BailabUNC/LaHMo/results/revision/photo/DSC_0429.JPG

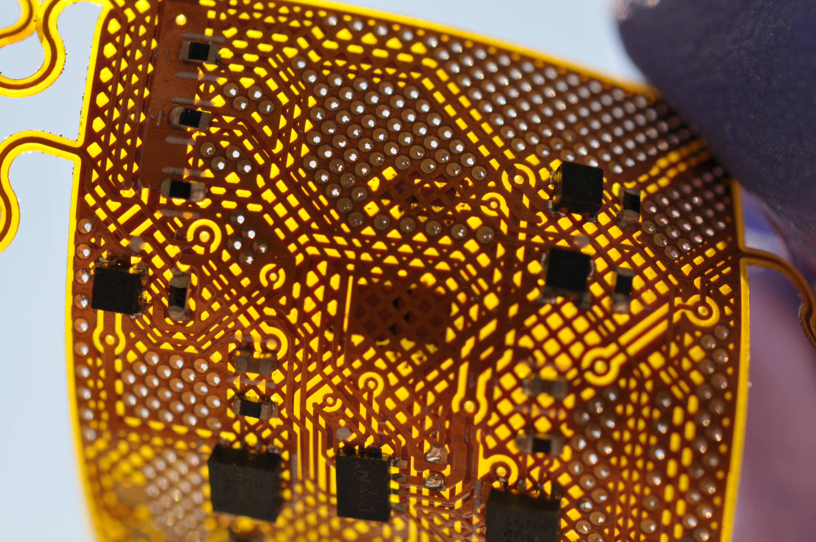
results/revision/photo/DSC_0429.JPG
