BailabUNC/LaHMo/results/revision/photo/DSC_0419.JPG

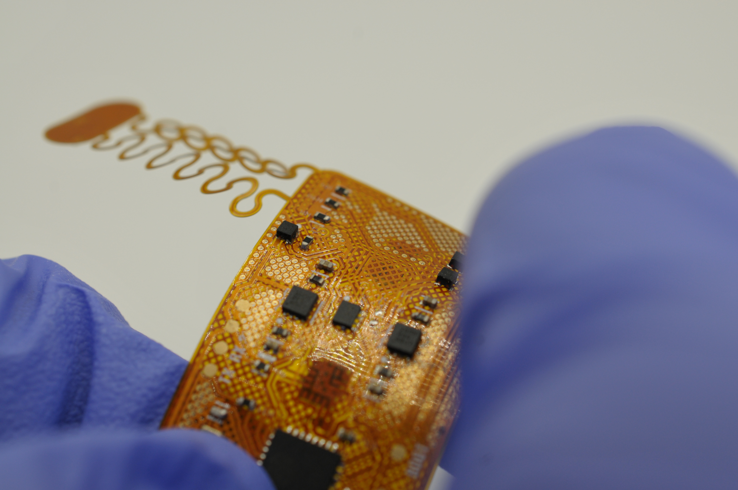
results/revision/photo/DSC_0419.JPG
