BailabUNC/LaHMo/results/revision/new tests/quality/c3_spec.png

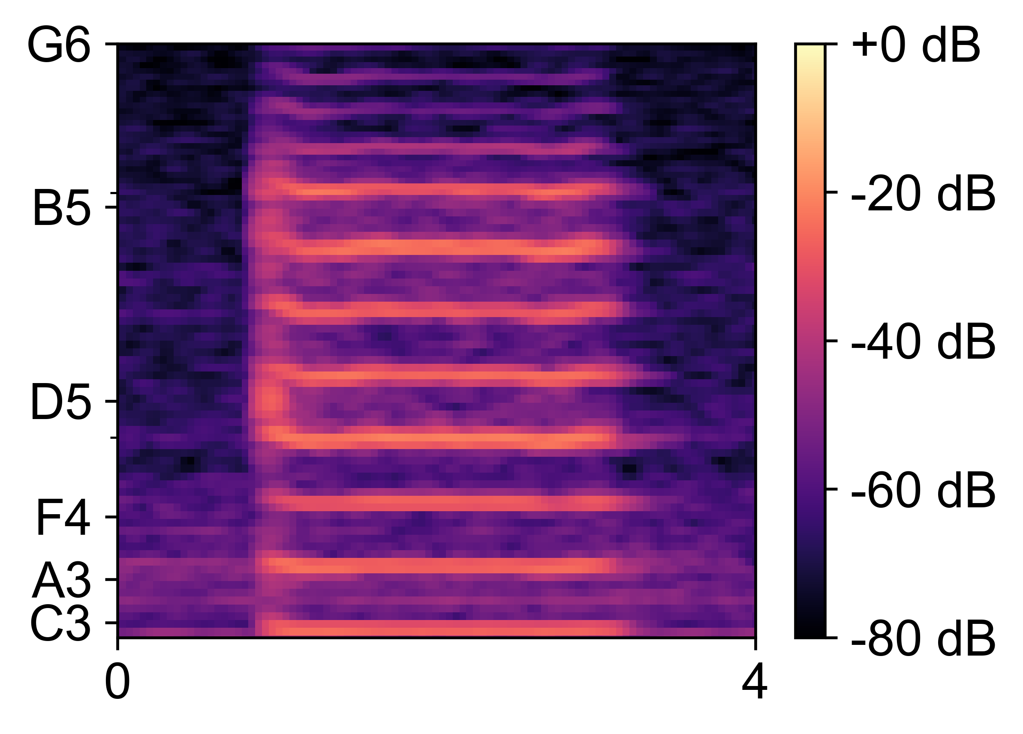
results/revision/new tests/quality/c3_spec.png
