BailabUNC/LaHMo/results/revision/new tests/quality/falsetto_spec.png

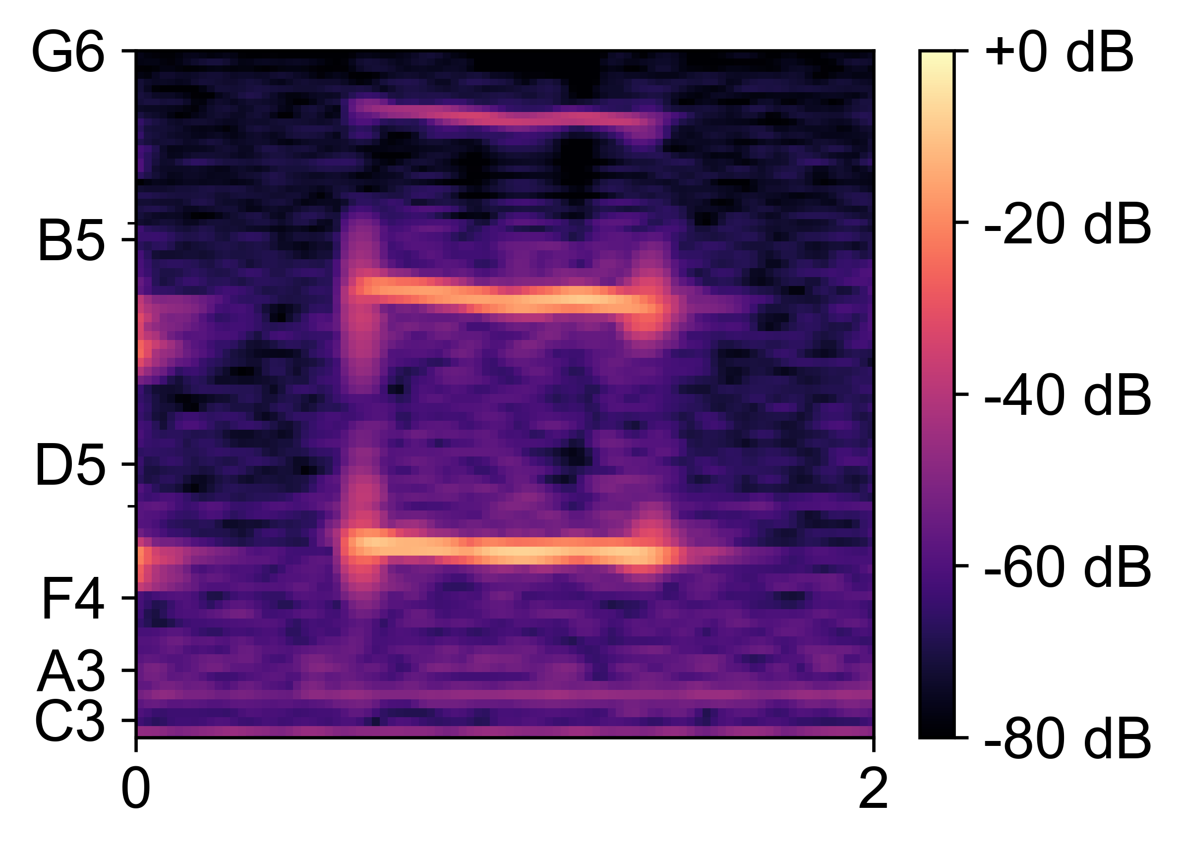
results/revision/new tests/quality/falsetto_spec.png
