BailabUNC/LaHMo/results/revision/new tests/quality/g3_spec.png

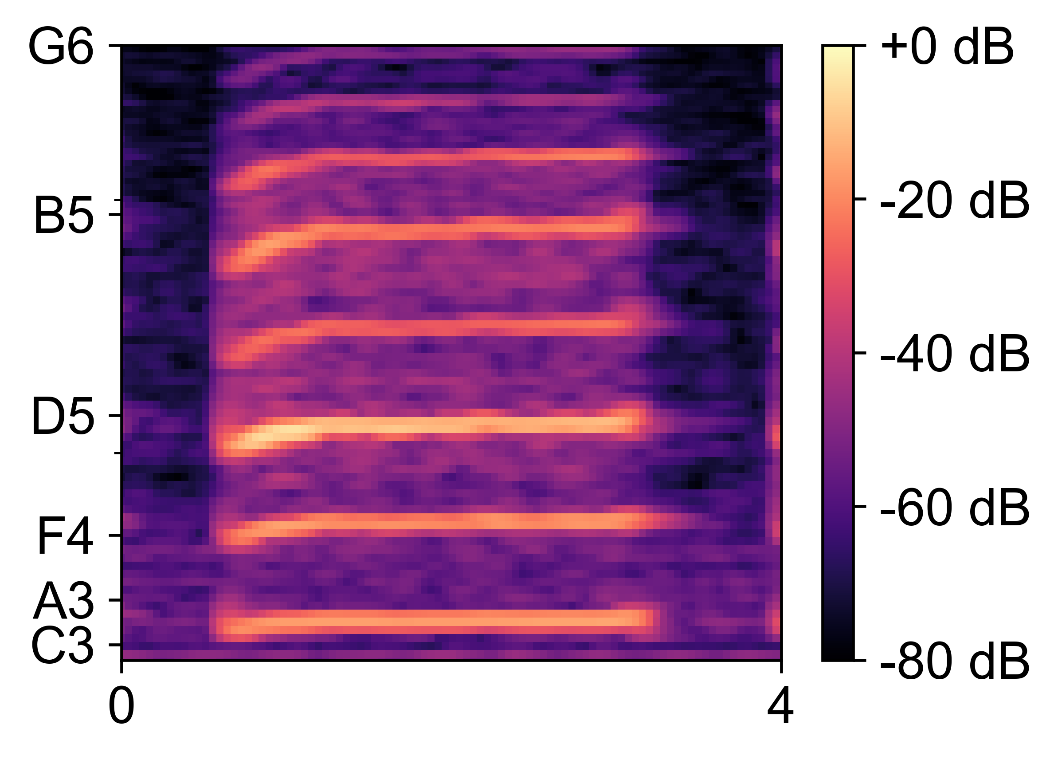
results/revision/new tests/quality/g3_spec.png
