BailabUNC/LaHMo/results/revision/new tests/quality/g4_spec.png

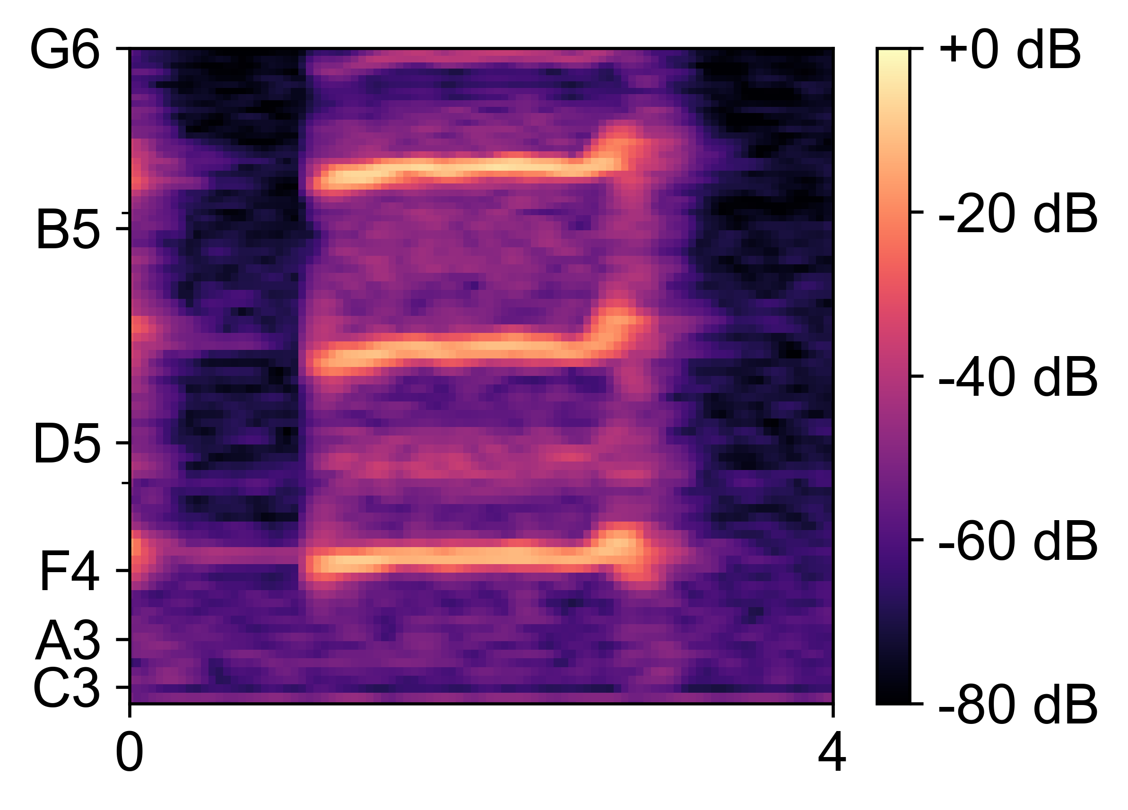
results/revision/new tests/quality/g4_spec.png
