BailabUNC/LaHMo/results/revision/new tests/quality/head_voice_spec.png

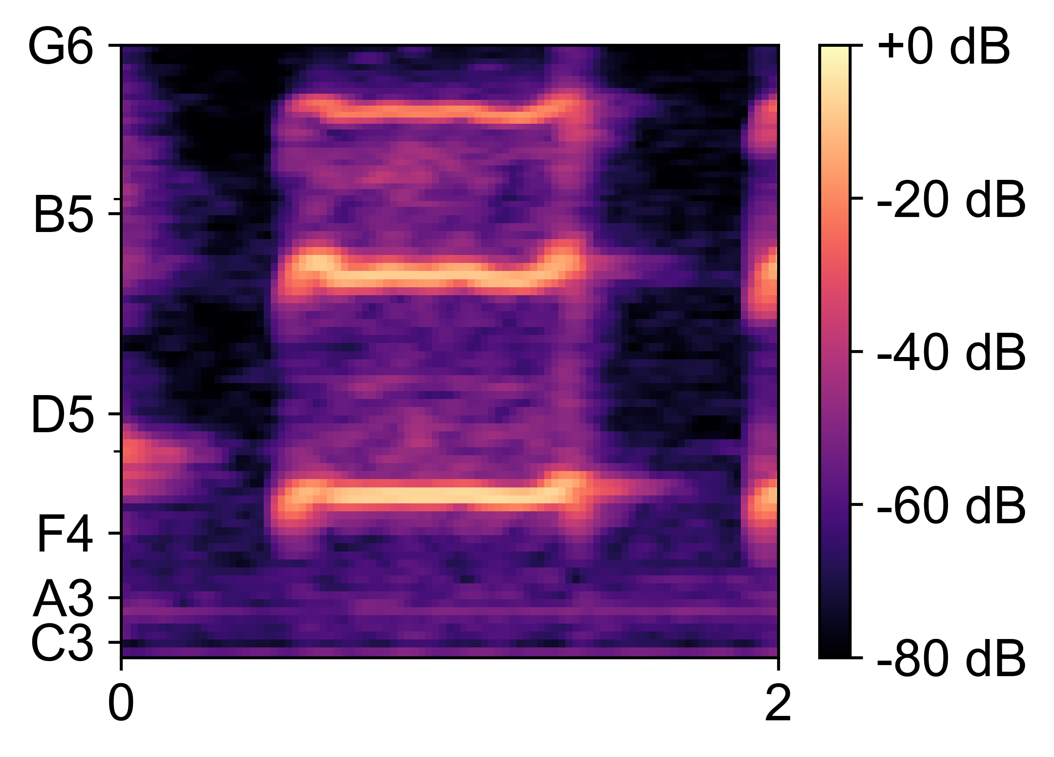
results/revision/new tests/quality/head_voice_spec.png
