BailabUNC/LaHMo/results/revision/new tests/quality/loud_spec.png

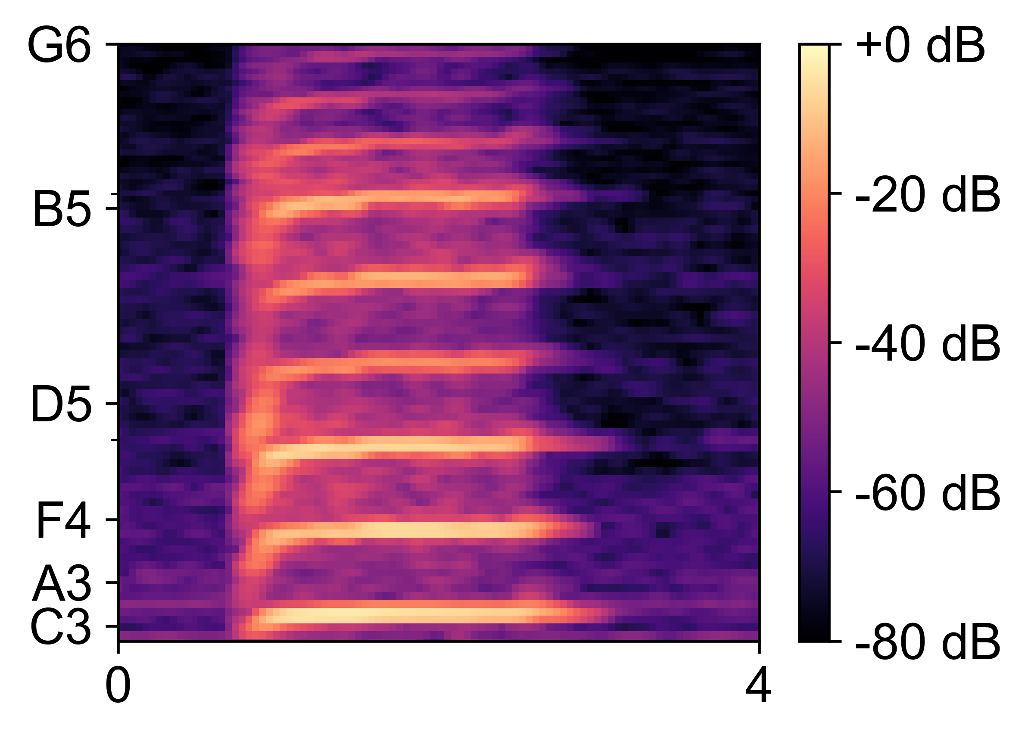
results/revision/new tests/quality/loud_spec.png
