BailabUNC/LaHMo/results/revision/new tests/quality/whisper_spec.png

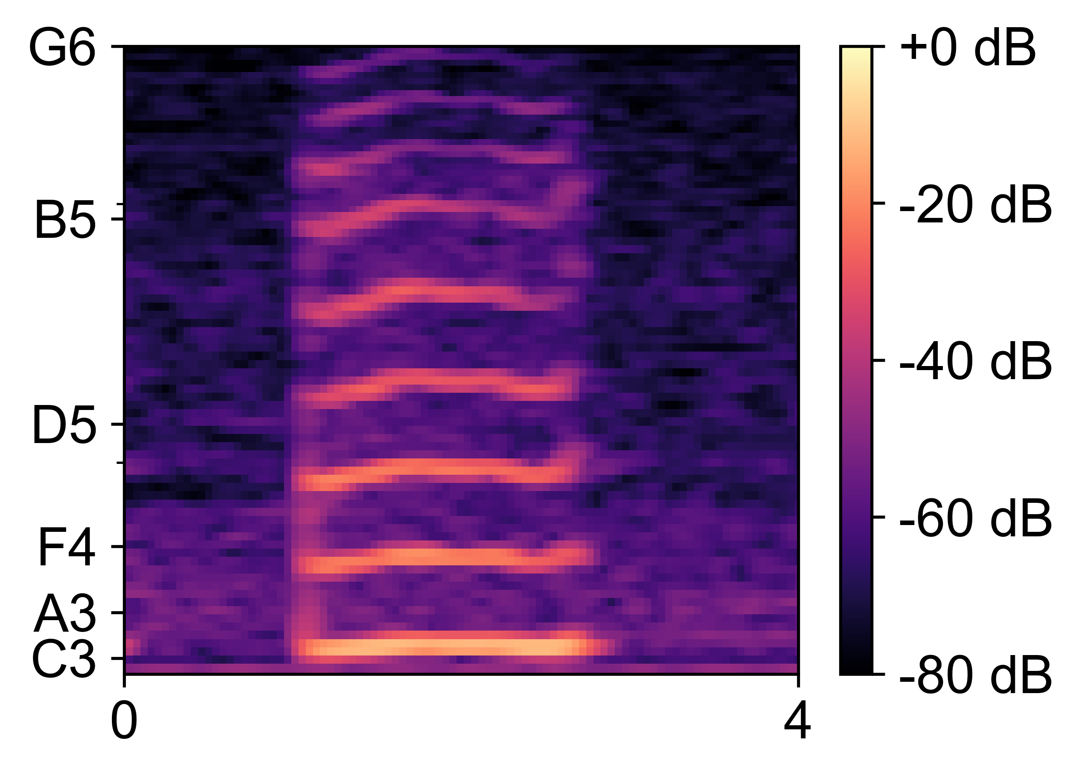
results/revision/new tests/quality/whisper_spec.png
