BailabUNC/LaHMo/results/revision/new tests/video/video1_spec.png

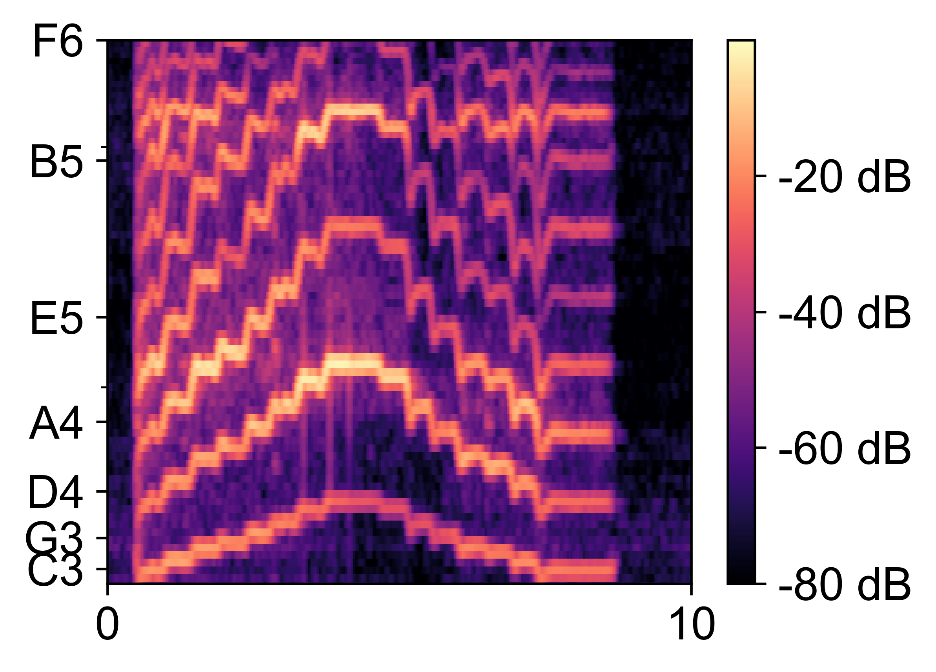
results/revision/new tests/video/video1_spec.png
