BailabUNC/LaHMo/results/revision/new tests/video/video2_spec.png

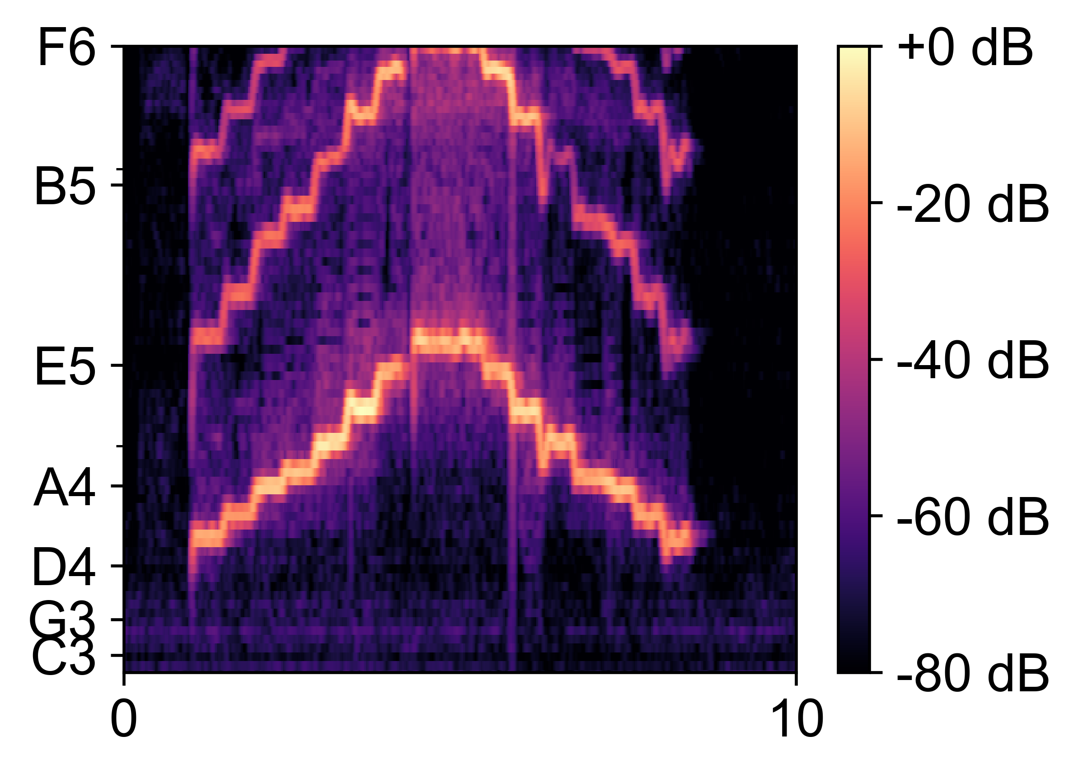
results/revision/new tests/video/video2_spec.png
