BailabUNC/LaHMo/results/fig2/preprocessing_steps/filtered_data.png

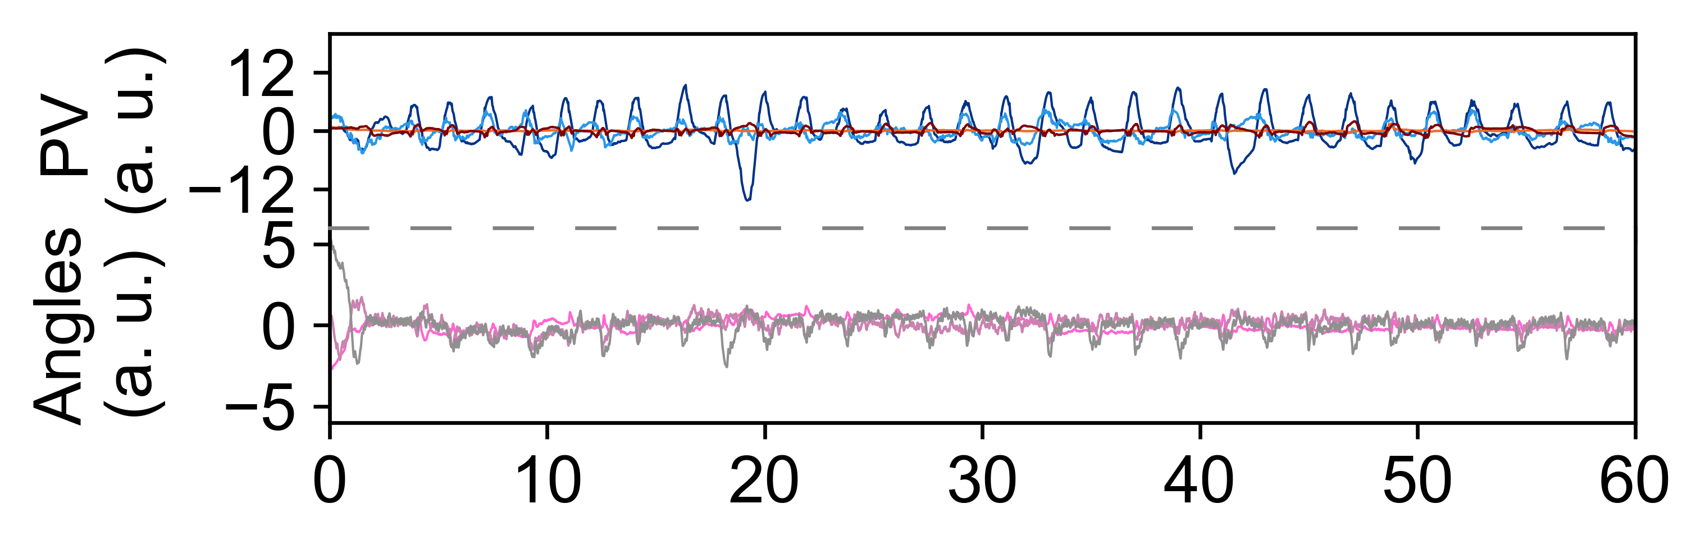
results/fig2/preprocessing_steps/filtered_data.png
