BailabUNC/LaHMo/results/fig2/preprocessing_steps/normalized_data.png

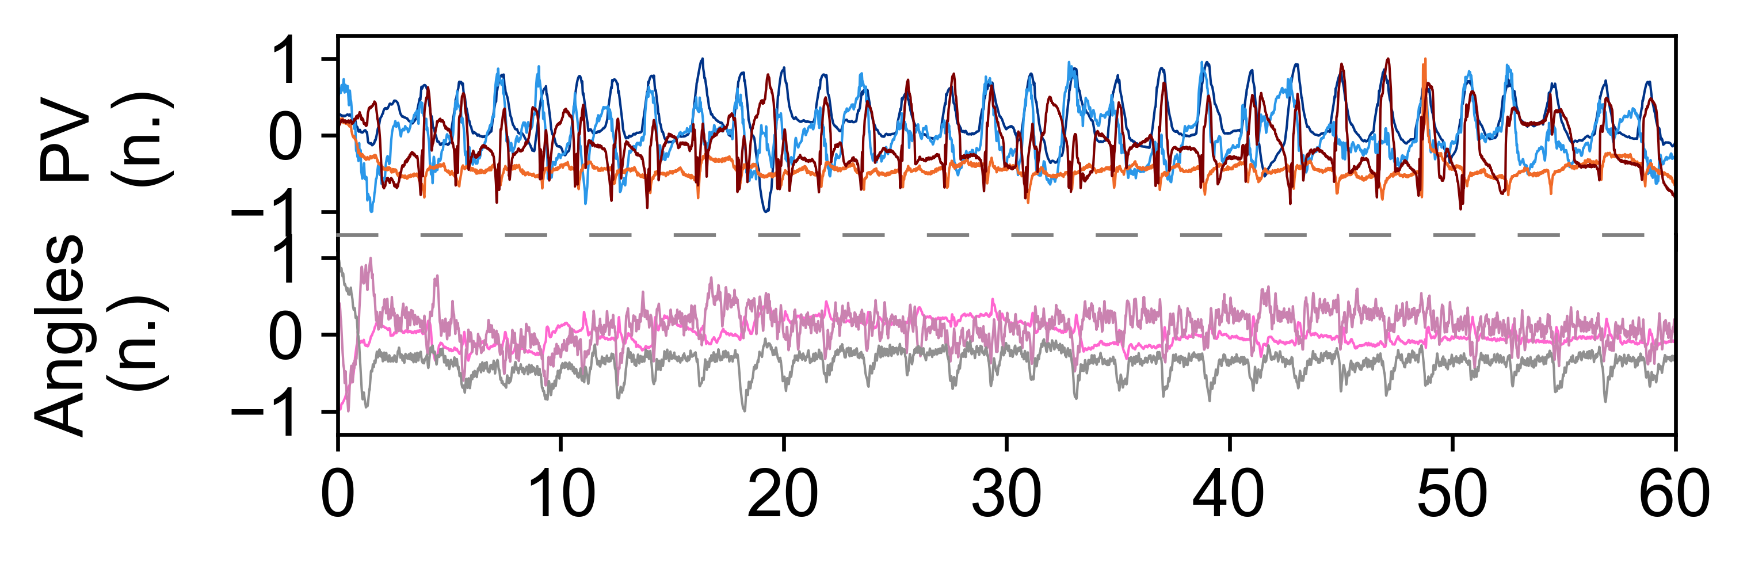
results/fig2/preprocessing_steps/normalized_data.png
