BailabUNC/LaHMo/results/fig2/preprocessing_steps/preprocessing_steps.png

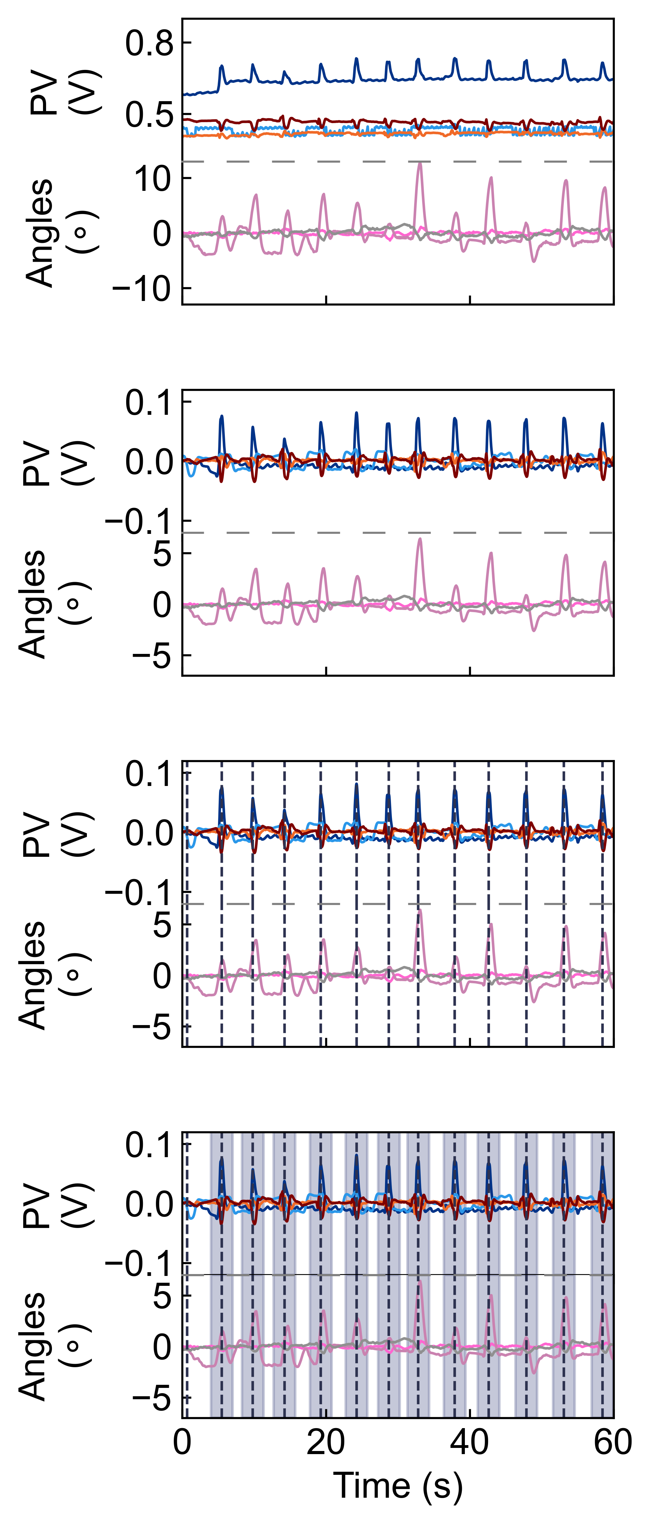
results/fig2/preprocessing_steps/preprocessing_steps.png
