BailabUNC/LaHMo/results/fig2/preprocessing_steps/preprocessing_steps_1.png

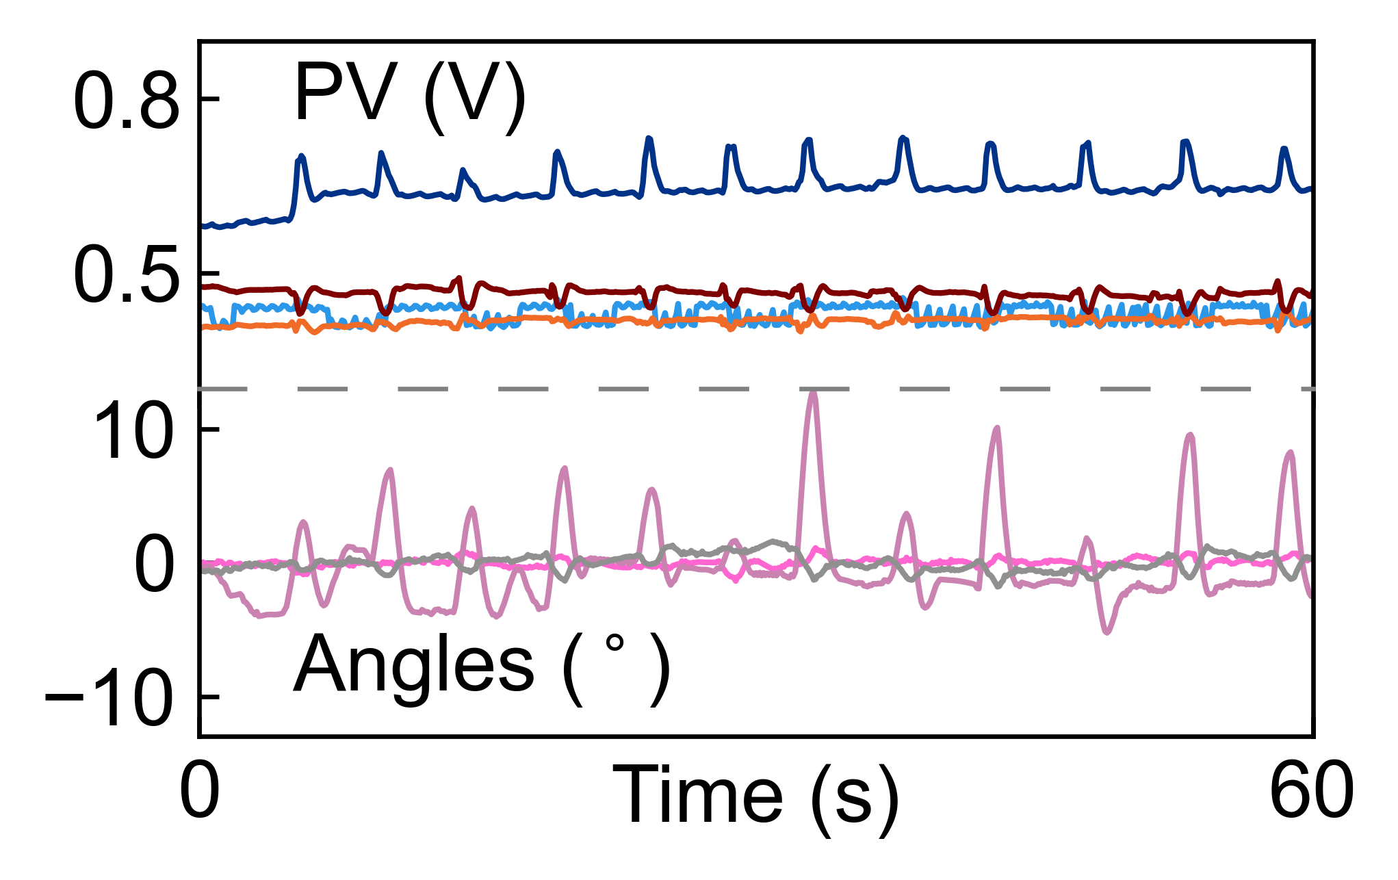
results/fig2/preprocessing_steps/preprocessing_steps_1.png
