BailabUNC/LaHMo/results/fig2/preprocessing_steps/preprocessing_steps_2.png

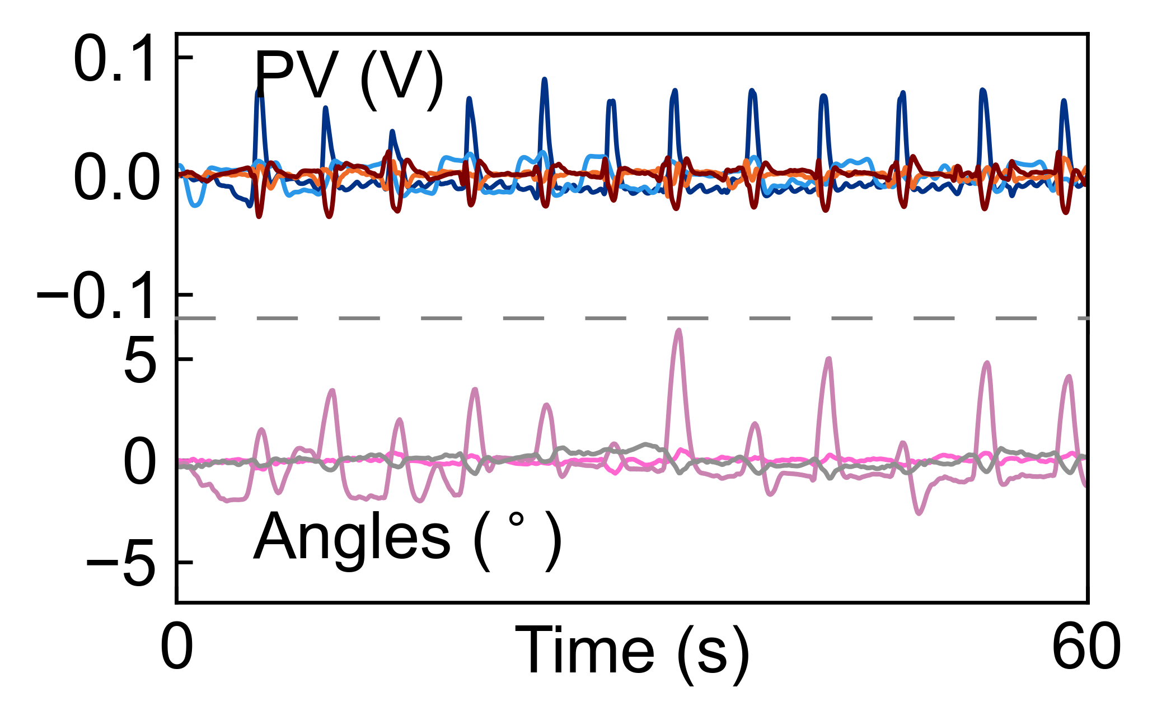
results/fig2/preprocessing_steps/preprocessing_steps_2.png
