BailabUNC/LaHMo/results/fig2/preprocessing_steps/preprocessing_steps_3.png

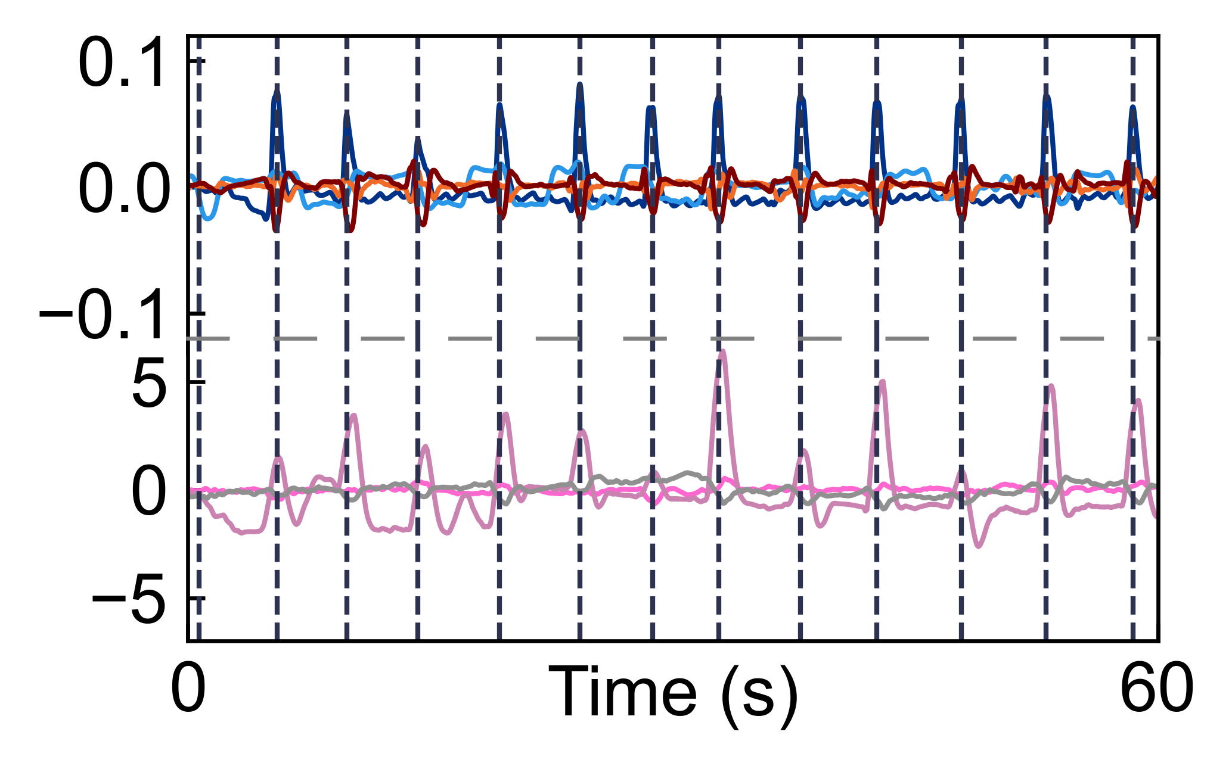
results/fig2/preprocessing_steps/preprocessing_steps_3.png
