BailabUNC/LaHMo/results/fig2/preprocessing_steps/raw_data.png

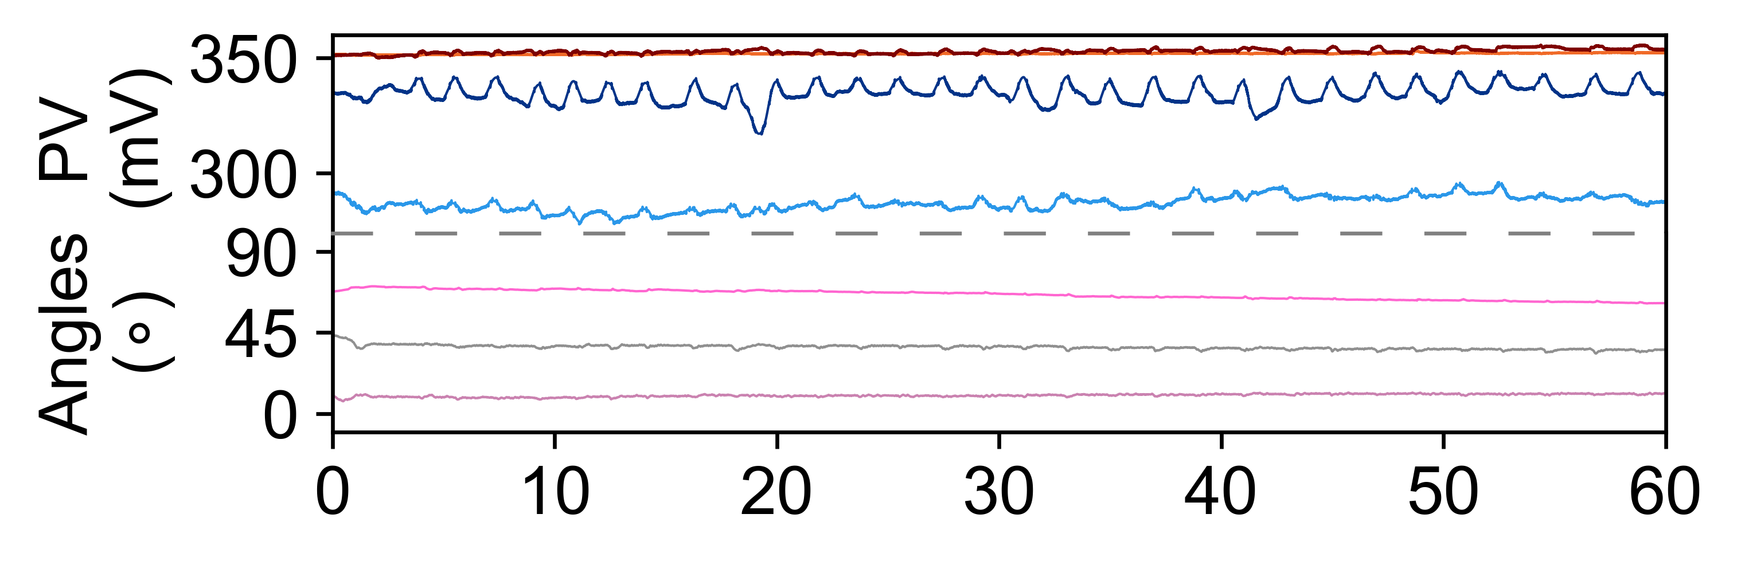
results/fig2/preprocessing_steps/raw_data.png
