BailabUNC/LaHMo/results/fig2/preprocessing_steps/selected_data.png

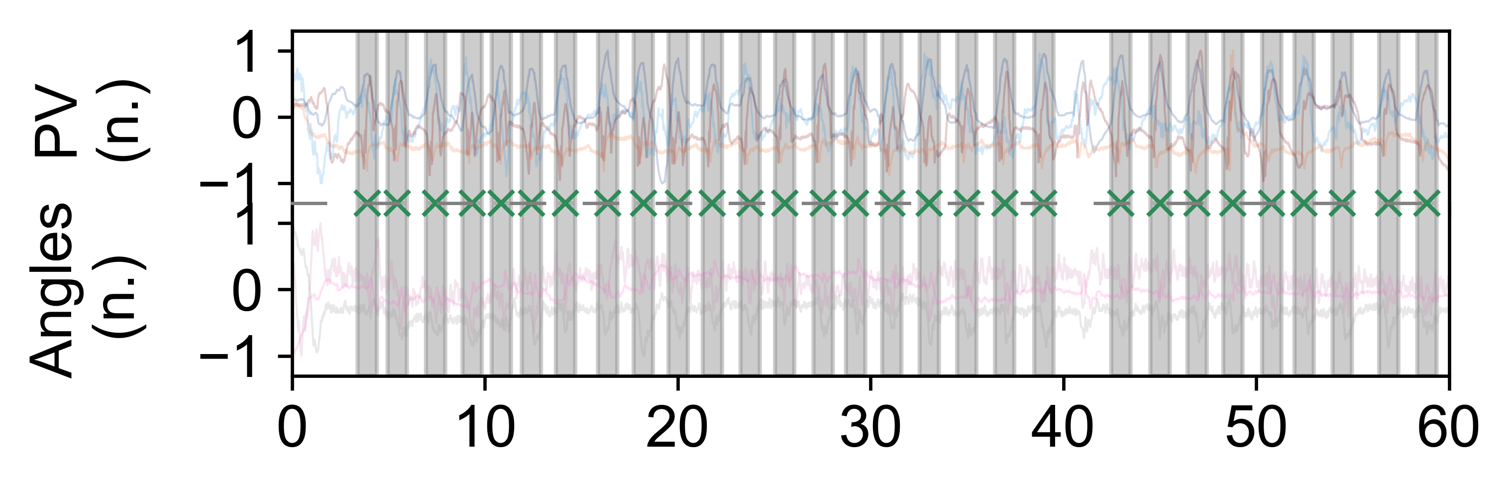
results/fig2/preprocessing_steps/selected_data.png
