BailabUNC/LaHMo/monte-carlo/monte-carlo/result/bump_loc_height_matrix.png

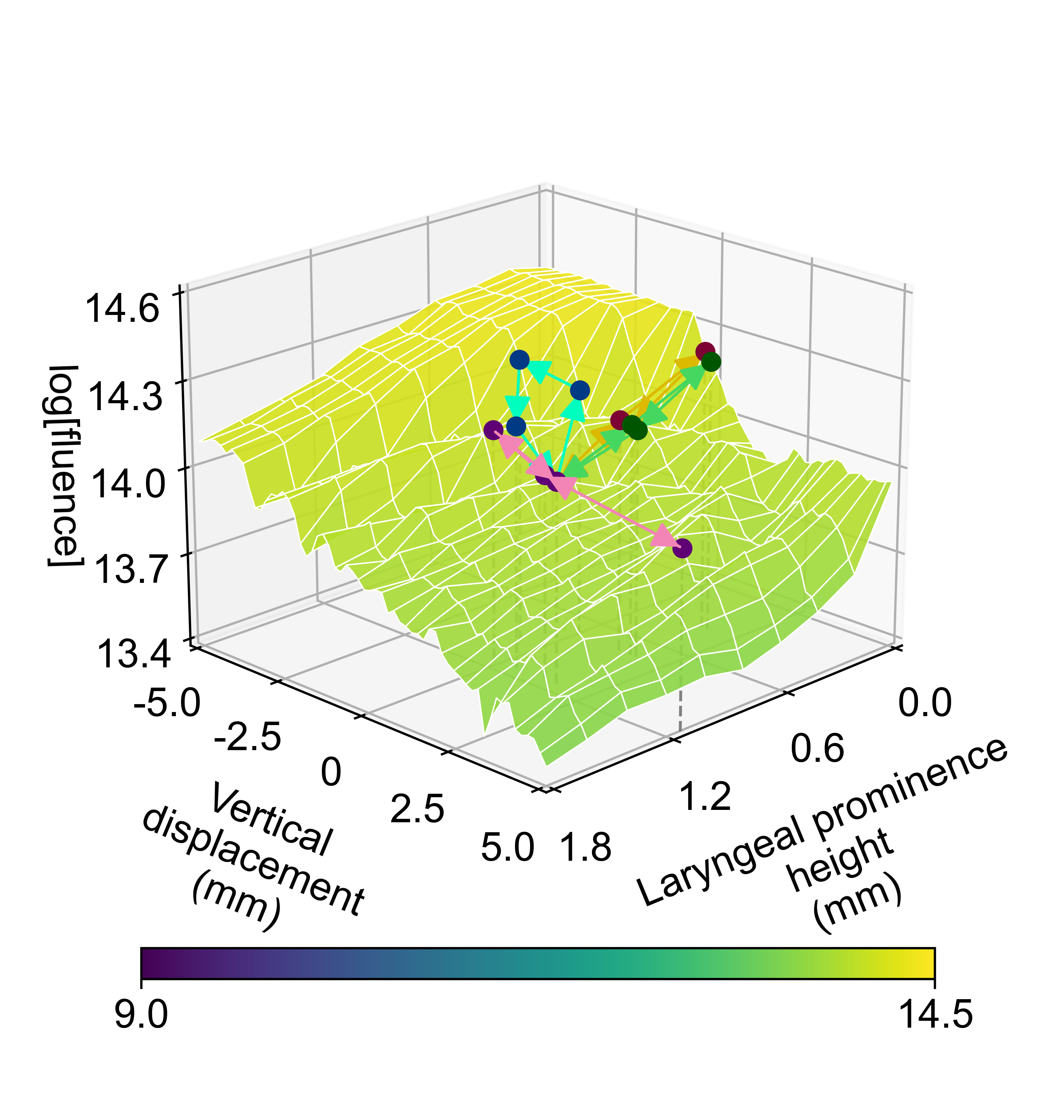
monte-carlo/monte-carlo/result/bump_loc_height_matrix.png
