BailabUNC/LaHMo/monte-carlo/monte-carlo/result/damping_scatter_0_0_1000.png

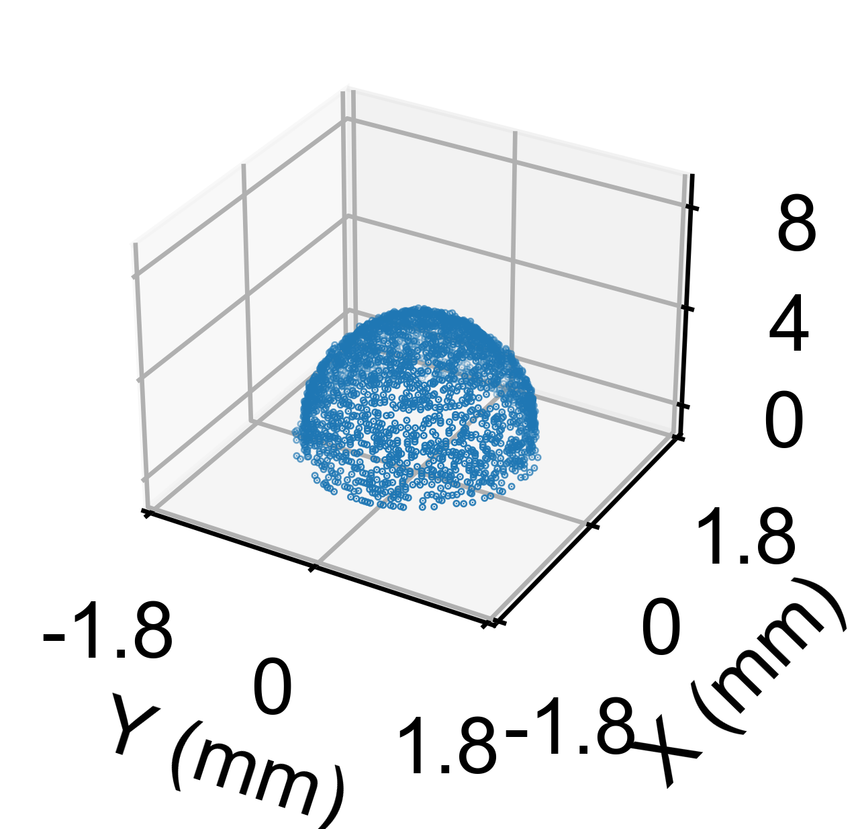
monte-carlo/monte-carlo/result/damping_scatter_0_0_1000.png
