BailabUNC/LaHMo/monte-carlo/monte-carlo/result/dry_cough_cycle.png

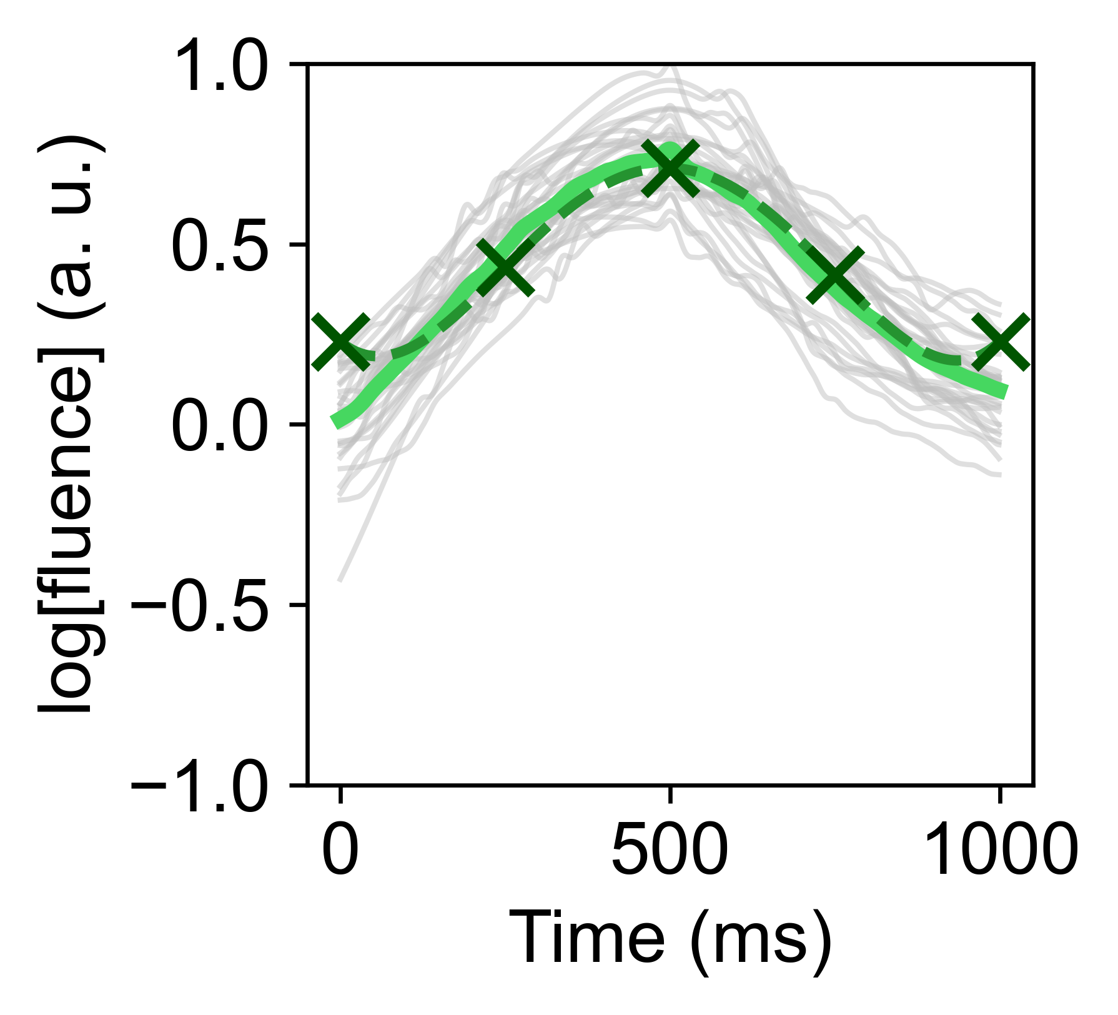
monte-carlo/monte-carlo/result/dry_cough_cycle.png
