BailabUNC/LaHMo/monte-carlo/monte-carlo/result/dry_cough_profile.png

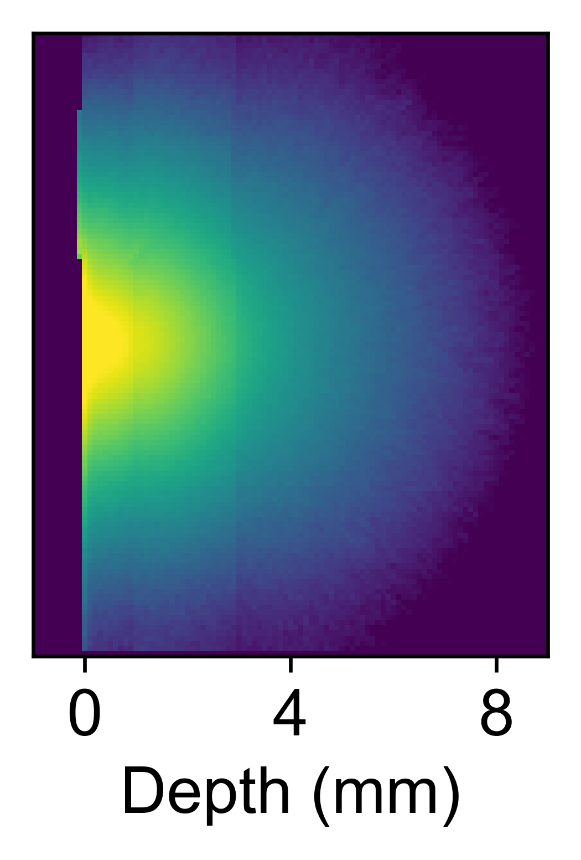
monte-carlo/monte-carlo/result/dry_cough_profile.png
