BailabUNC/LaHMo/monte-carlo/monte-carlo/result/swallow_profile.png

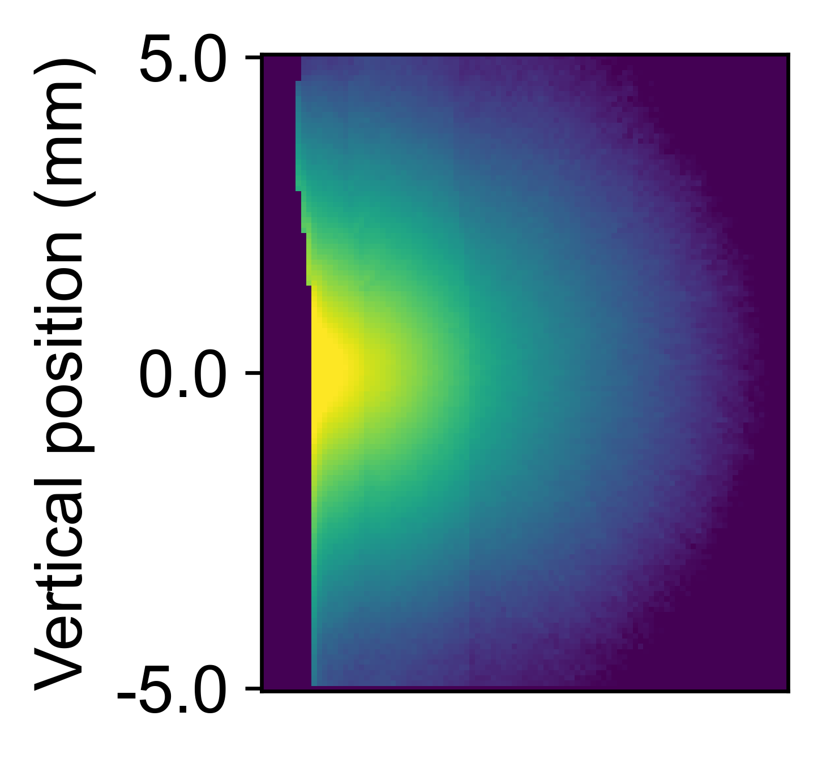
monte-carlo/monte-carlo/result/swallow_profile.png
