BailabUNC/LaHMo/monte-carlo/monte-carlo/result/throat_clear_cycle.png

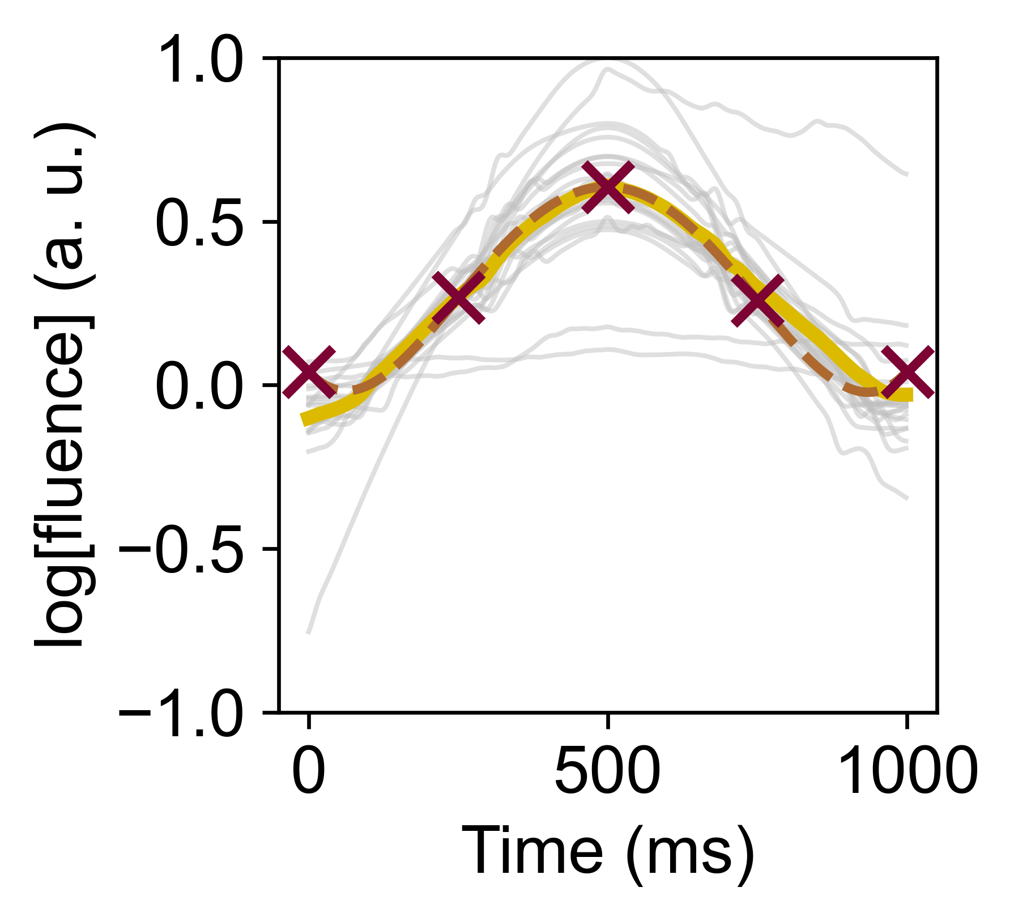
monte-carlo/monte-carlo/result/throat_clear_cycle.png
