BailabUNC/LaHMo/monte-carlo/monte-carlo/result/throat_clear_profile.png

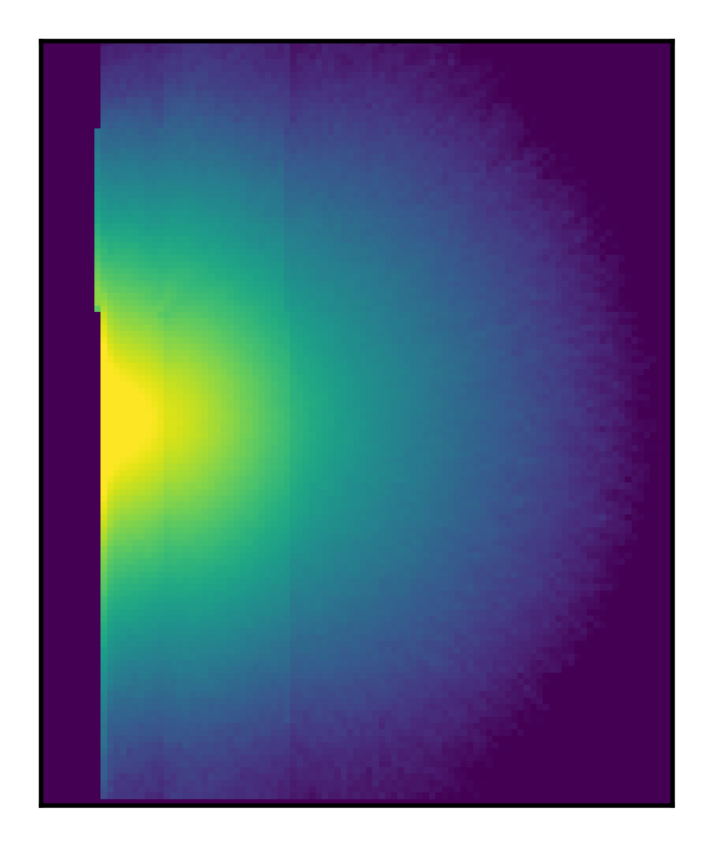
monte-carlo/monte-carlo/result/throat_clear_profile.png
