BailabUNC/LaHMo/monte-carlo/monte-carlo/result/walking_cycle.png

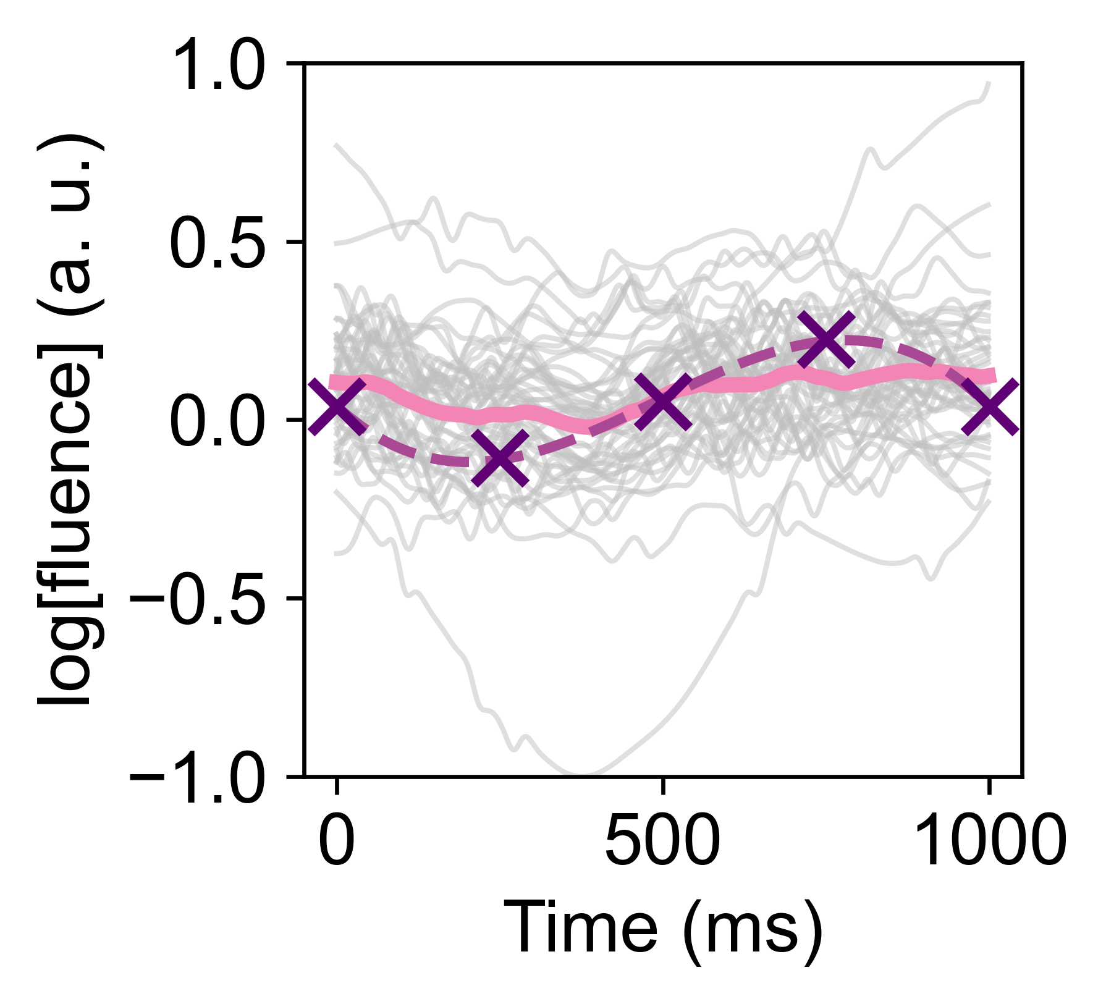
monte-carlo/monte-carlo/result/walking_cycle.png
