BailabUNC/LaHMo/monte-carlo/monte-carlo/result/walking_profile.png

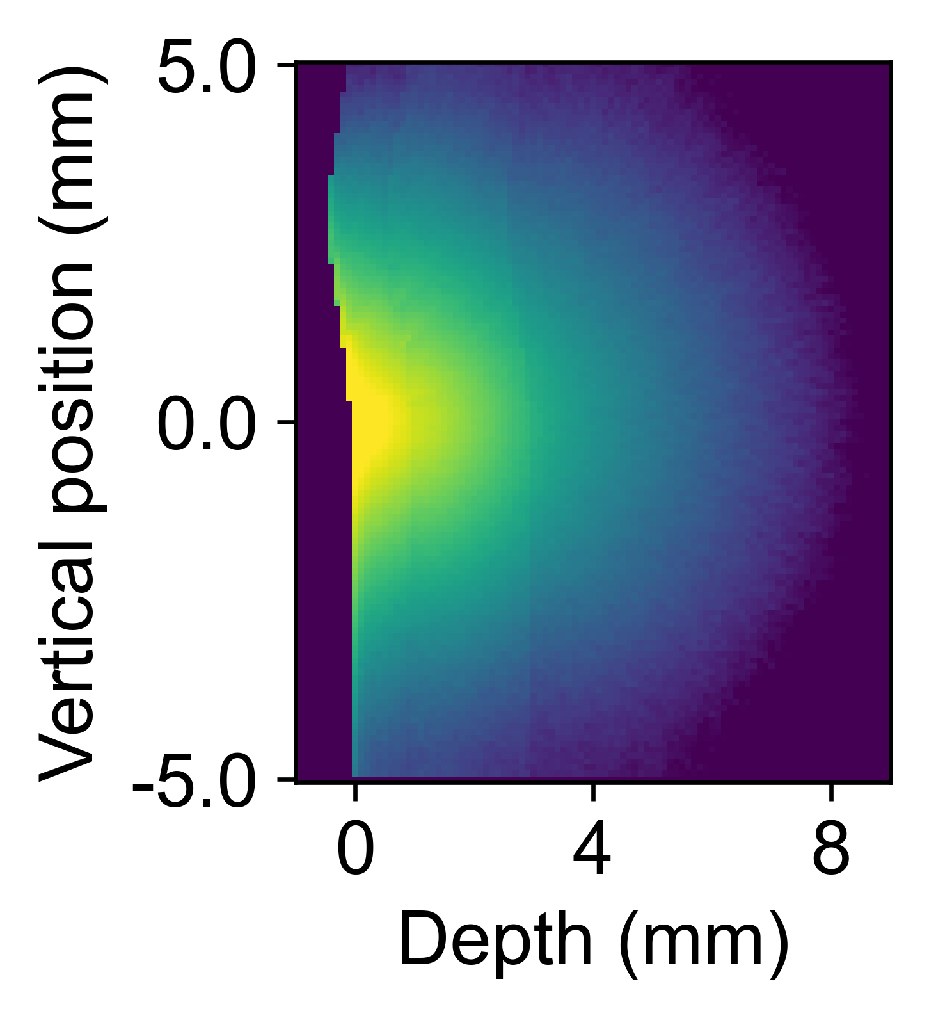
monte-carlo/monte-carlo/result/walking_profile.png
