BailabUNC/LaHMo/results/fig1/2.png

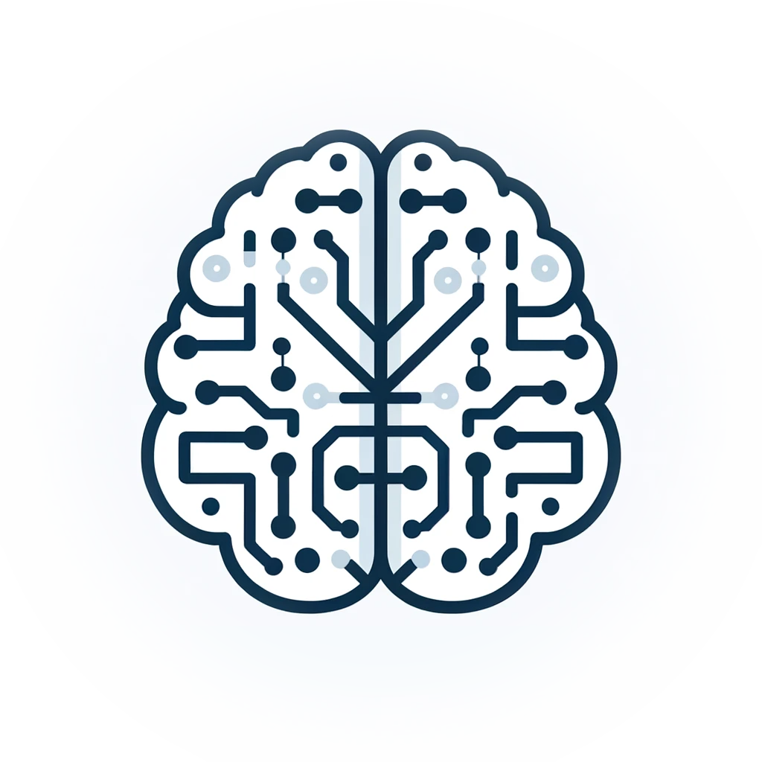
results/fig1/2.png
