BailabUNC/LaHMo/results/fig1/3.png

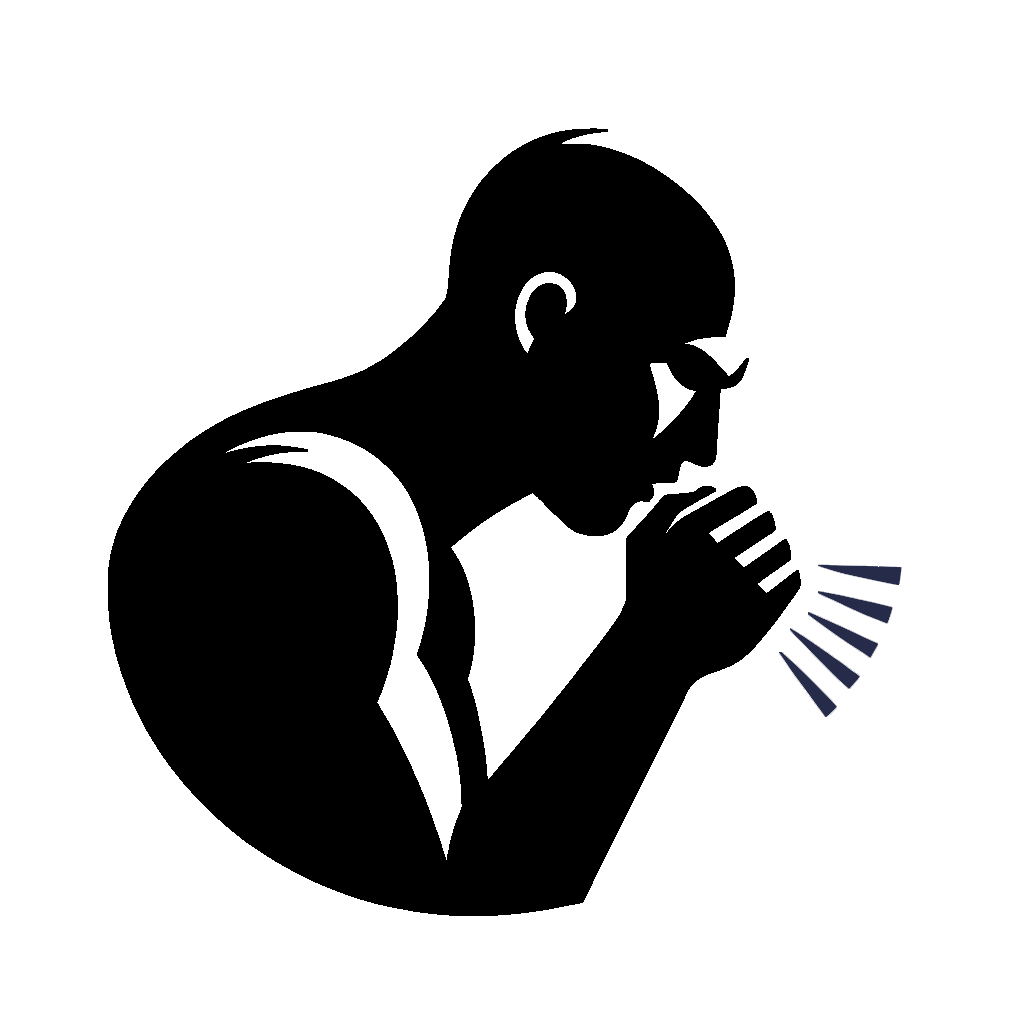
results/fig1/3.png
