BailabUNC/LaHMo/results/fig1/4.png

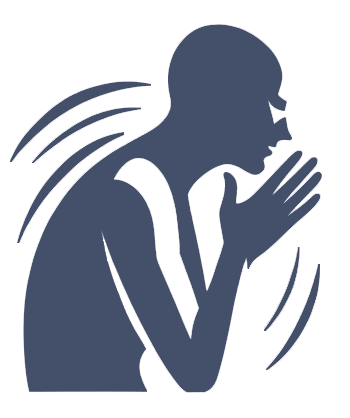
results/fig1/4.png
