BailabUNC/LaHMo/results/fig1/5.png

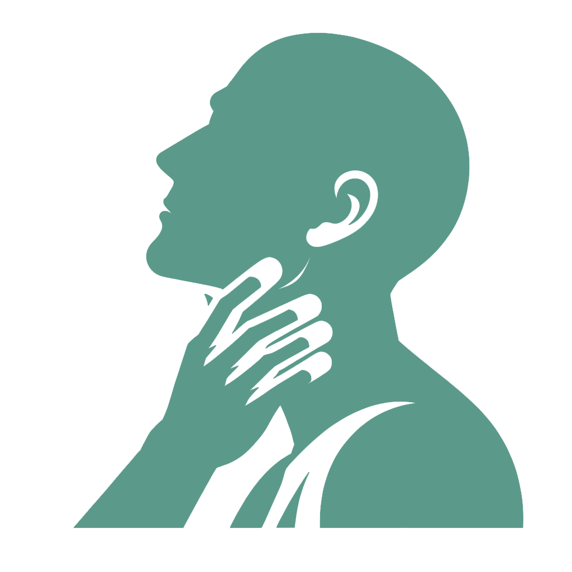
results/fig1/5.png
