BailabUNC/LaHMo/results/fig1/6.png

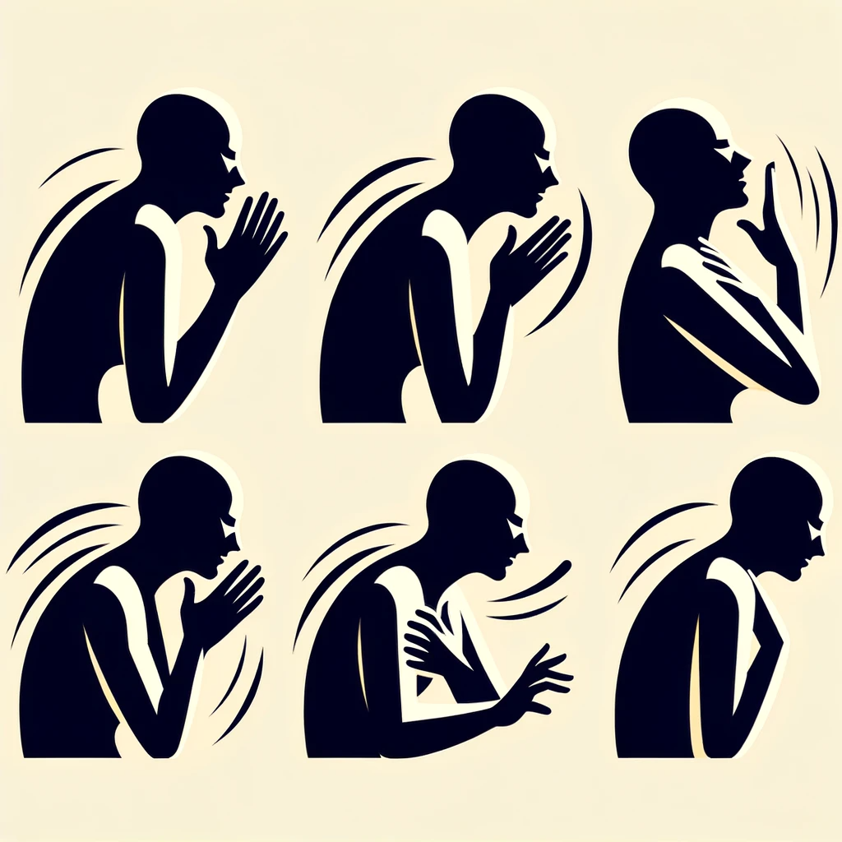
results/fig1/6.png
