BailabUNC/LaHMo/results/fig1/7.png

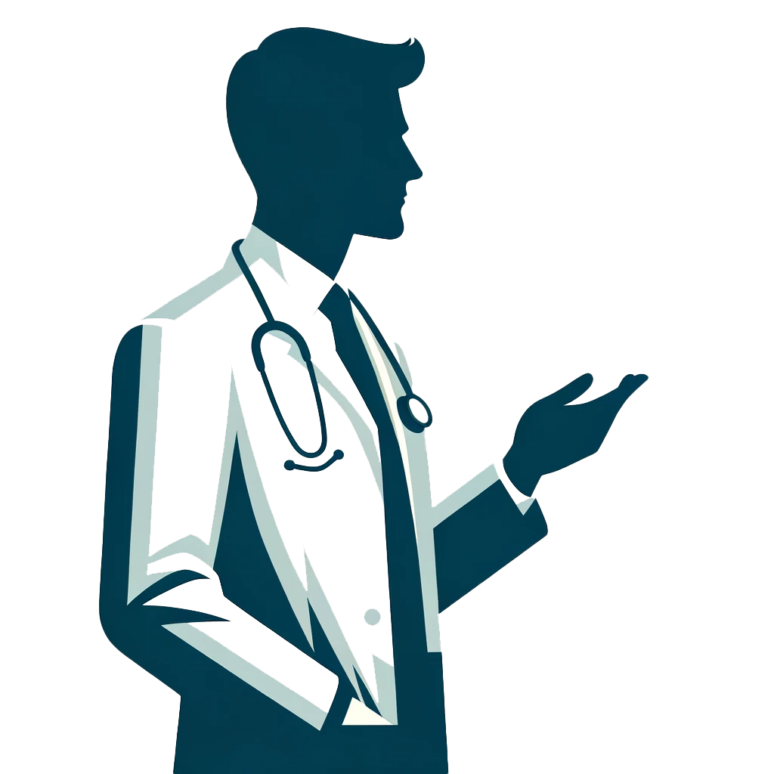
results/fig1/7.png
