BailabUNC/LaHMo/results/fig1/exploded.jpg

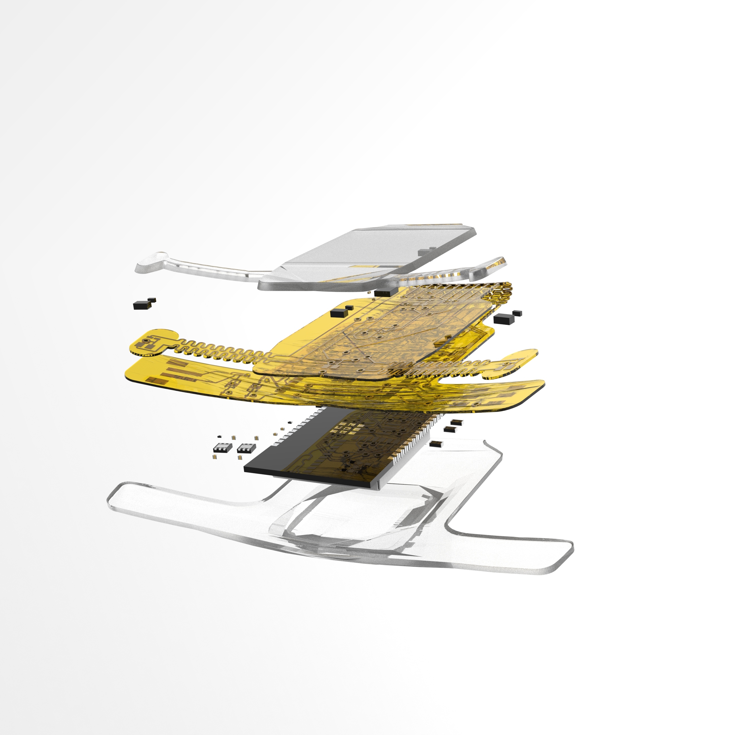
results/fig1/exploded.jpg
