BailabUNC/LaHMo/results/fig1/P3.png

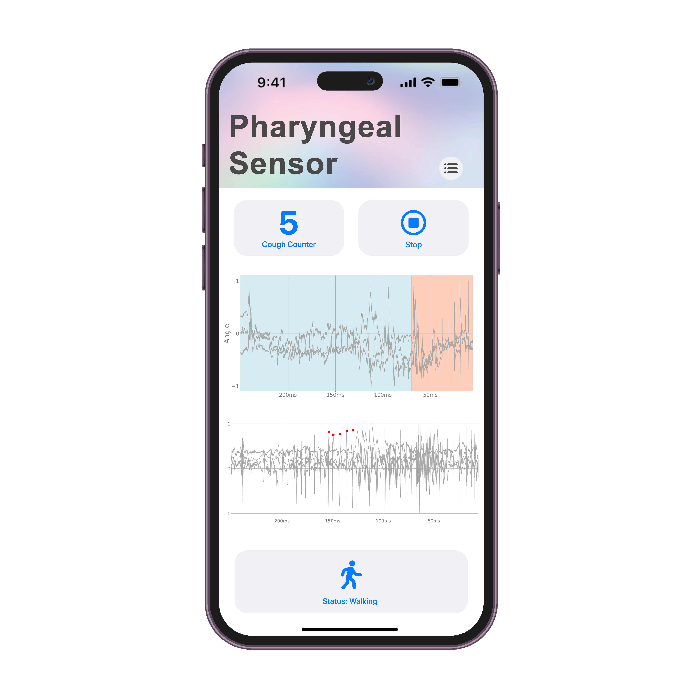
results/fig1/P3.png
