BailabUNC/LaHMo/results/fig1/stacked.2.jpg

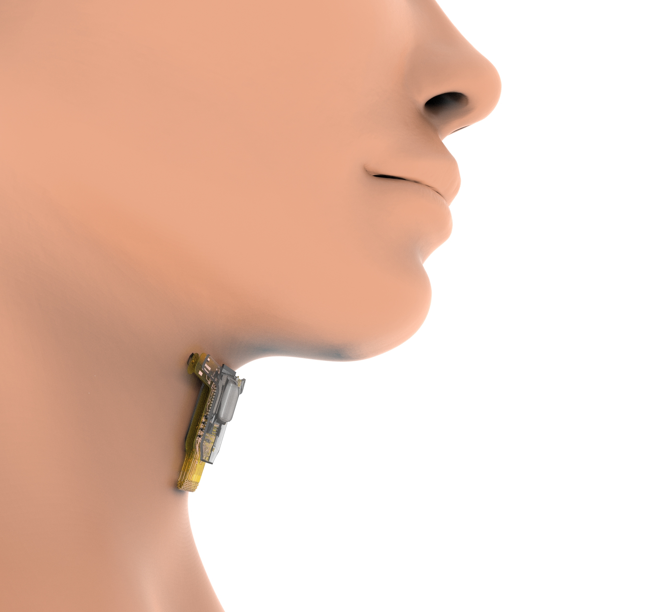
results/fig1/stacked.2.jpg
