BailabUNC/LaHMo/results/fig2/device.png

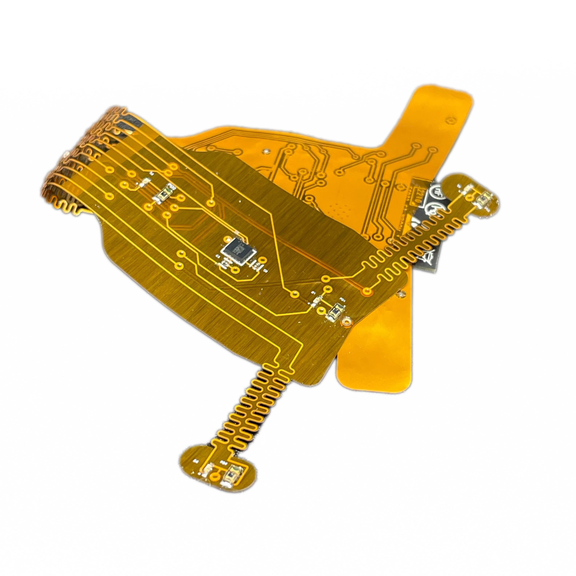
results/fig2/device.png
