BailabUNC/LaHMo/results/fig2/IMG_6159.jpg

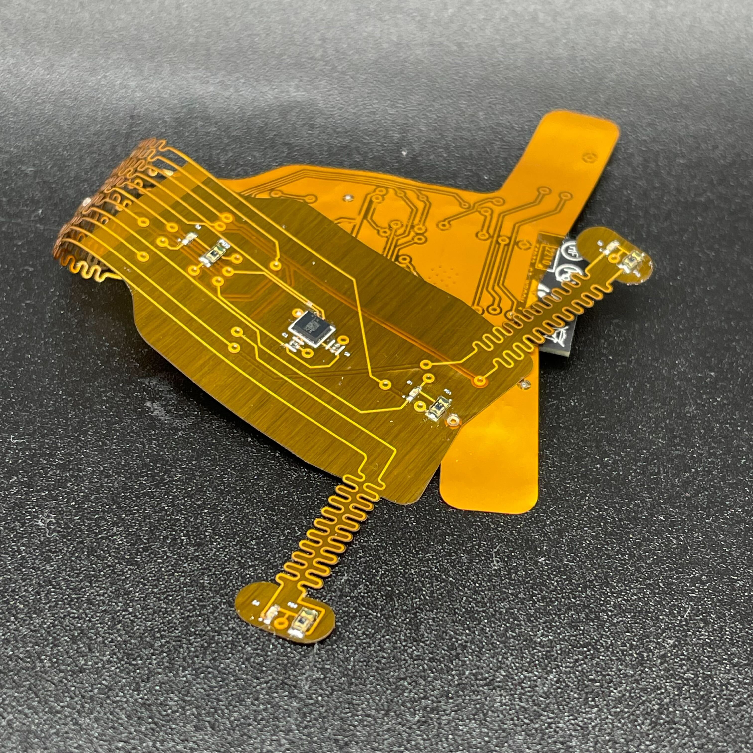
results/fig2/IMG_6159.jpg
