BailabUNC/LaHMo/results/fig2/imu.4.jpg

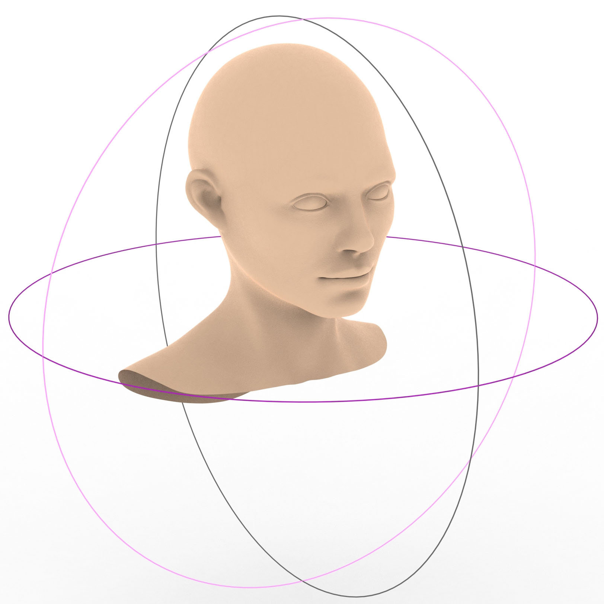
results/fig2/imu.4.jpg
