BailabUNC/LaHMo/results/fig2/map.3.jpg

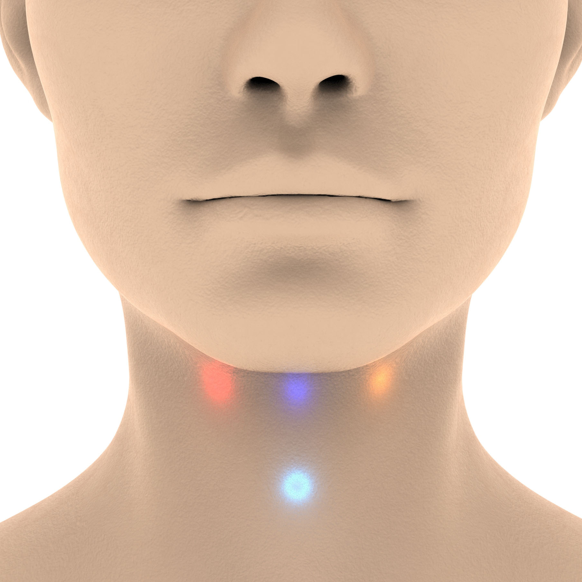
results/fig2/map.3.jpg
