BailabUNC/LaHMo/results/fig2/preprocessed/all.png

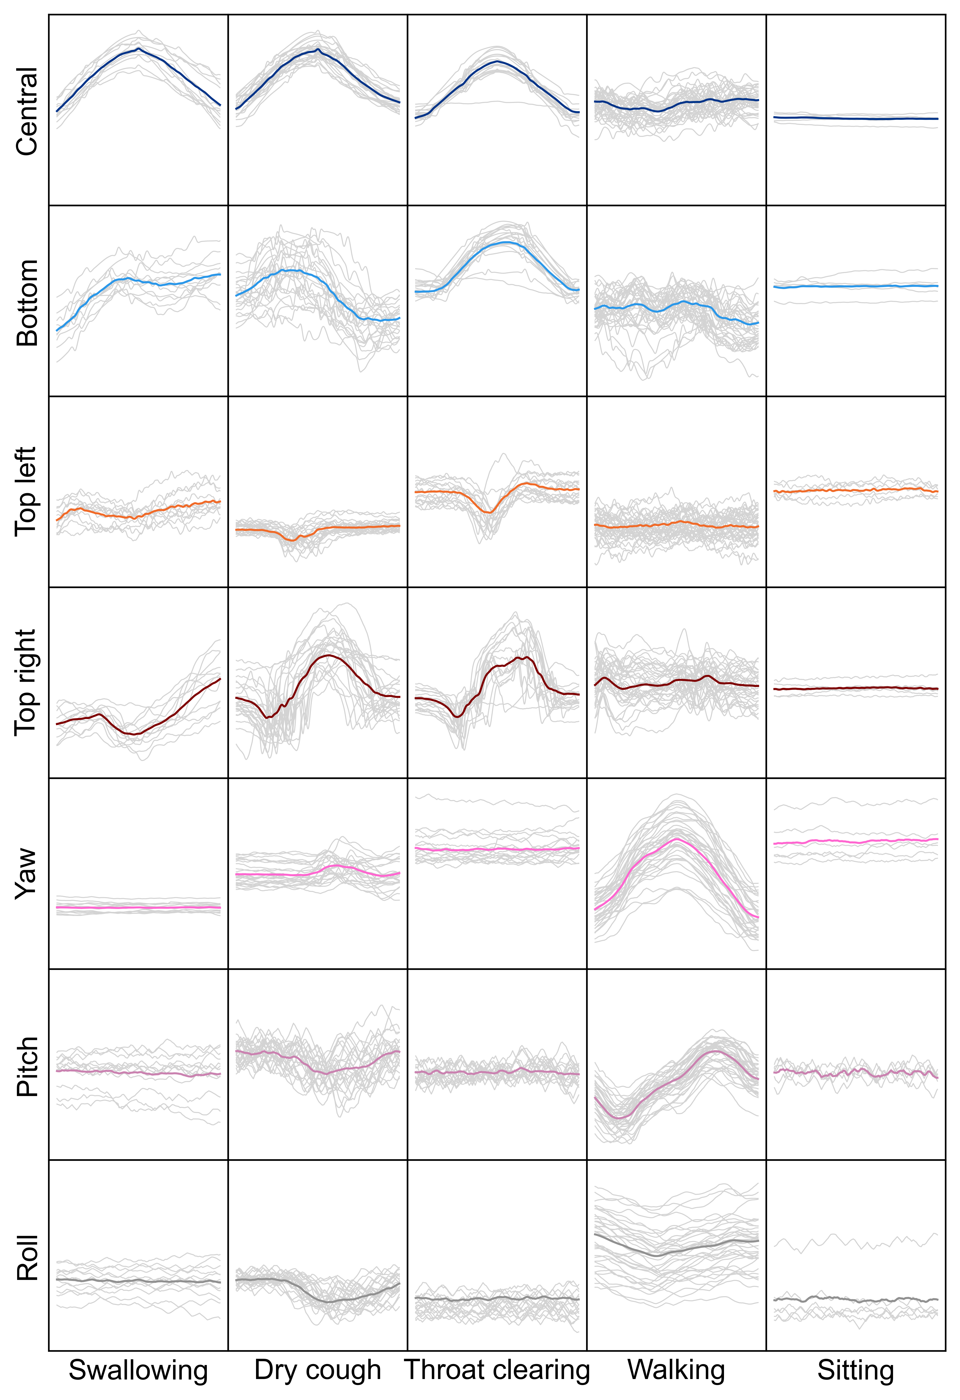
results/fig2/preprocessed/all.png
