BailabUNC/LaHMo/results/fig3/acc_all_frnn.png

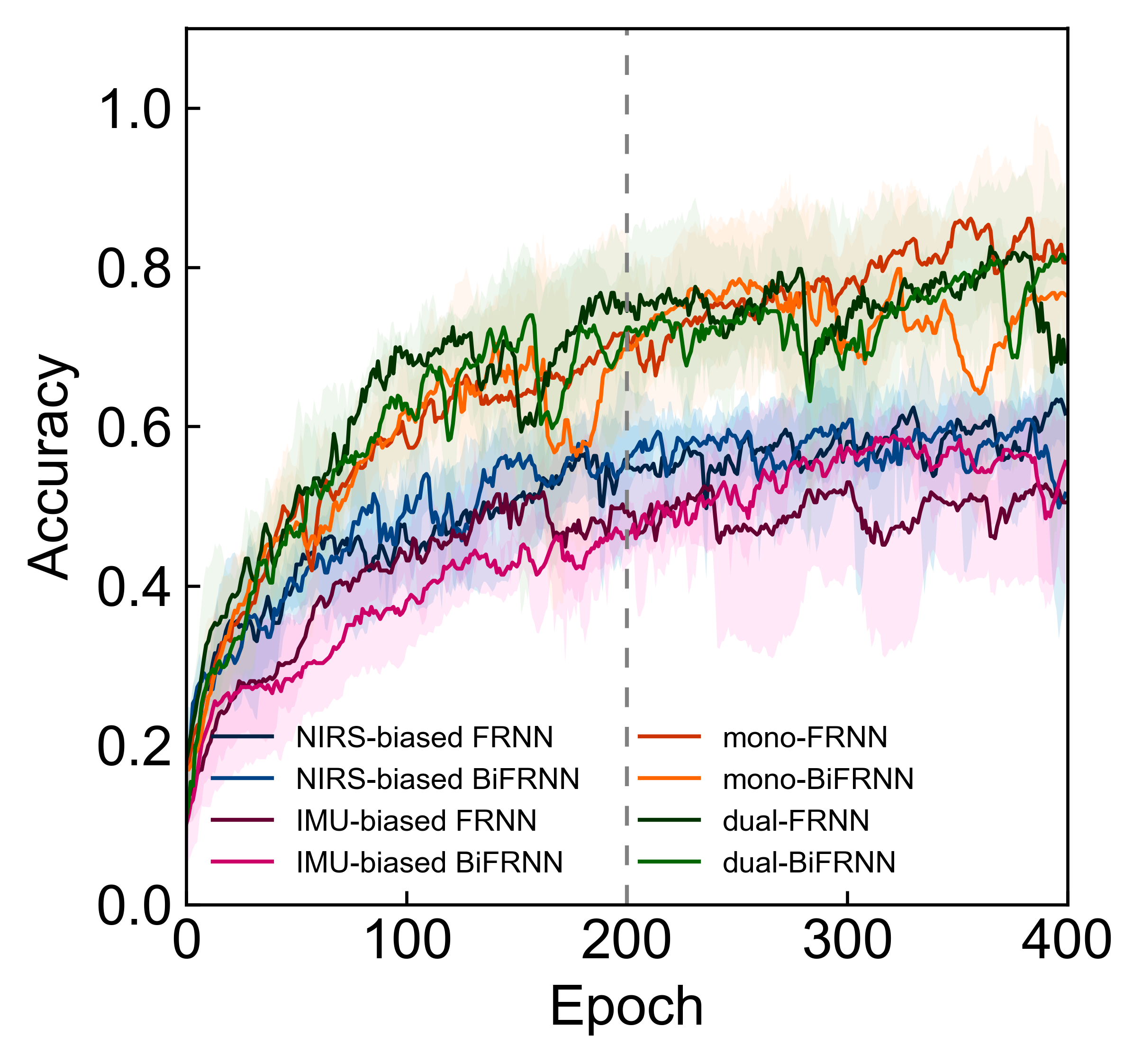
results/fig3/acc_all_frnn.png
