BailabUNC/LaHMo/results/fig3/acc_all_gru.png

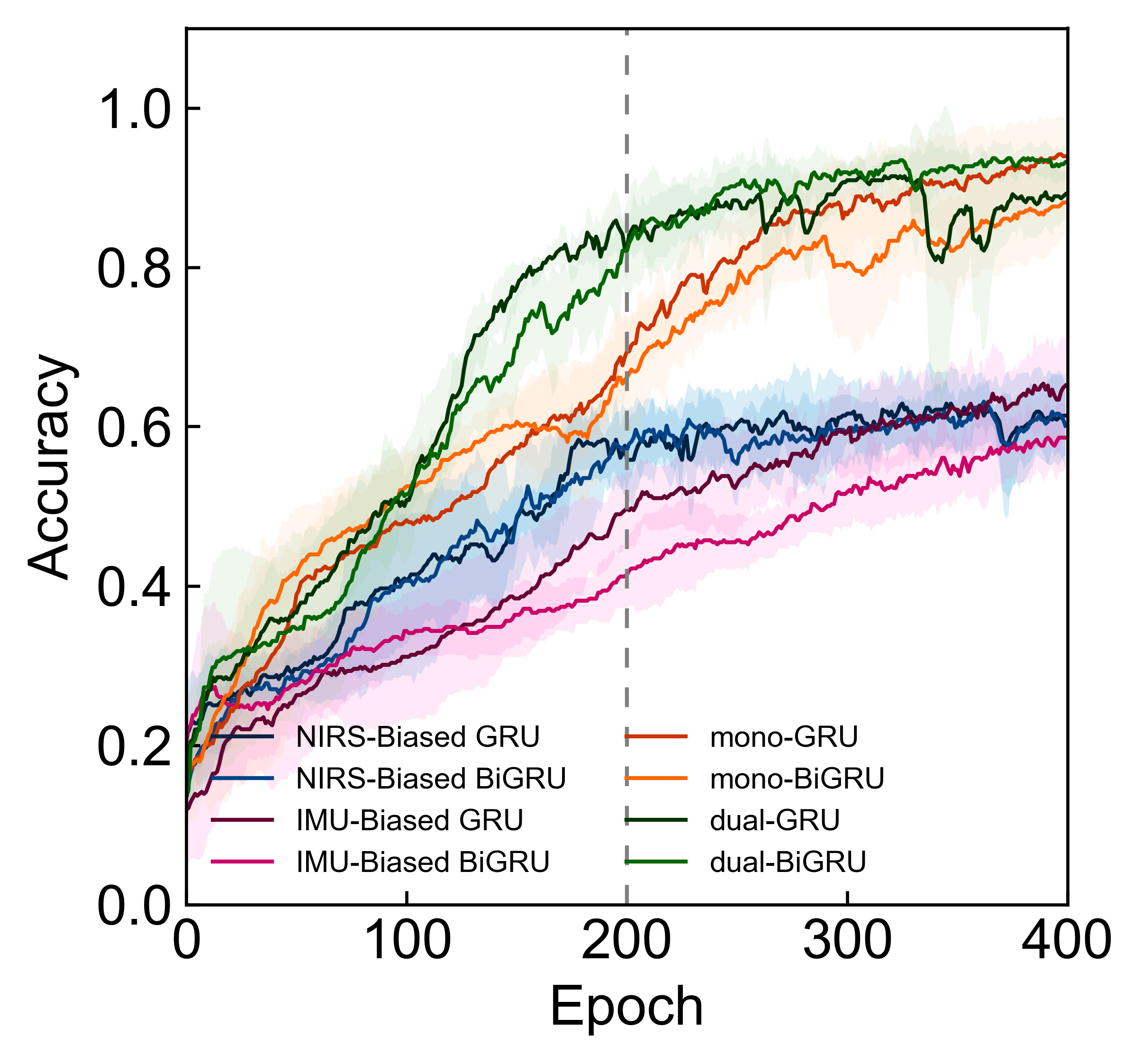
results/fig3/acc_all_gru.png
