BailabUNC/LaHMo/results/fig3/acc_all_lstm.png

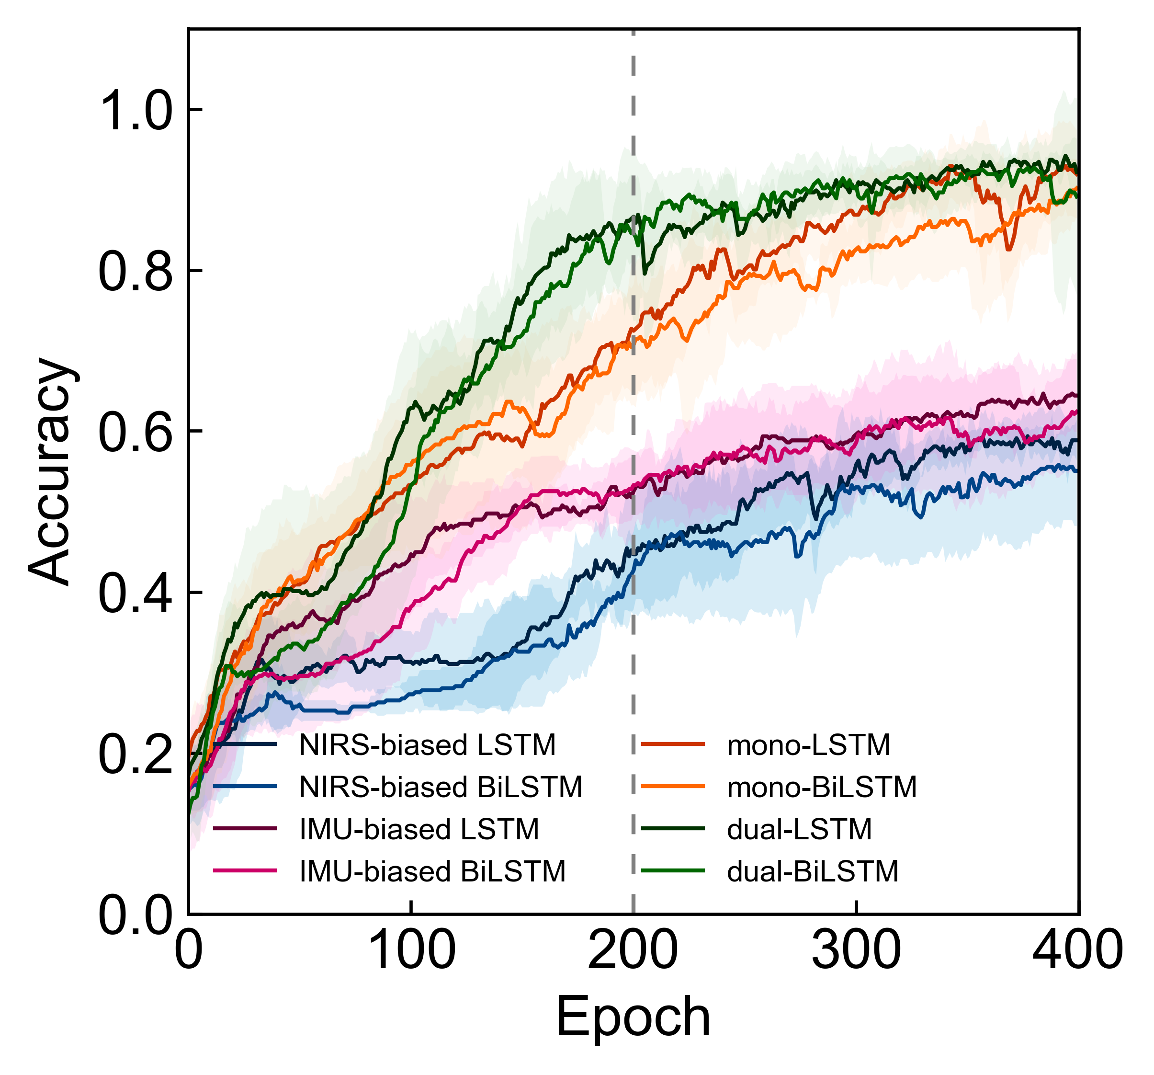
results/fig3/acc_all_lstm.png
