BailabUNC/LaHMo/results/fig3/accuracy.png

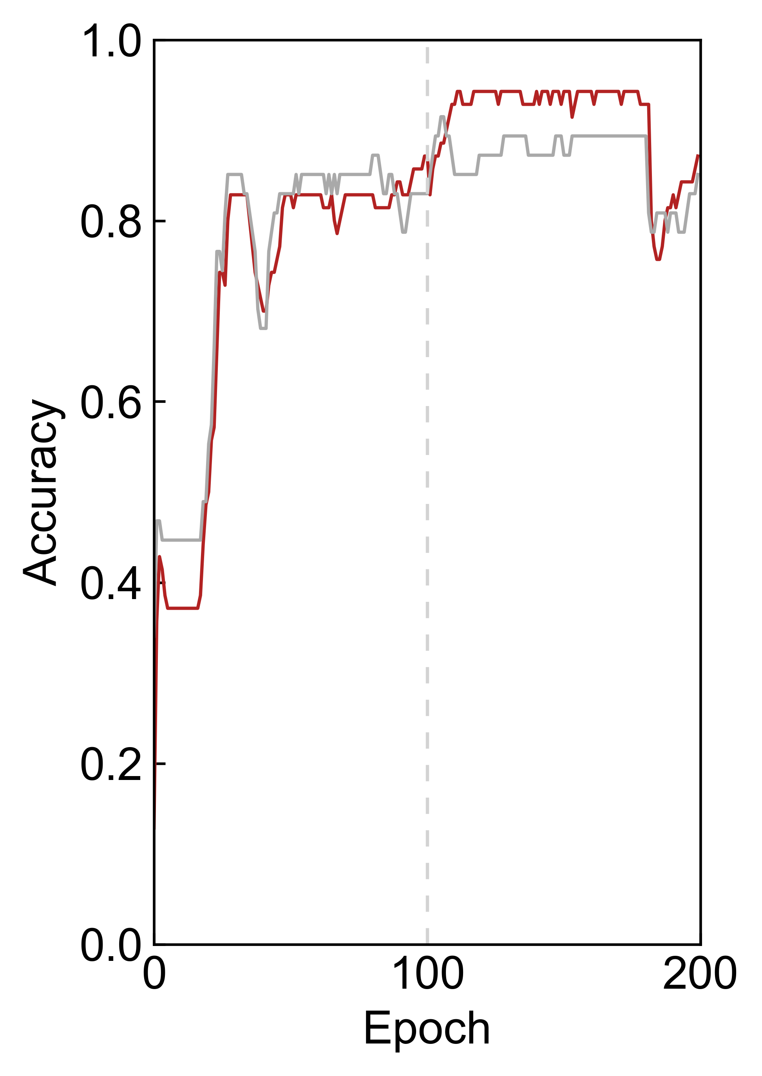
results/fig3/accuracy.png
