BailabUNC/LaHMo/results/fig3/accuracy_all.png

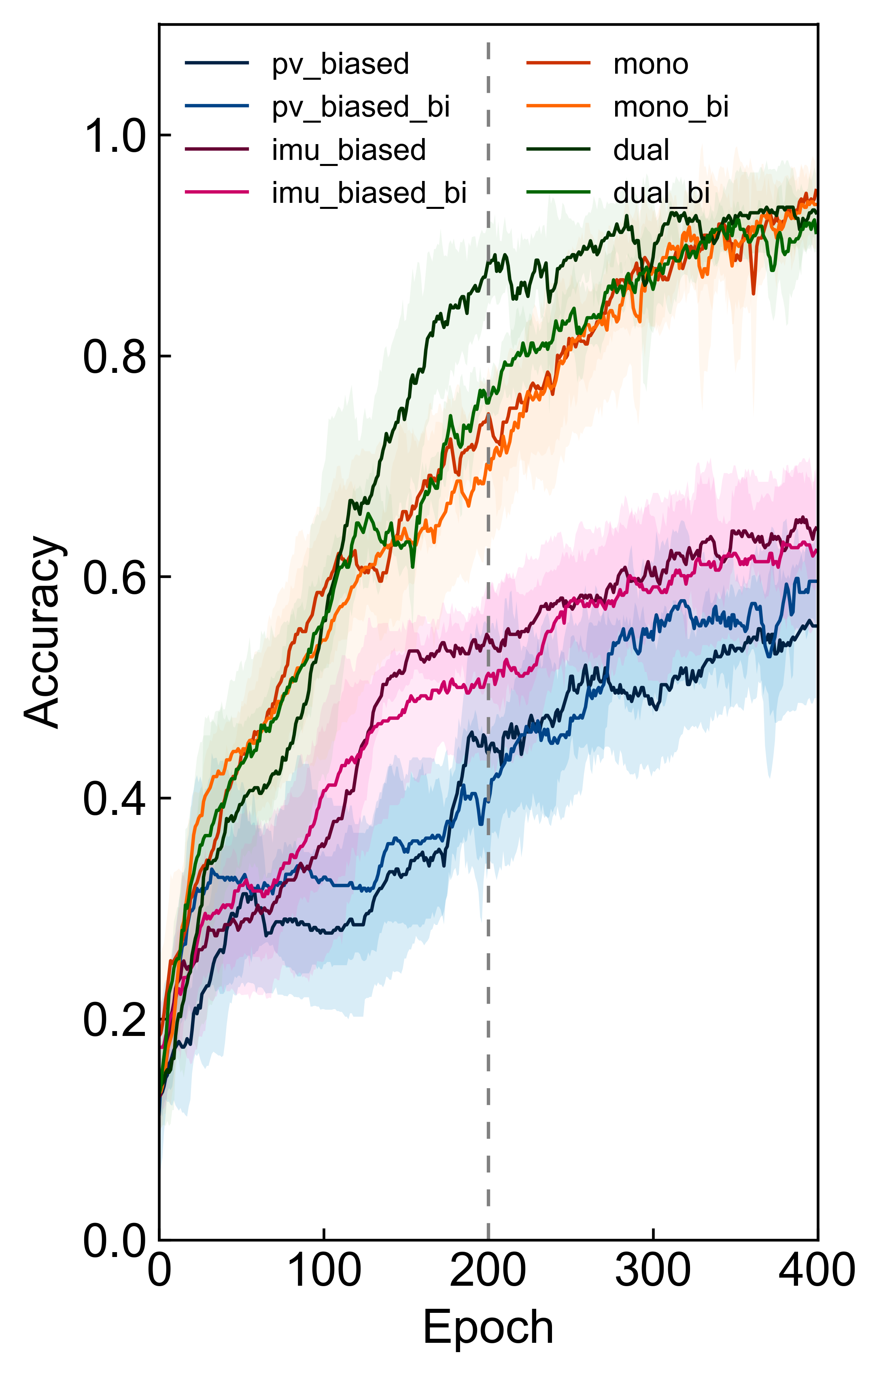
results/fig3/accuracy_all.png
