BailabUNC/LaHMo/results/fig3/accuracy_dual.png

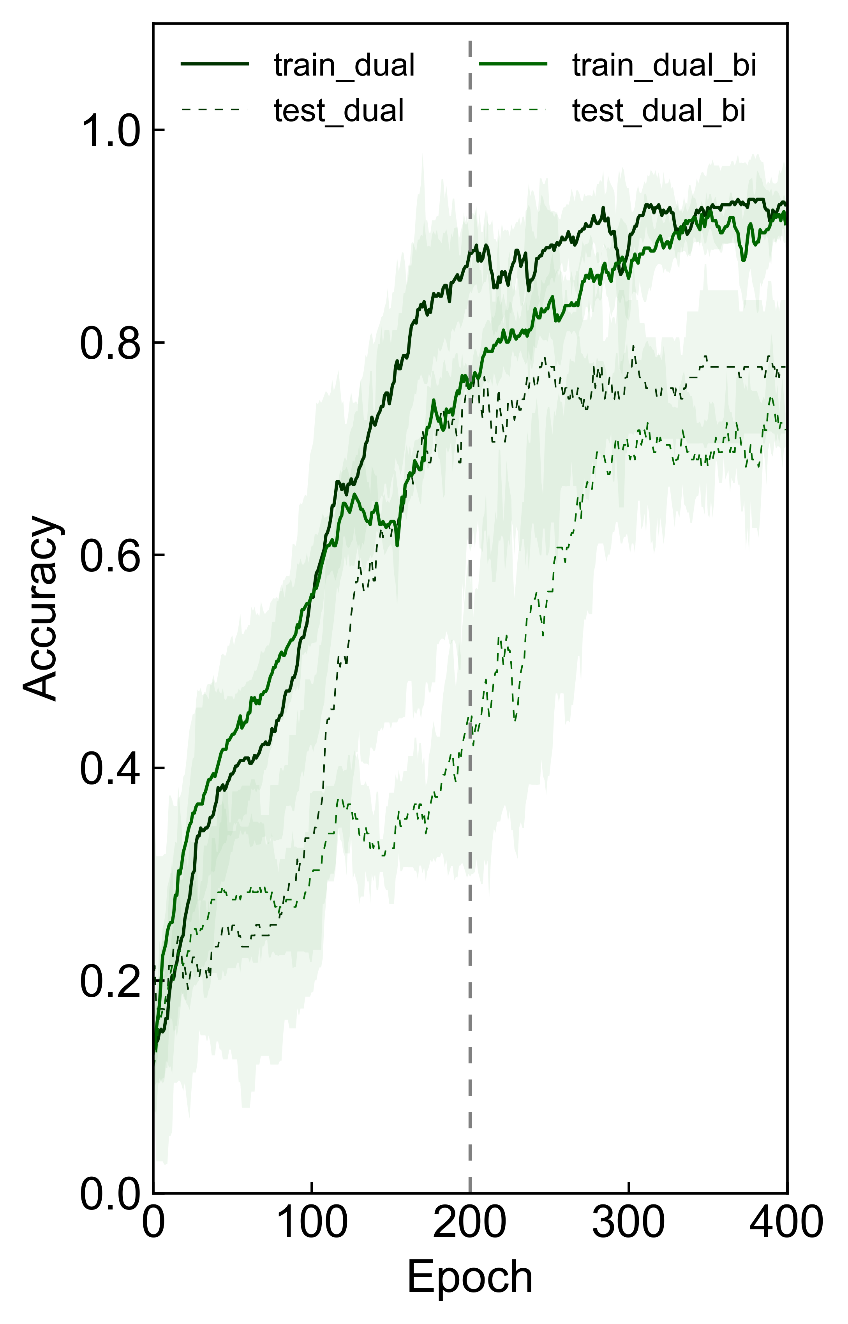
results/fig3/accuracy_dual.png
