BailabUNC/LaHMo/results/fig3/accuracy_dual_std_comparison.png

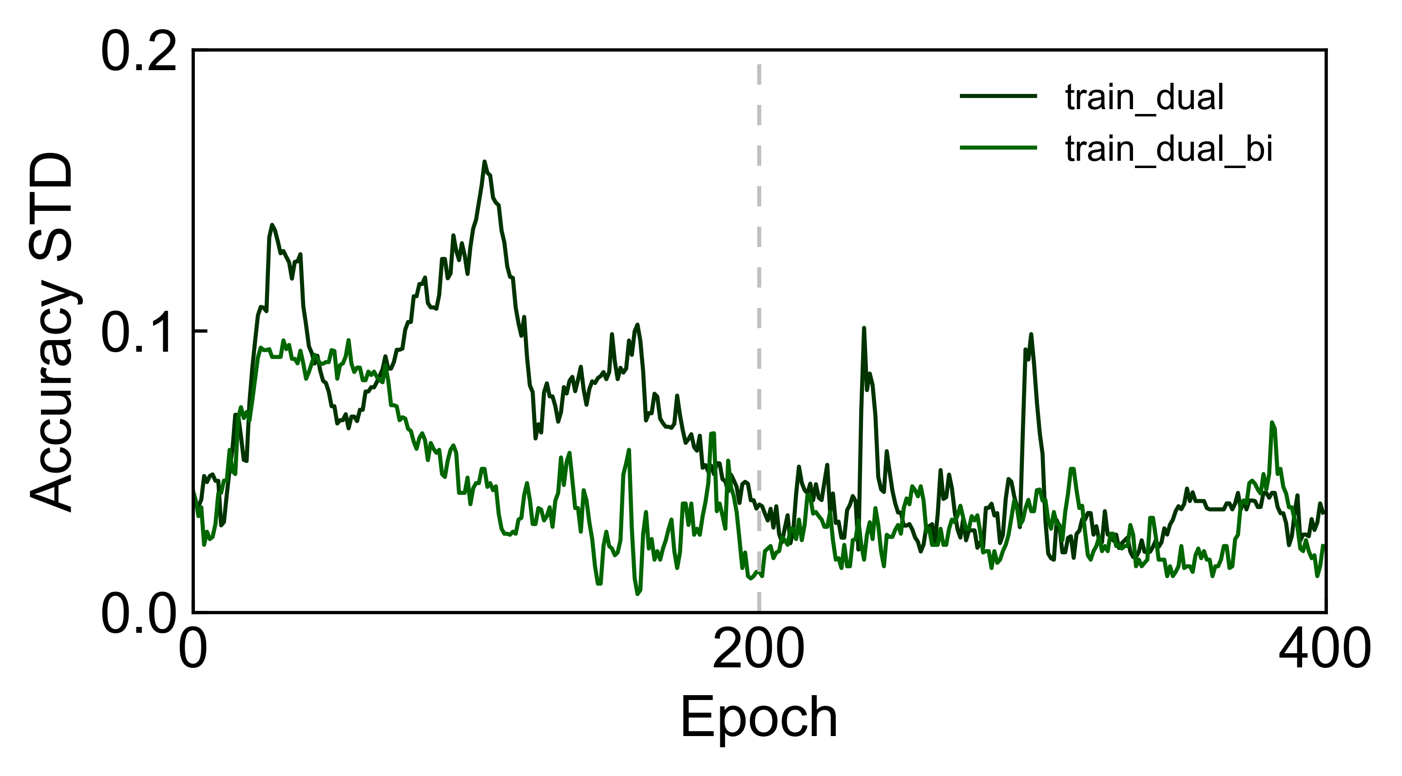
results/fig3/accuracy_dual_std_comparison.png
