BailabUNC/LaHMo/results/fig3/accuracy_dual_ttest.png

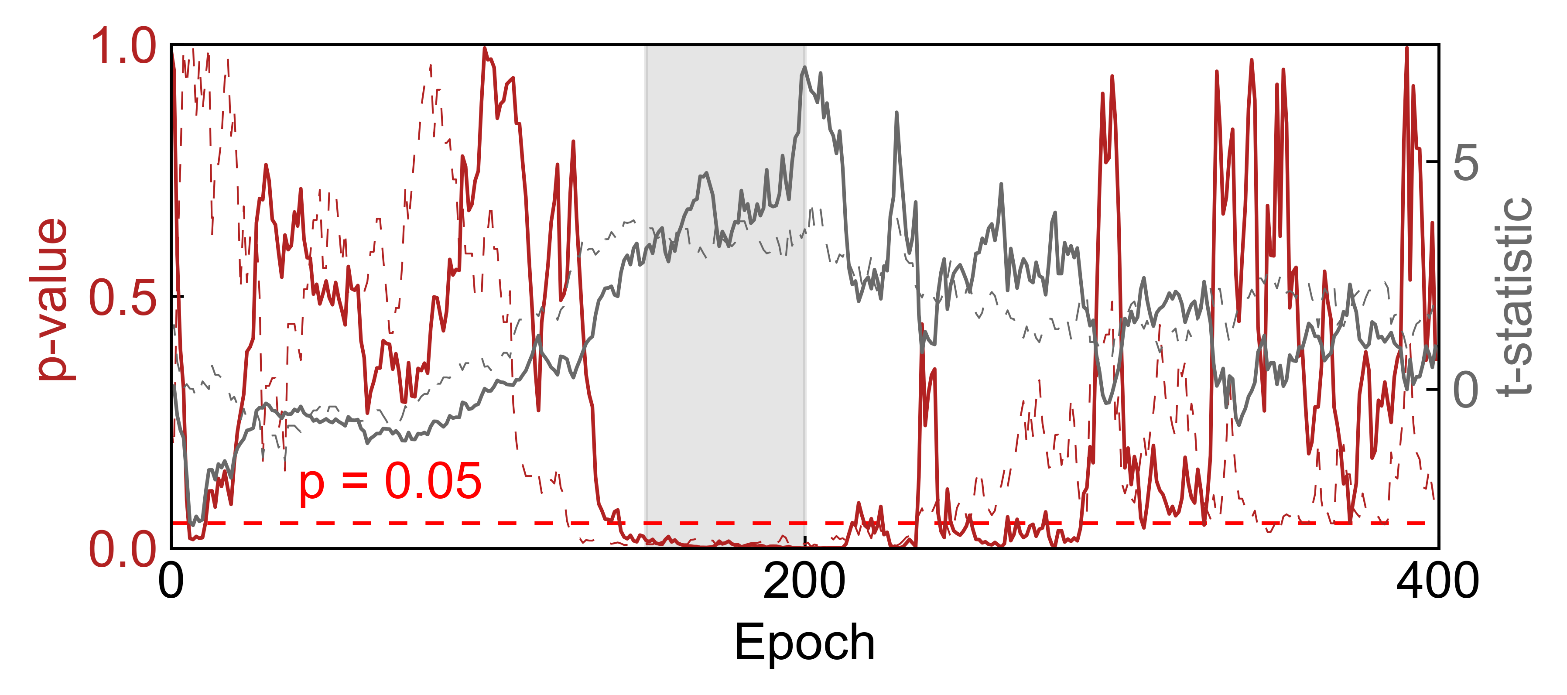
results/fig3/accuracy_dual_ttest.png
