BailabUNC/LaHMo/results/fig3/confusion_matrix.png

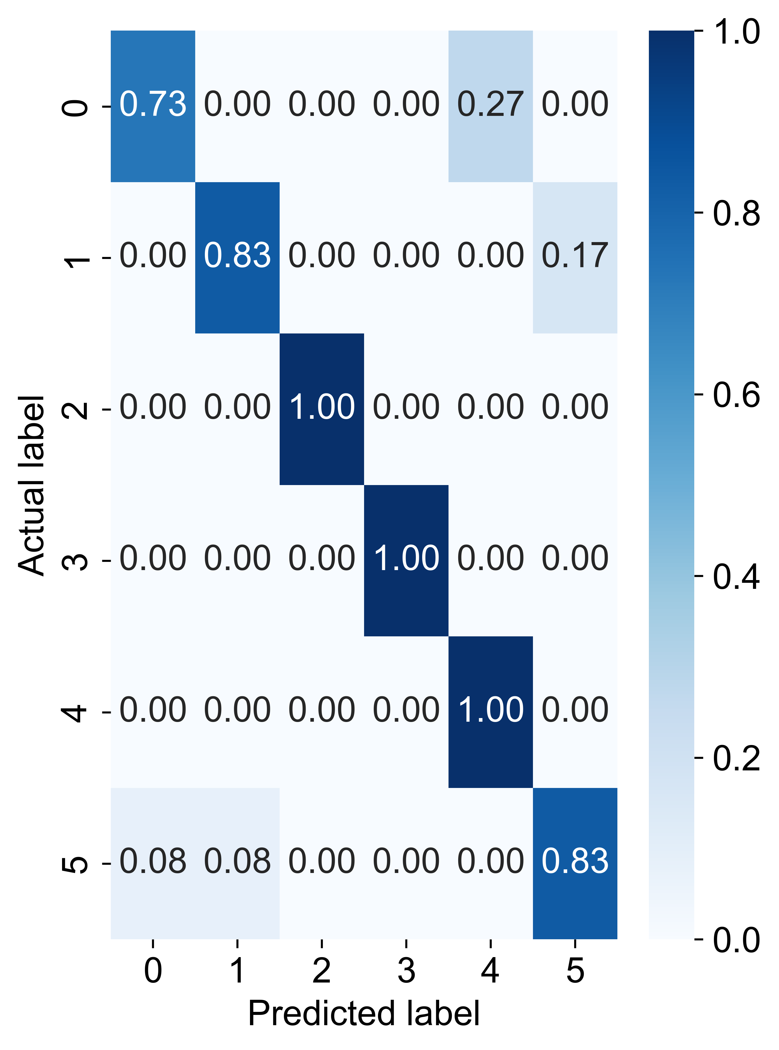
results/fig3/confusion_matrix.png
