BailabUNC/LaHMo/results/fig3/confusion_matrix_gru_all.png

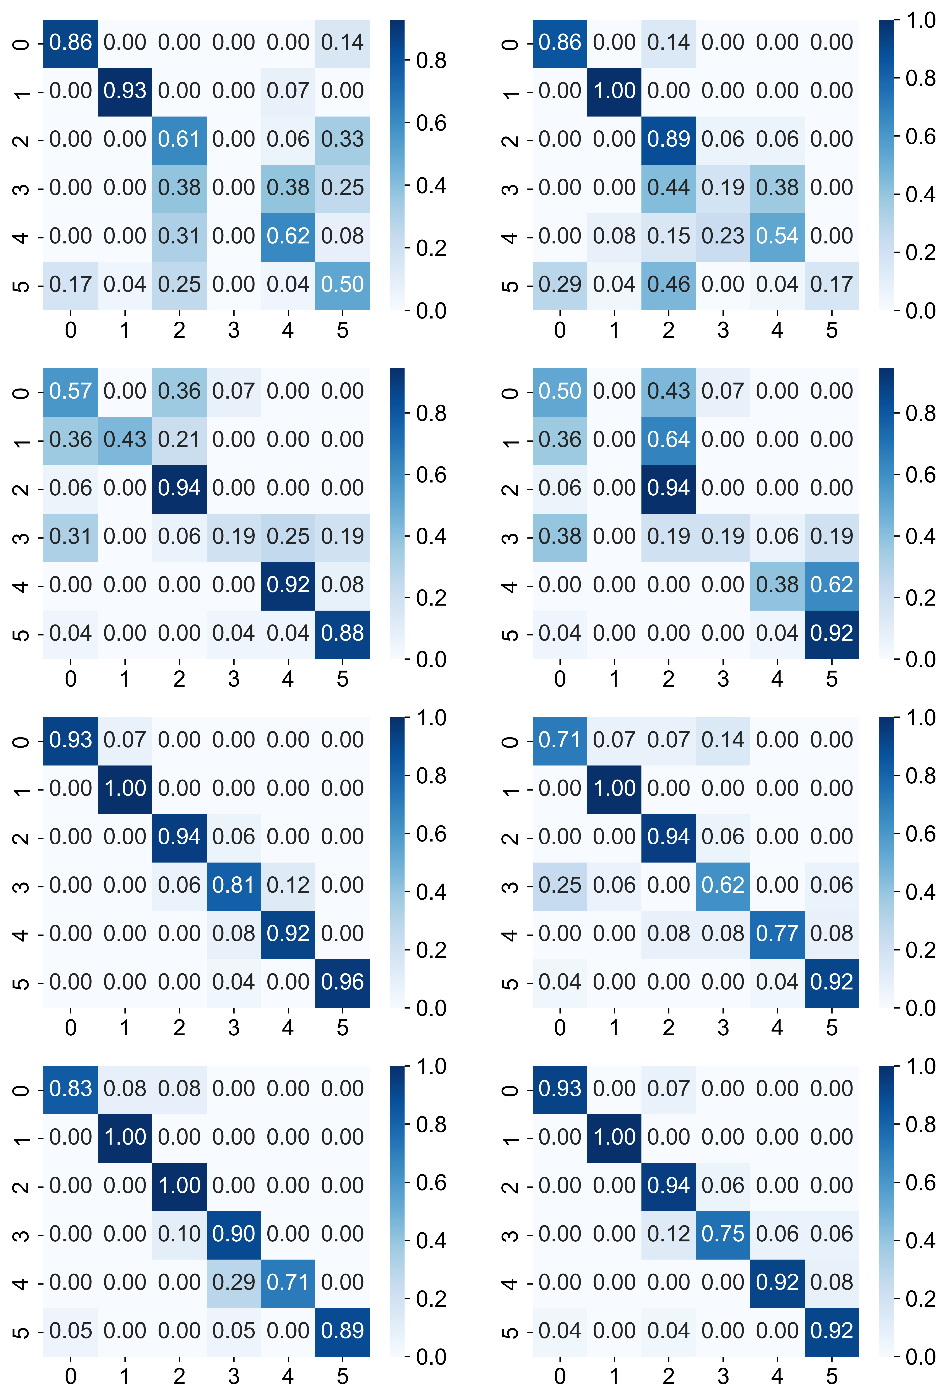
results/fig3/confusion_matrix_gru_all.png
