BailabUNC/LaHMo/results/fig3/confusion_matrix_imu_biased.png

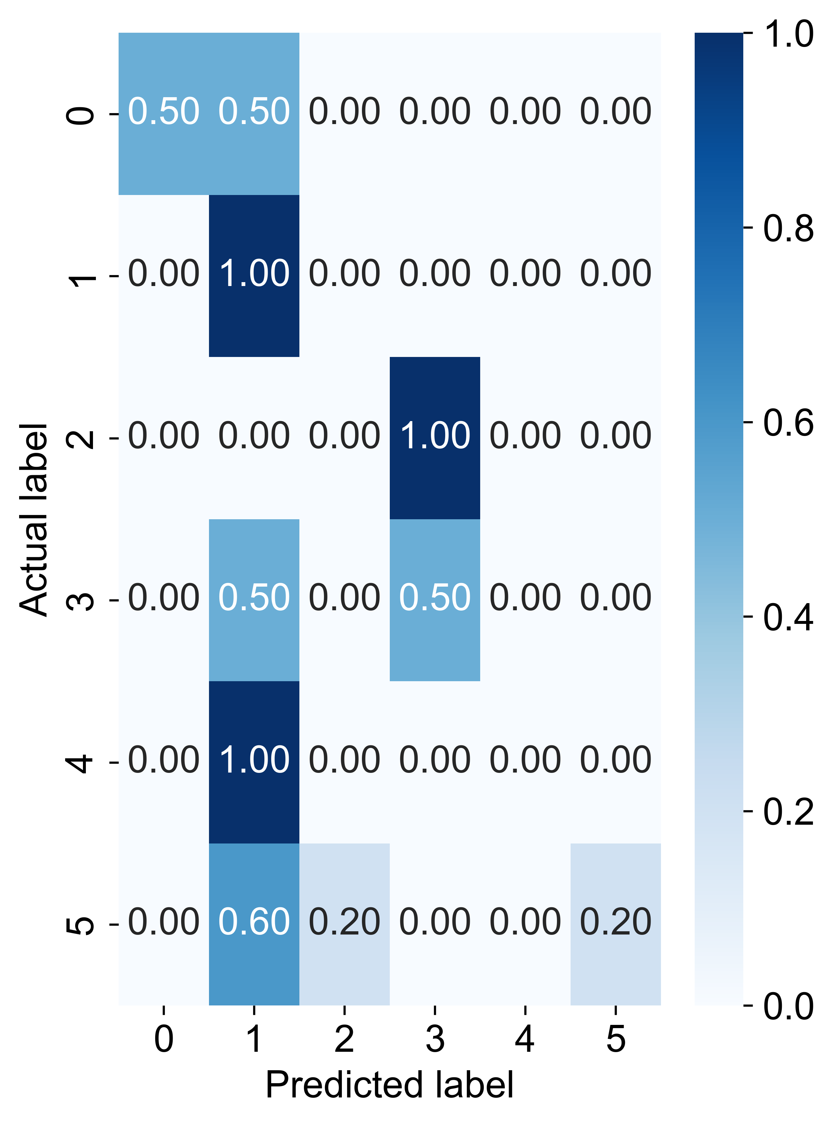
results/fig3/confusion_matrix_imu_biased.png
