BailabUNC/LaHMo/results/fig3/confusion_matrix_mono.png

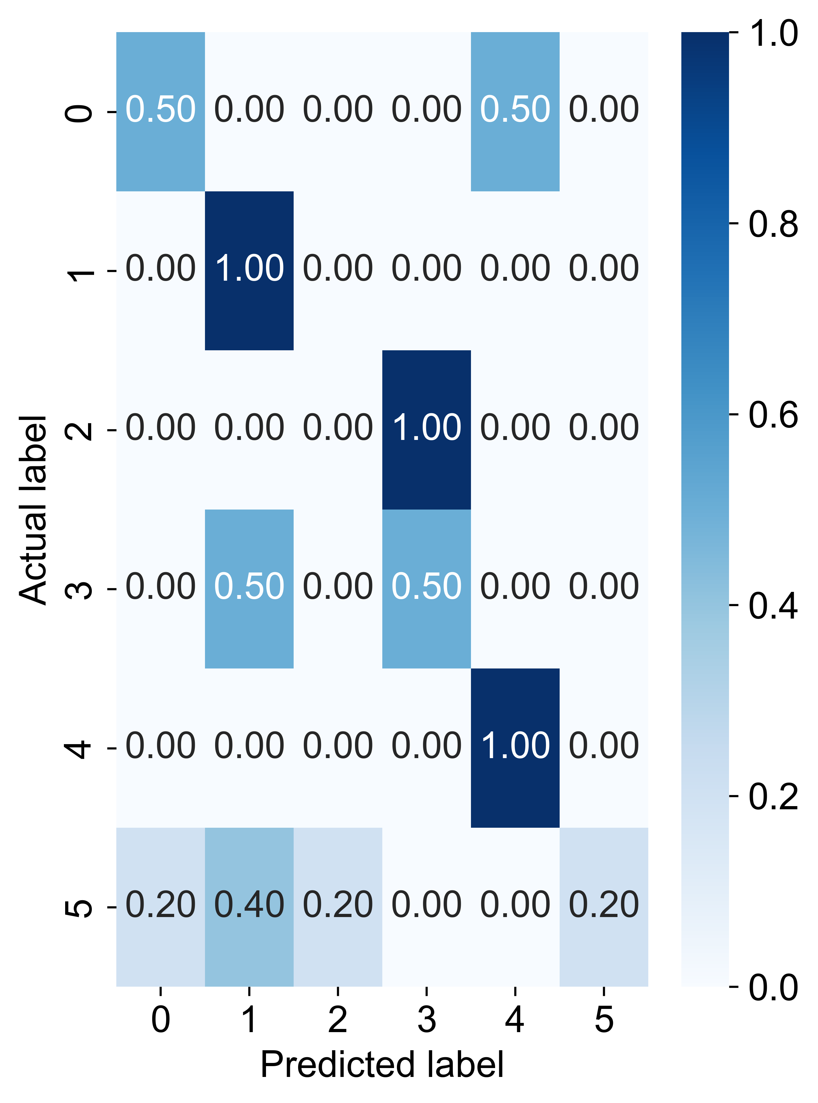
results/fig3/confusion_matrix_mono.png
