BailabUNC/LaHMo/results/fig3/confusion_matrix_mono_bi.png

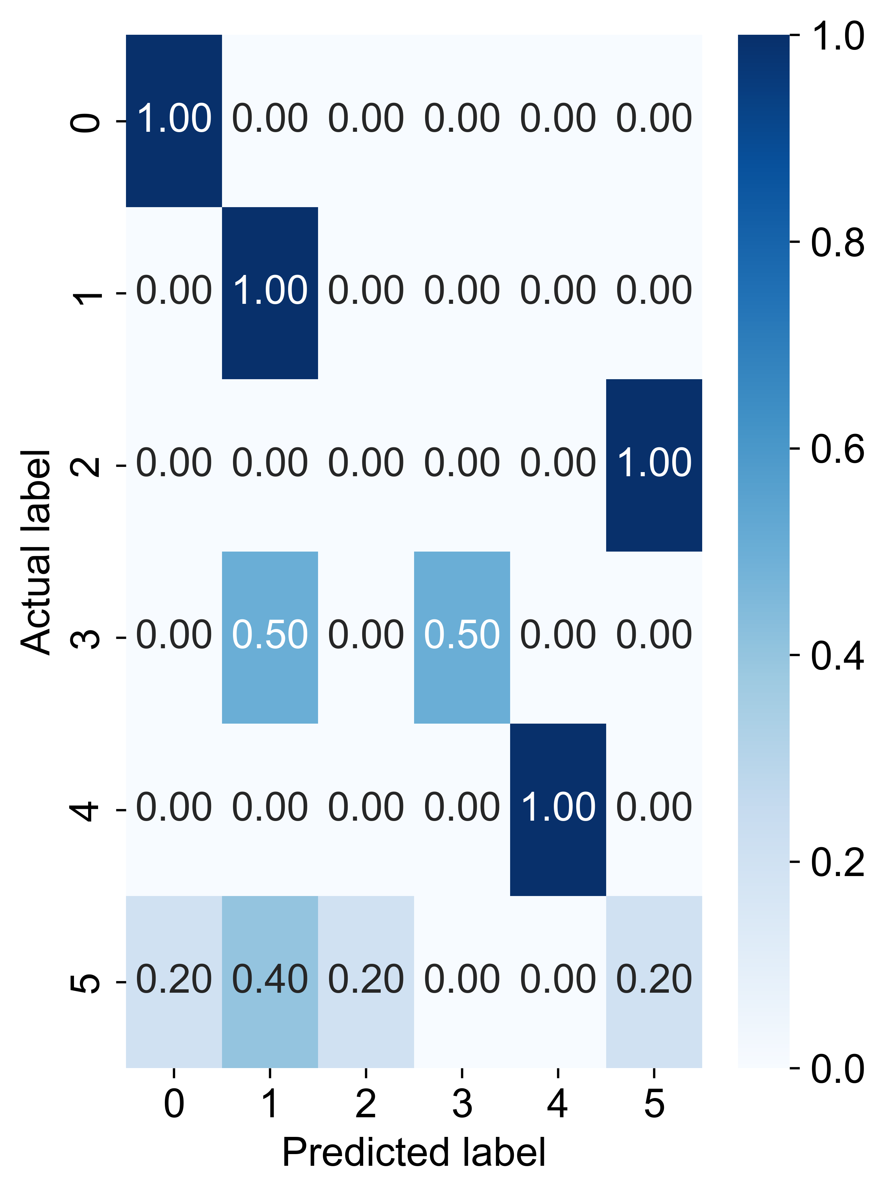
results/fig3/confusion_matrix_mono_bi.png
