BailabUNC/LaHMo/results/fig3/confusion_matrix_pv.png

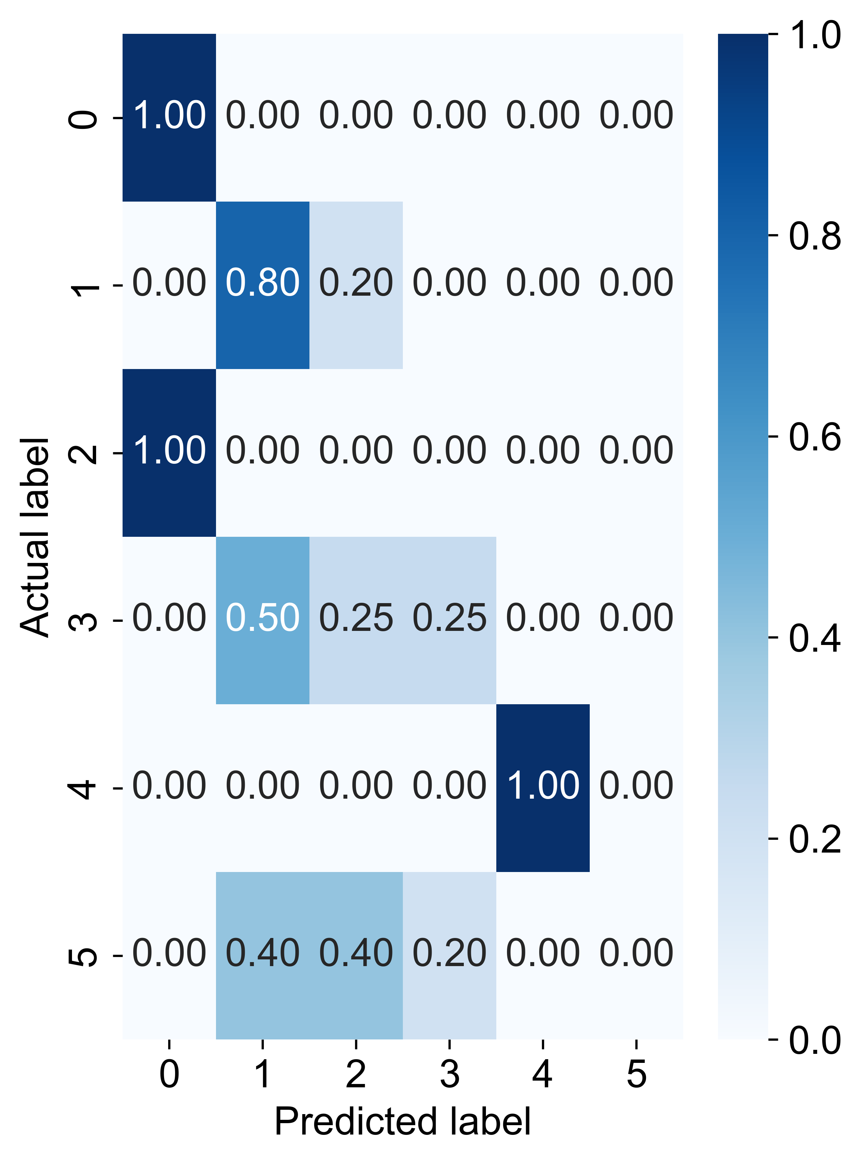
results/fig3/confusion_matrix_pv.png
