BailabUNC/LaHMo/results/fig3/confusion_matrix_pv_biased_bi.png

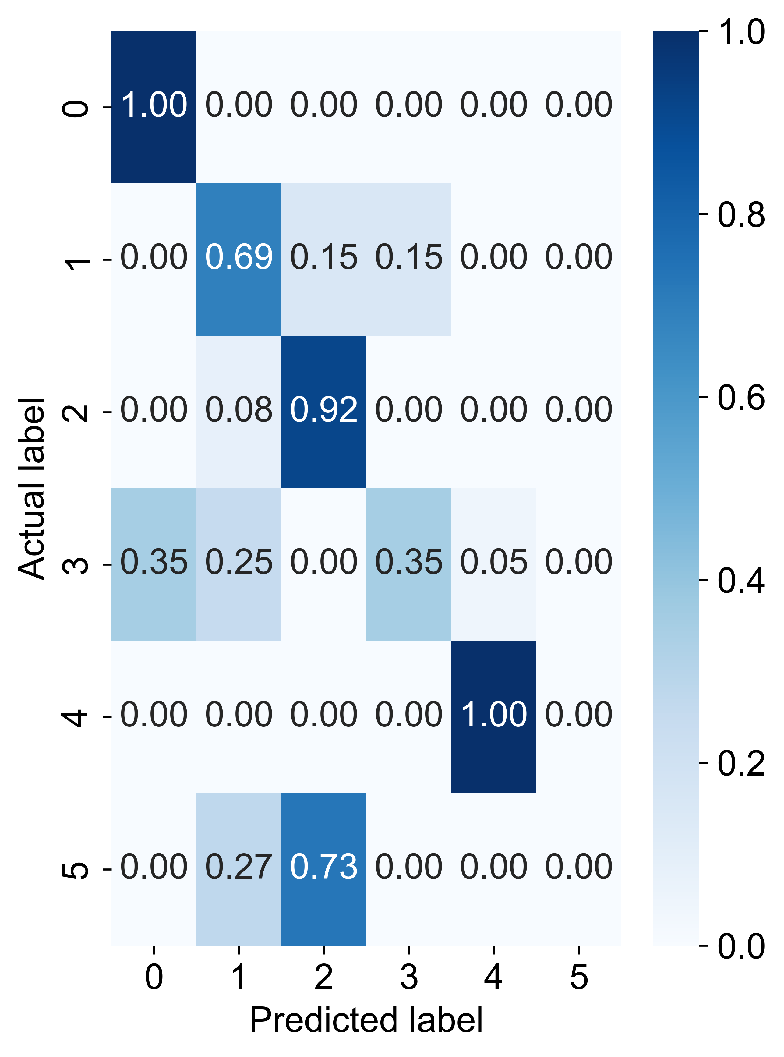
results/fig3/confusion_matrix_pv_biased_bi.png
