BailabUNC/LaHMo/results/fig3/confusion_matrix_rnn_all.png

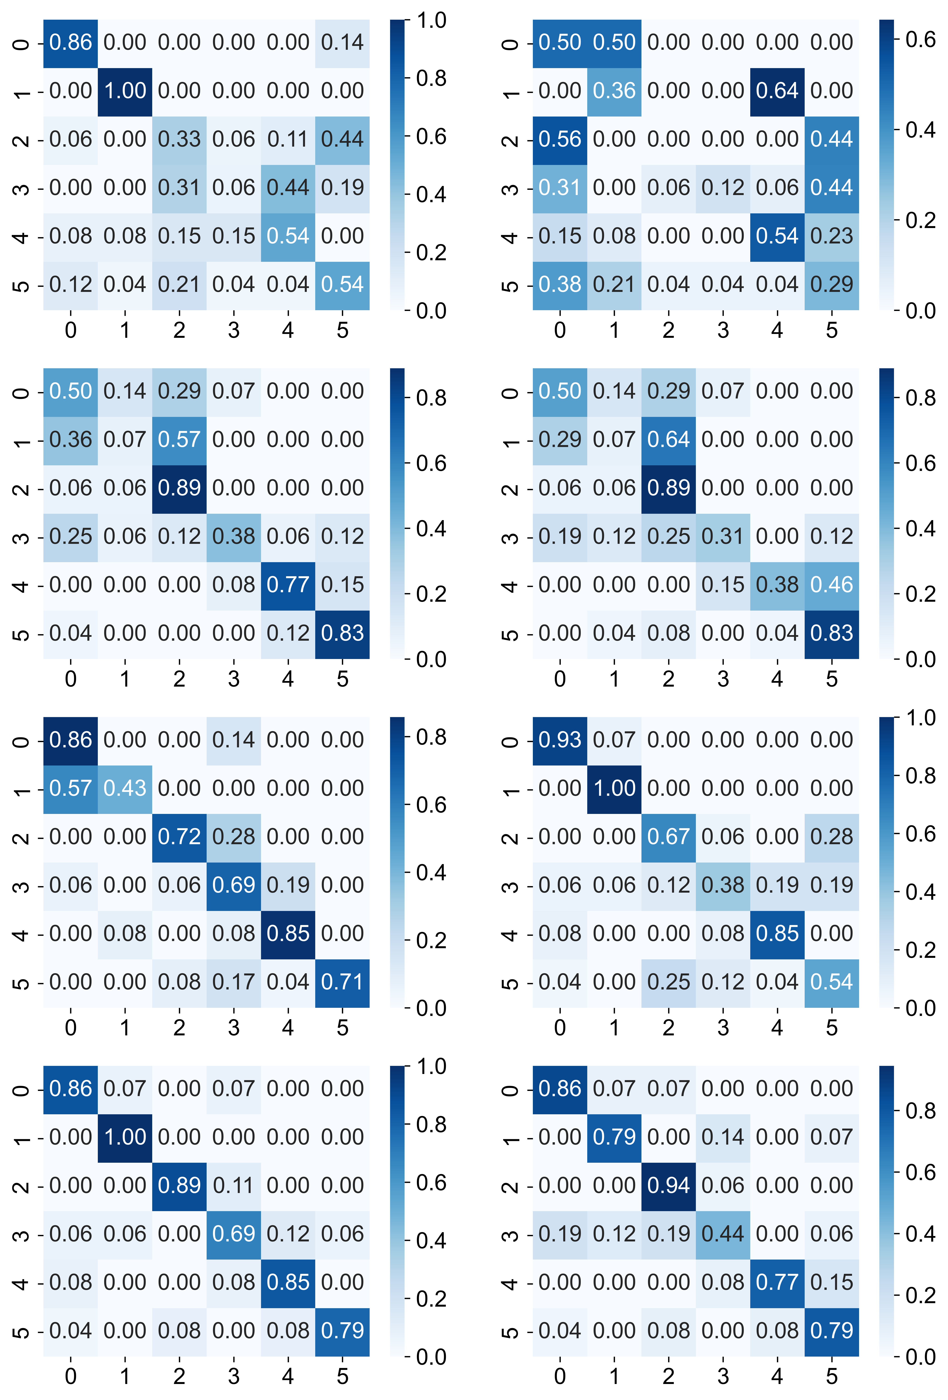
results/fig3/confusion_matrix_rnn_all.png
