BailabUNC/LaHMo/results/fig3/label_example/dry_cough.png

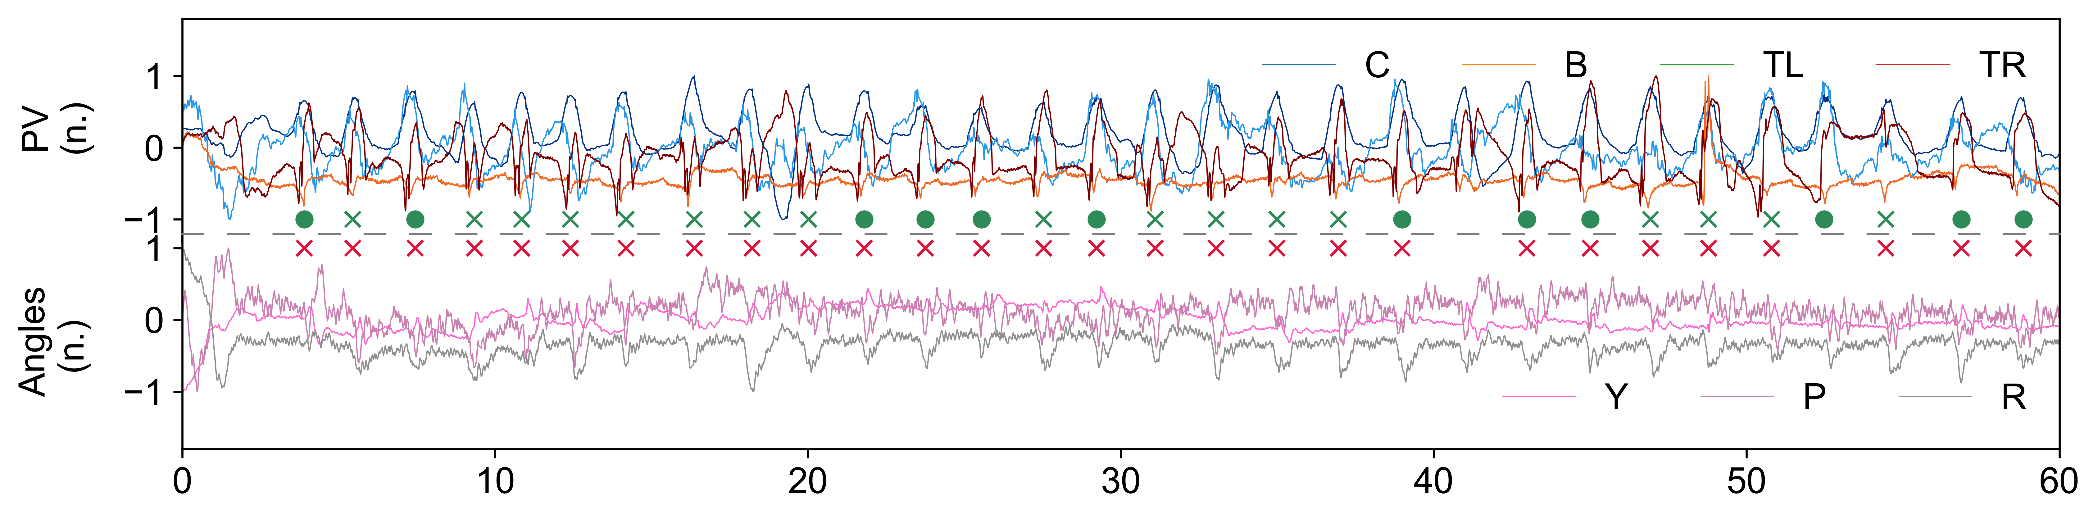
results/fig3/label_example/dry_cough.png
