BailabUNC/LaHMo/results/fig3/label_example/swallow.png

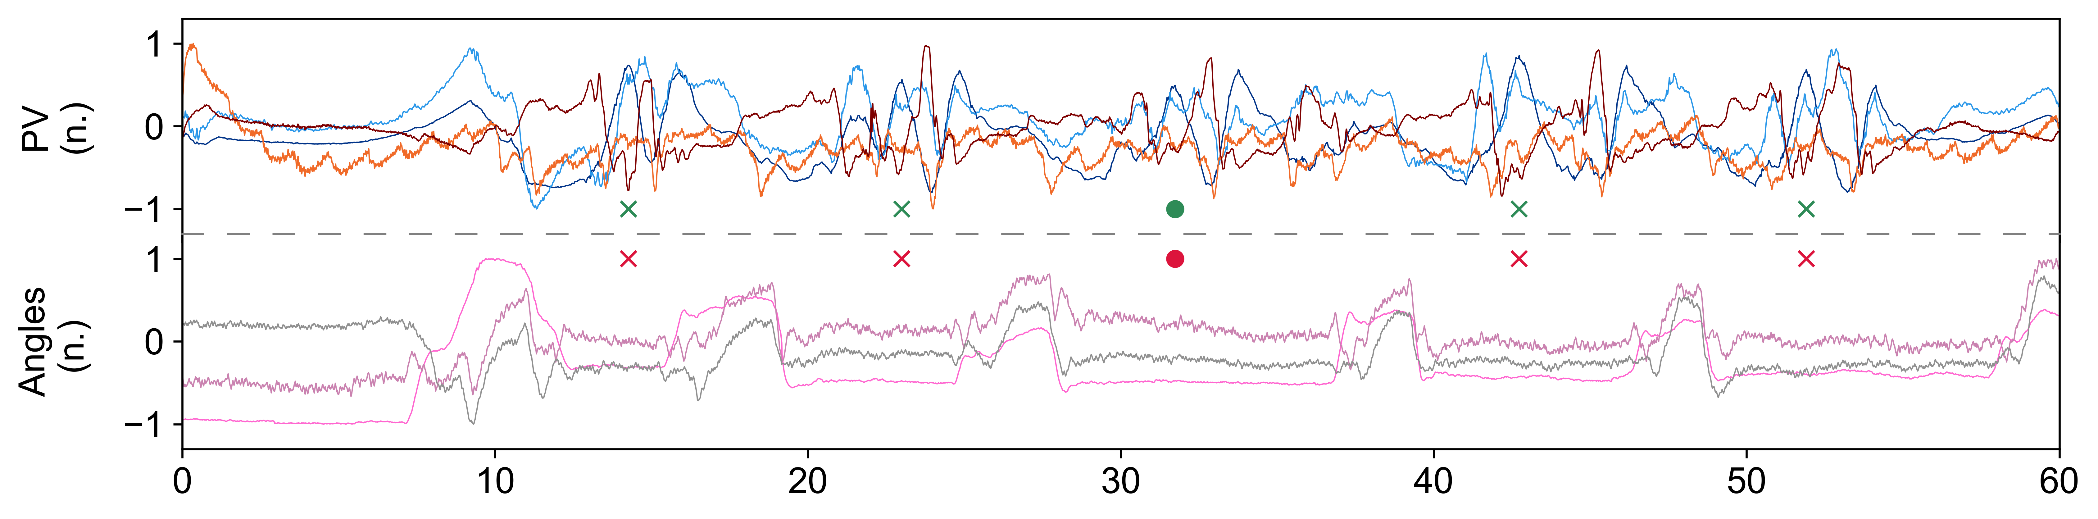
results/fig3/label_example/swallow.png
