BailabUNC/LaHMo/results/fig3/label_example/throat_clearing.png

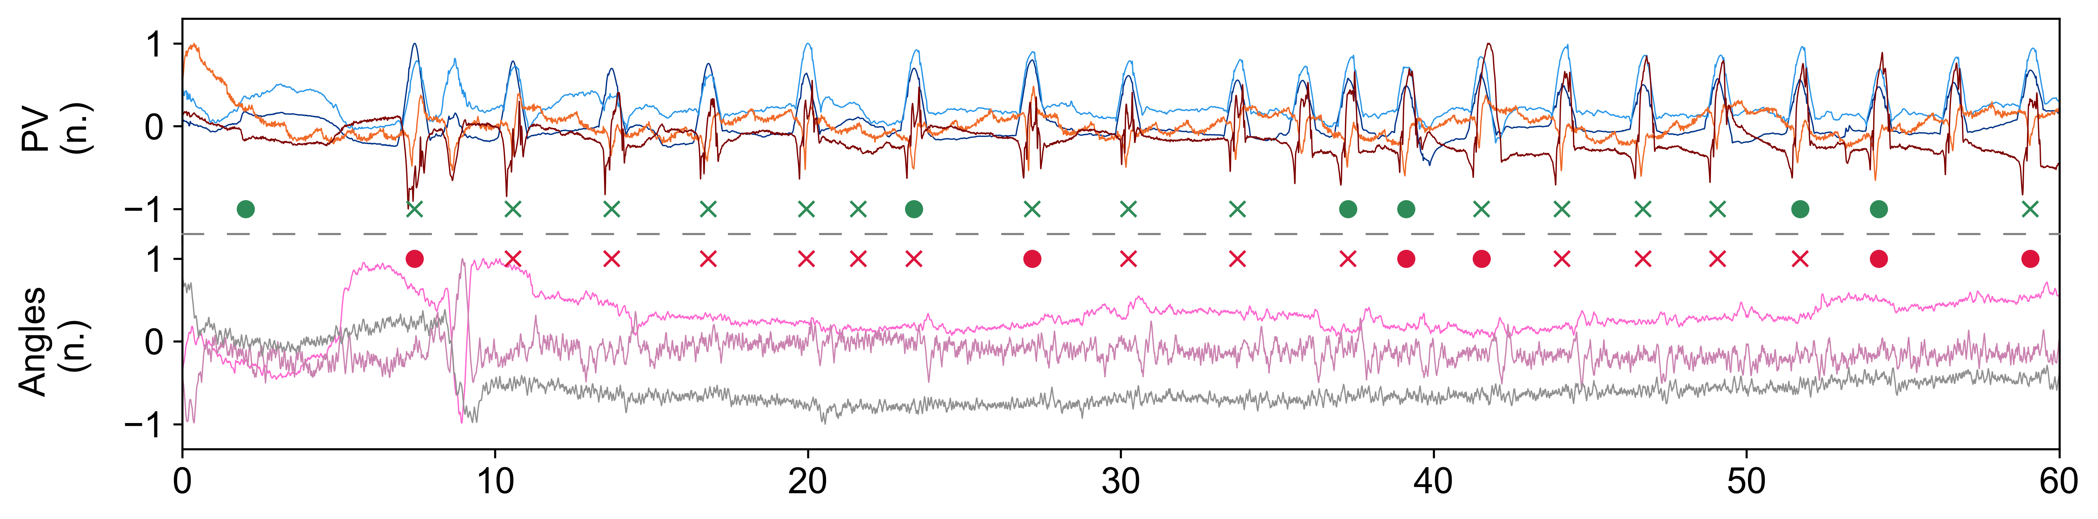
results/fig3/label_example/throat_clearing.png
