BailabUNC/LaHMo/results/fig3/label_example/walking.png

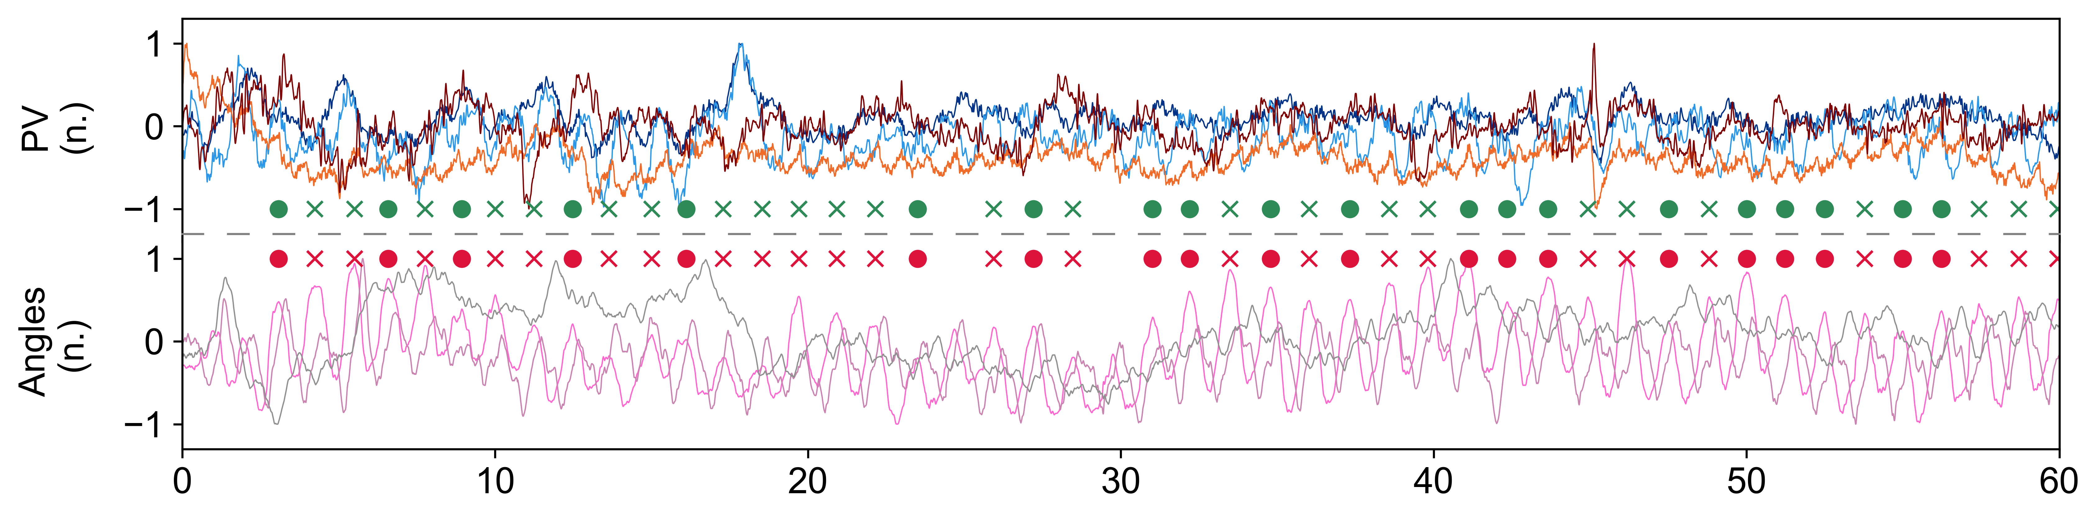
results/fig3/label_example/walking.png
