BailabUNC/LaHMo/results/fig3/loss.png

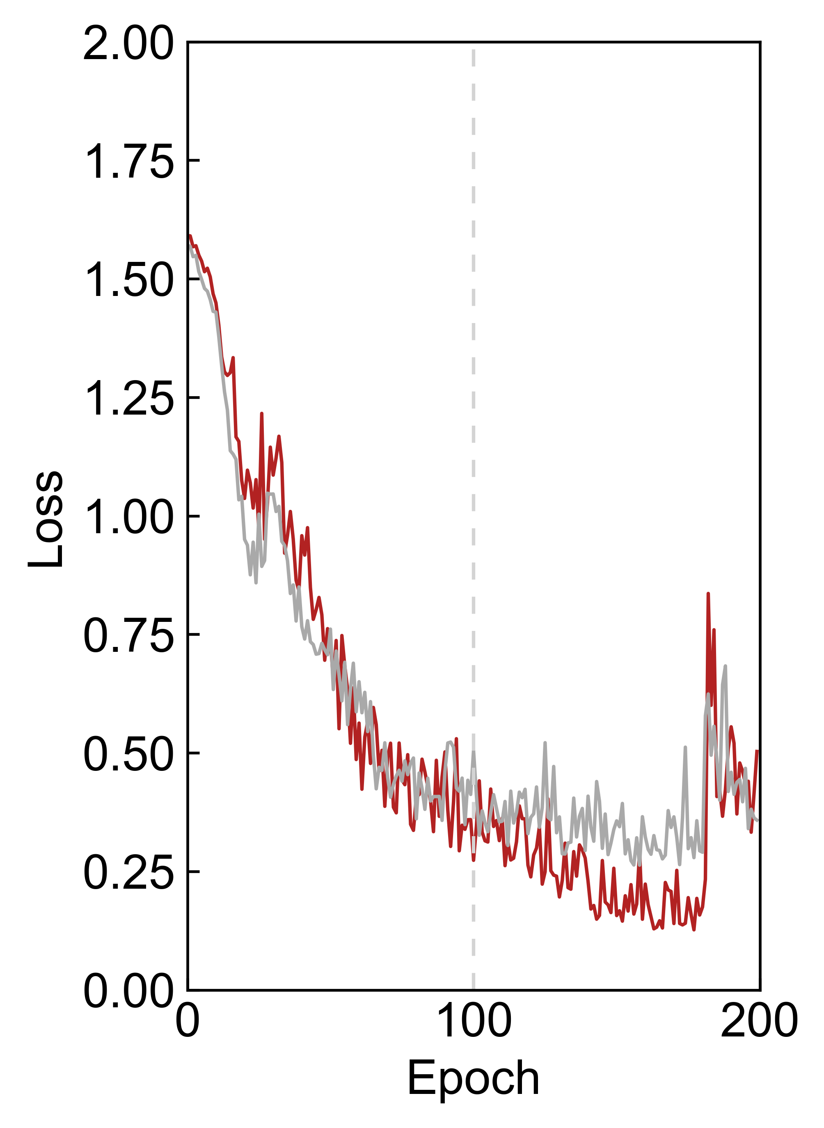
results/fig3/loss.png
