BailabUNC/LaHMo/results/fig3/loss_all.png

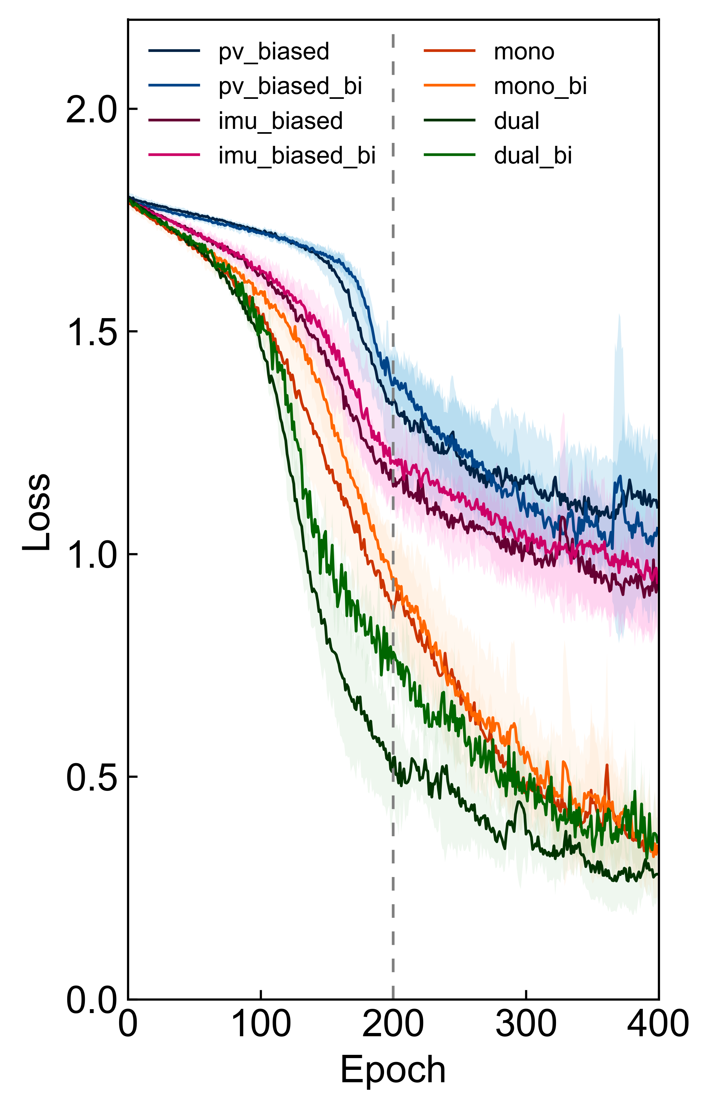
results/fig3/loss_all.png
