BailabUNC/LaHMo/results/fig3/loss_all_frnn.png

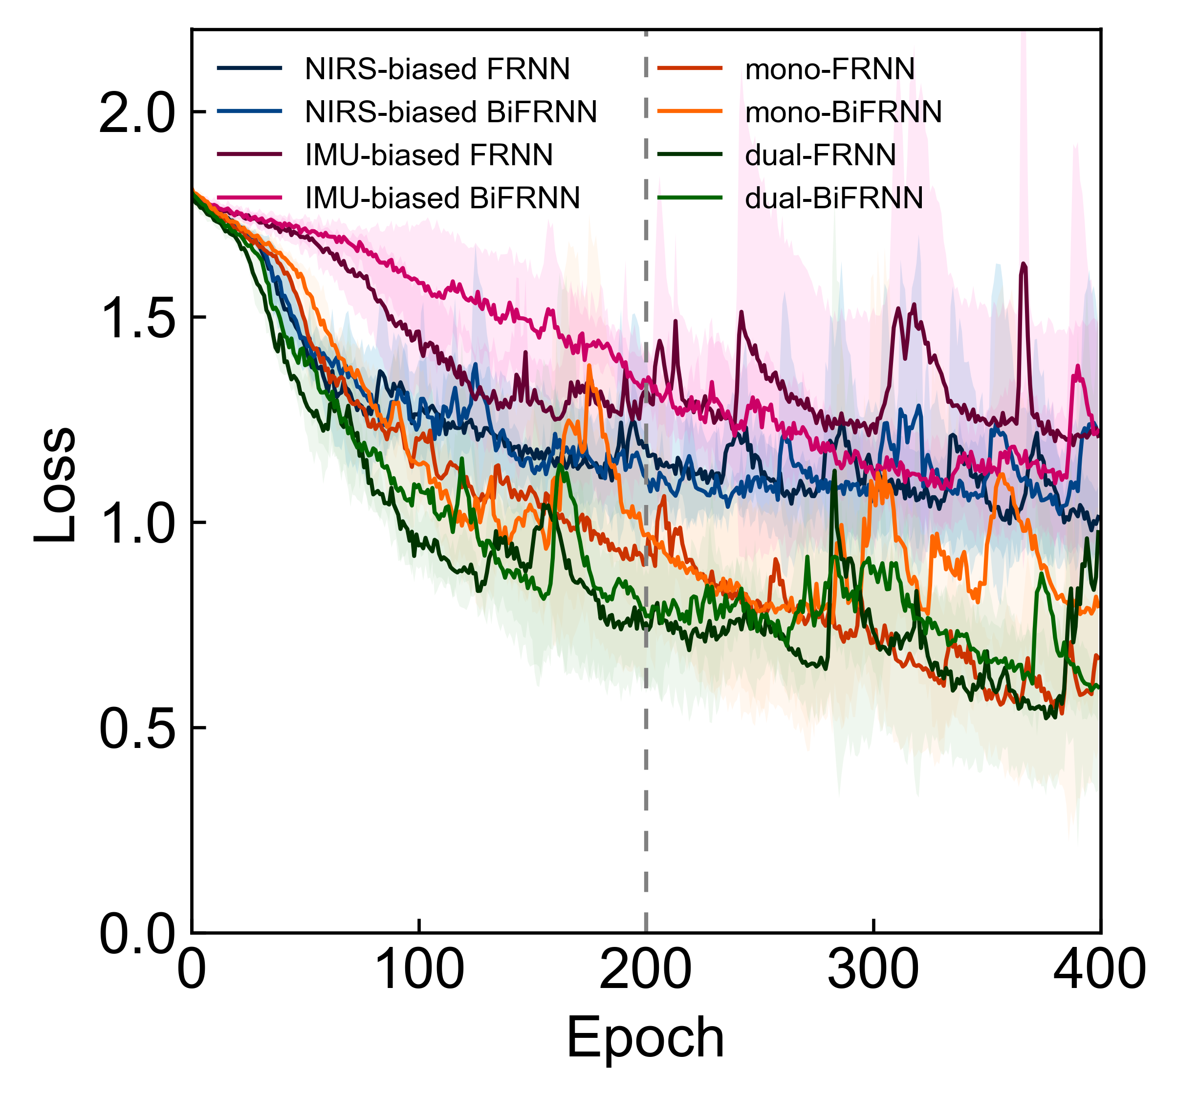
results/fig3/loss_all_frnn.png
