BailabUNC/LaHMo/results/fig3/loss_all_gru.png

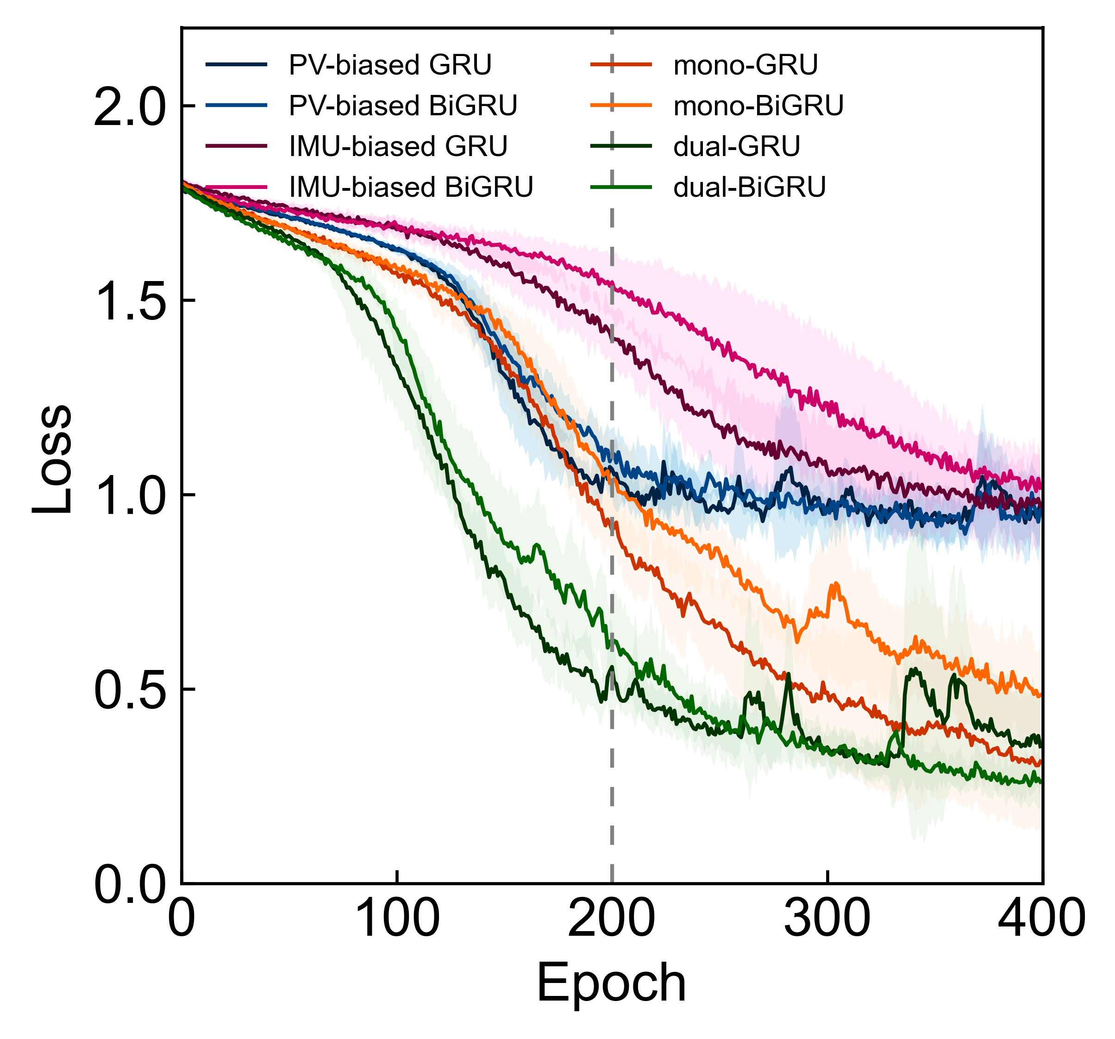
results/fig3/loss_all_gru.png
