BailabUNC/LaHMo/results/fig3/loss_all_gru_full.png

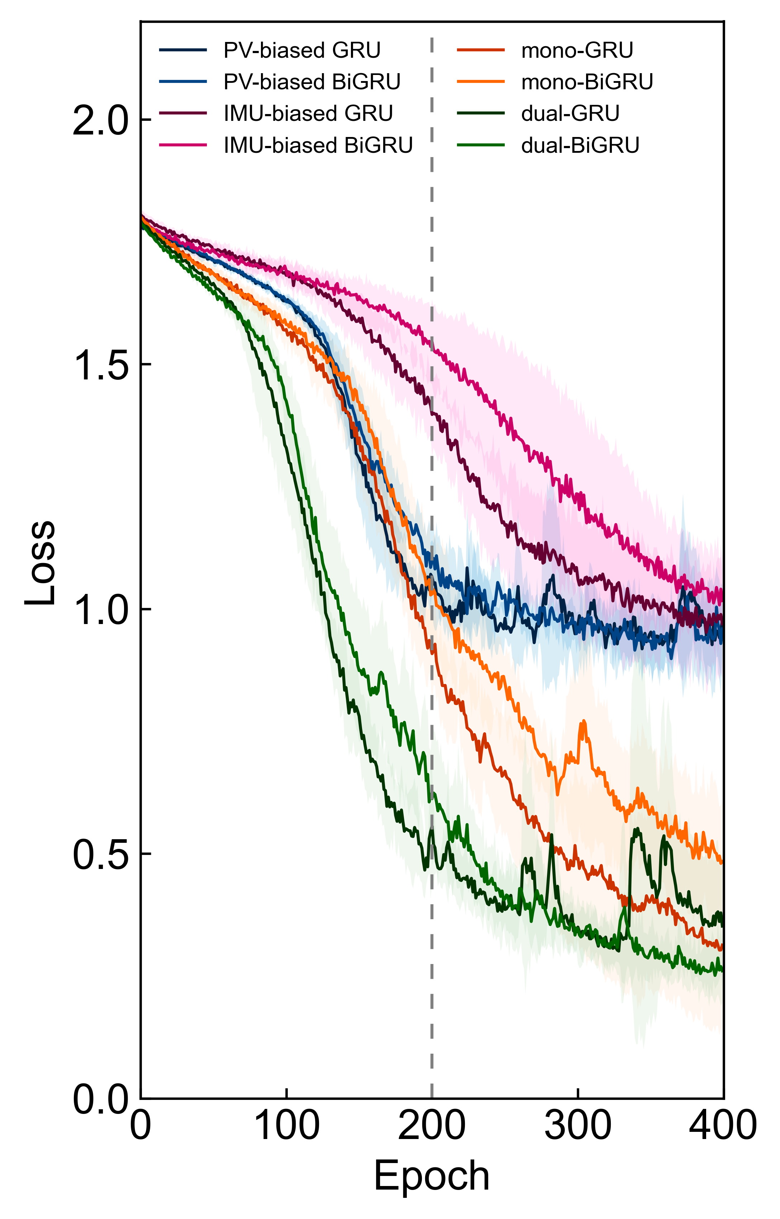
results/fig3/loss_all_gru_full.png
