BailabUNC/LaHMo/results/fig3/loss_all_lstm.png

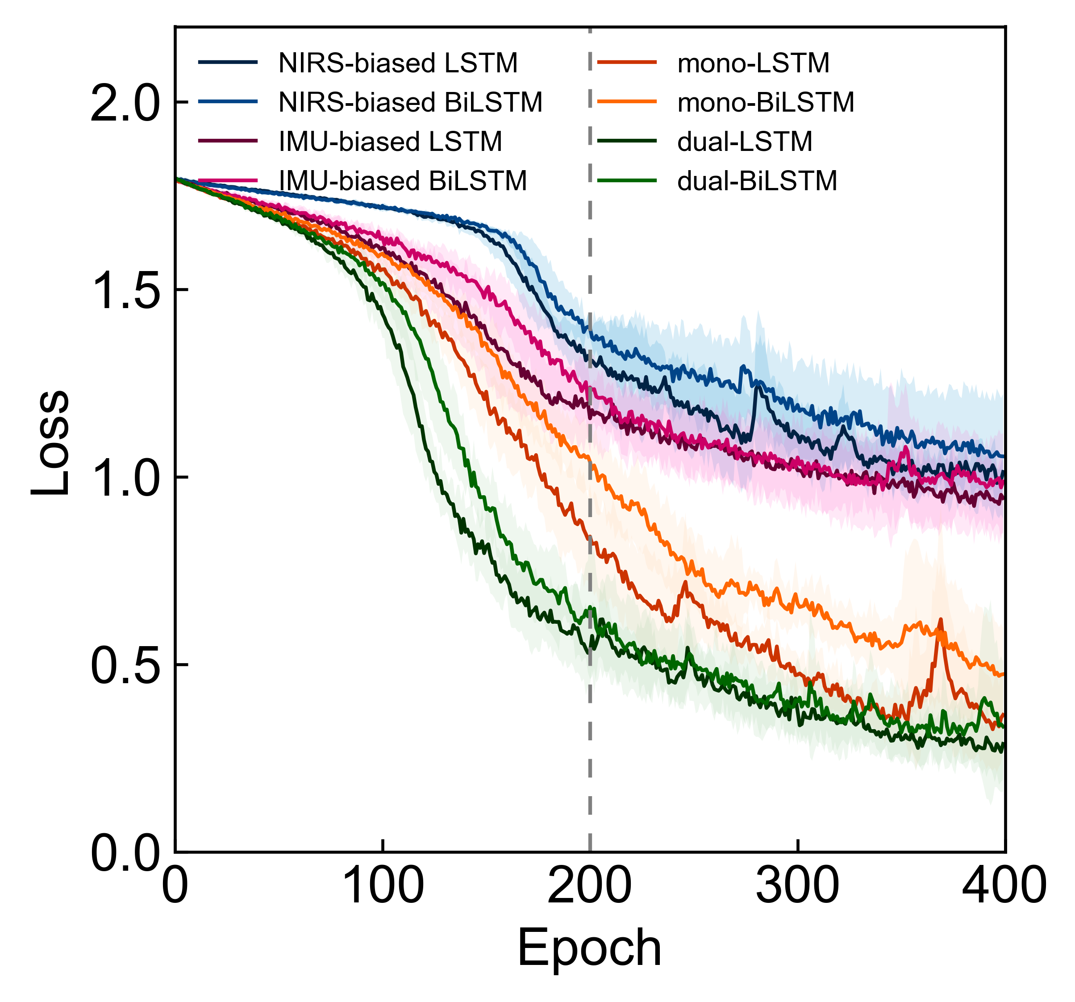
results/fig3/loss_all_lstm.png
