BailabUNC/LaHMo/results/fig3/std_frnn.png

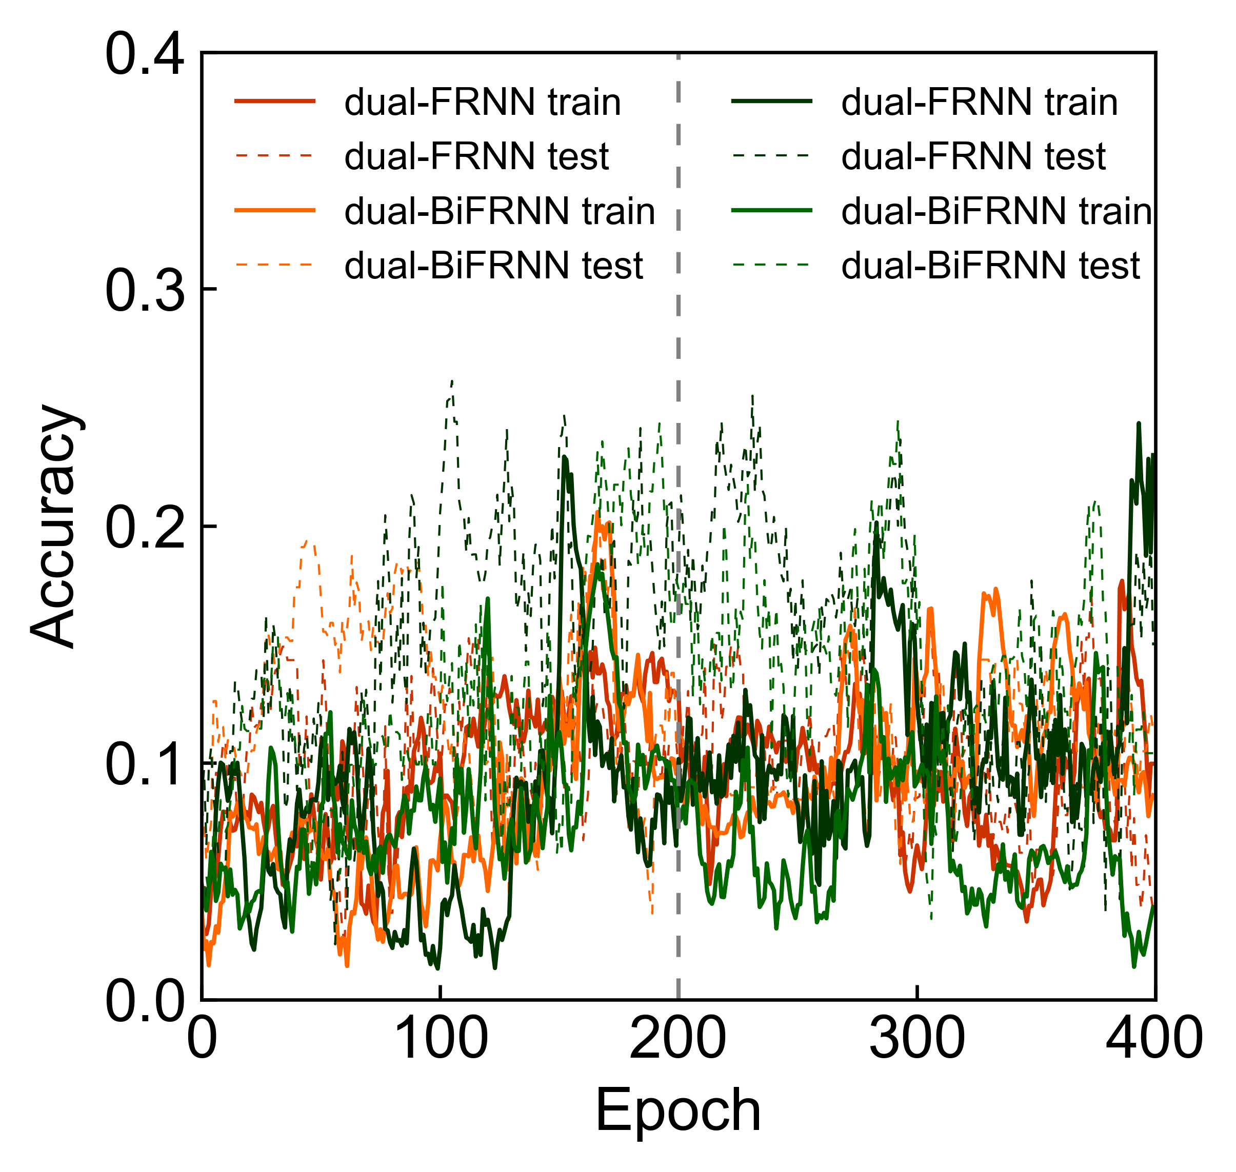
results/fig3/std_frnn.png
