BailabUNC/LaHMo/results/fig3/std_gru.png

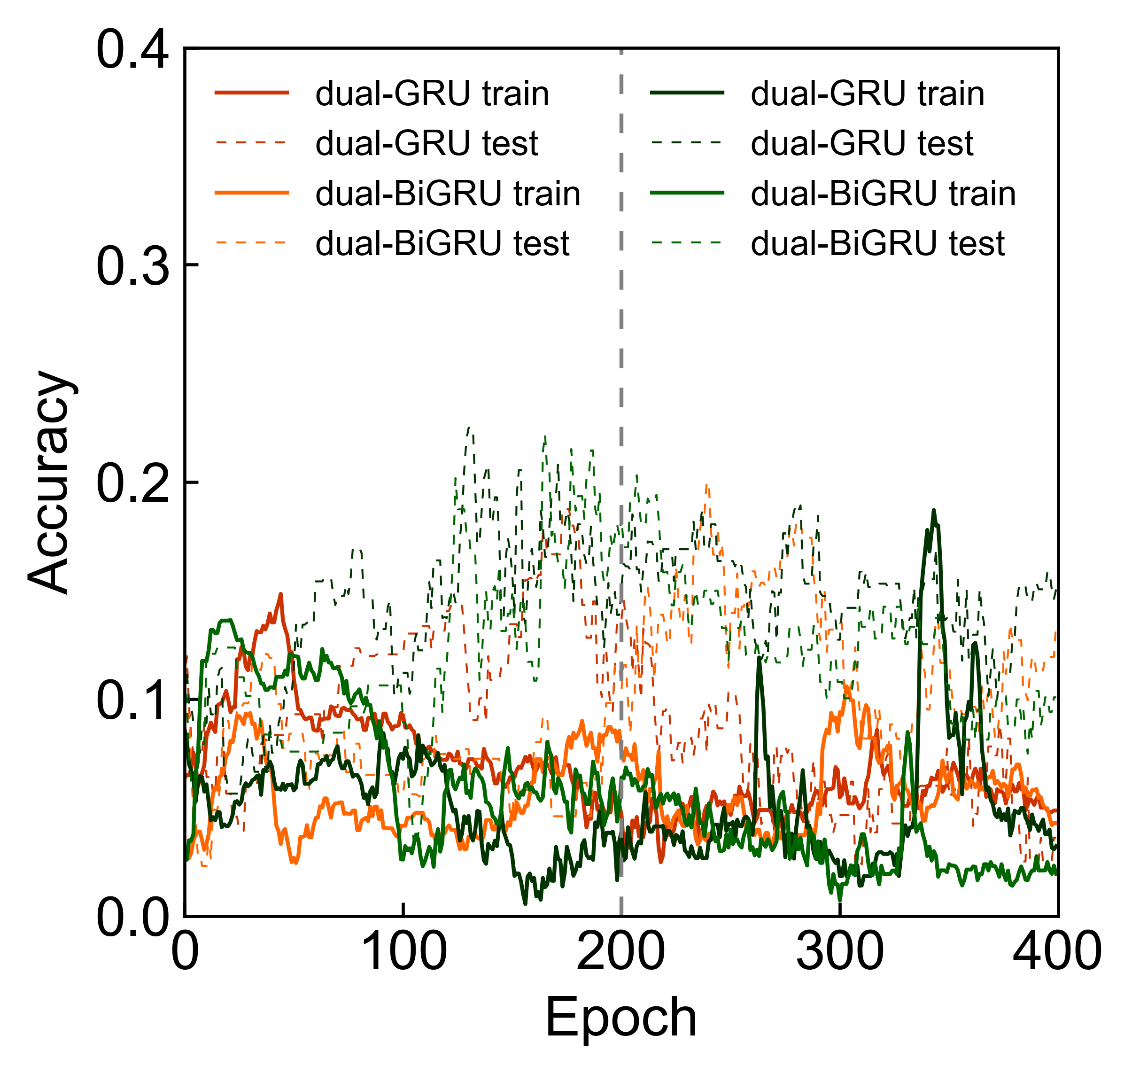
results/fig3/std_gru.png
