BailabUNC/LaHMo/results/fig3/std_lstm.png

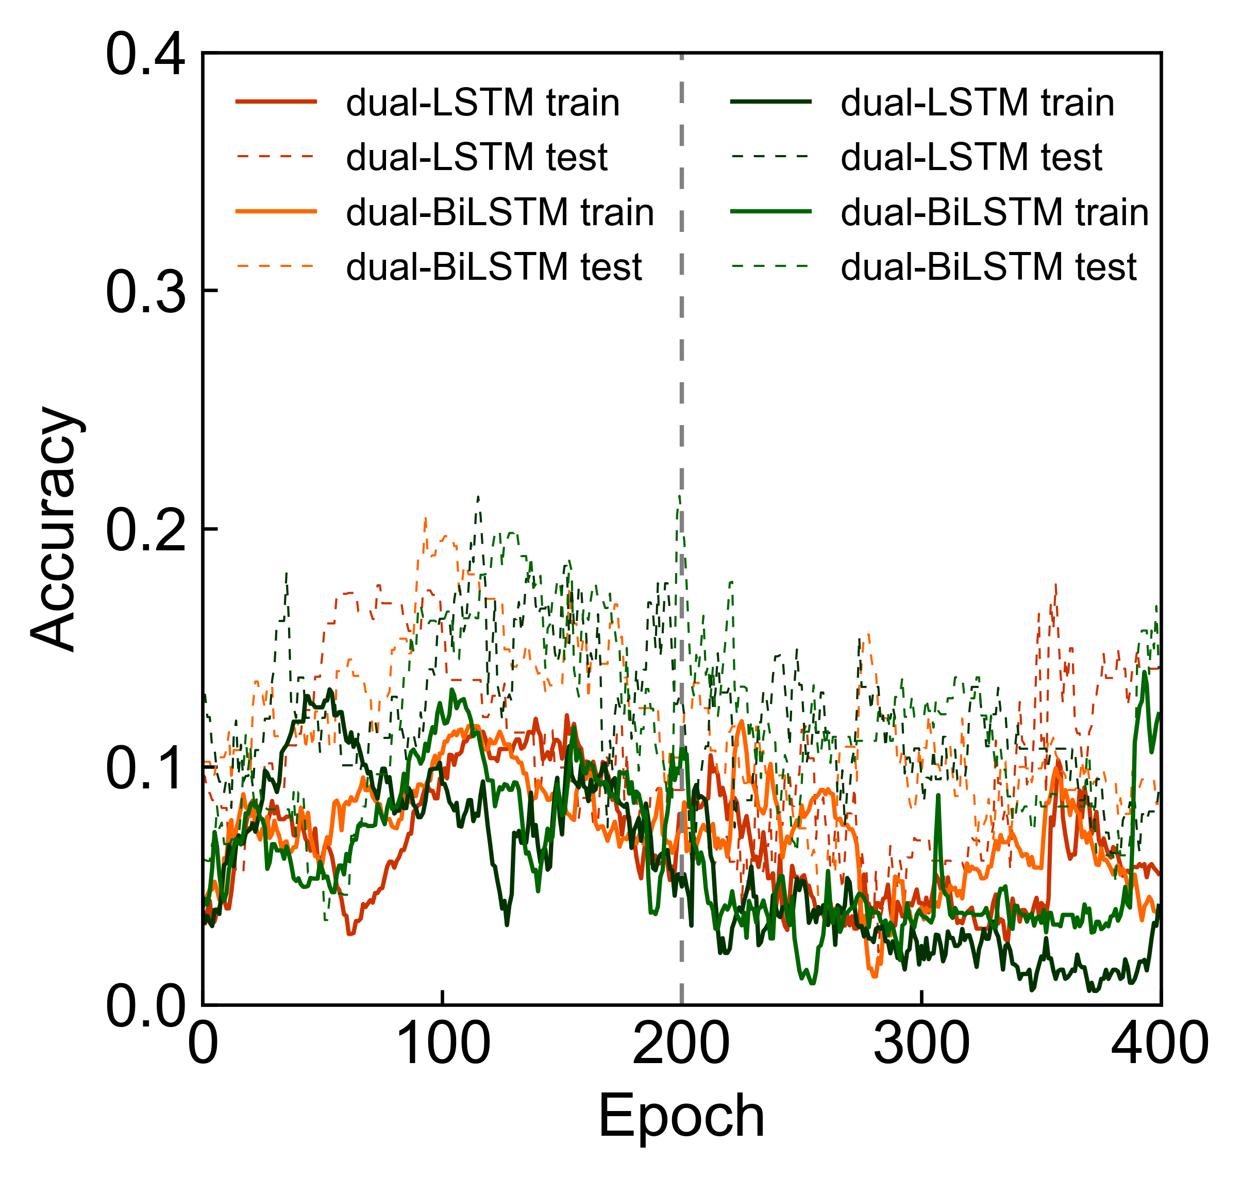
results/fig3/std_lstm.png
