BailabUNC/LaHMo/results/fig3/train_vs_test_frnn.png

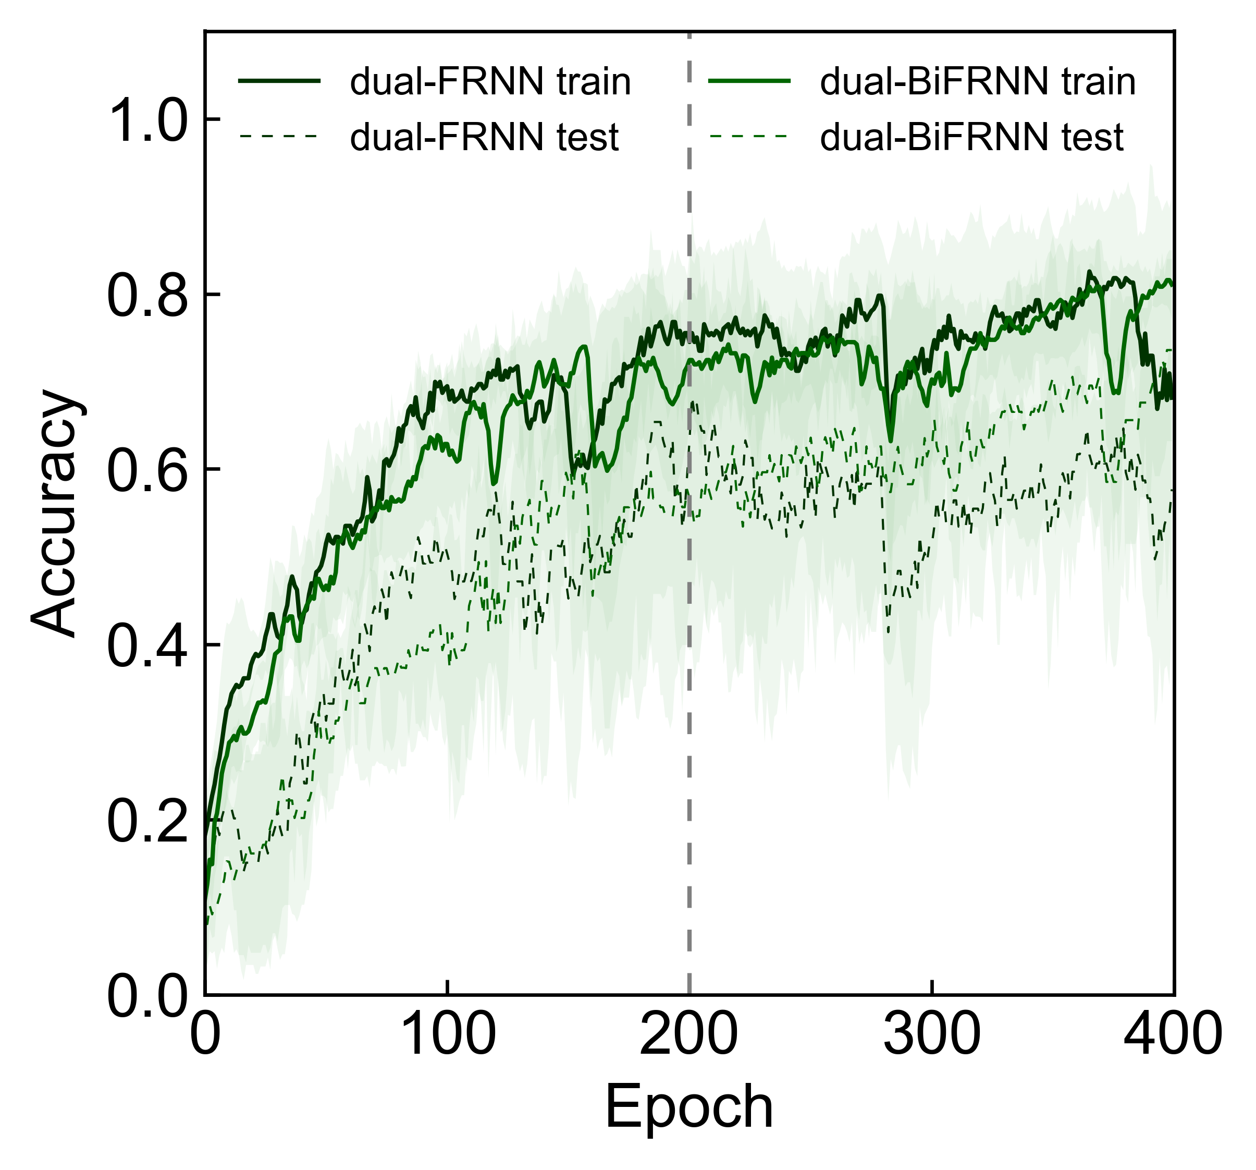
results/fig3/train_vs_test_frnn.png
