BailabUNC/LaHMo/results/fig3/train_vs_test_gru.png

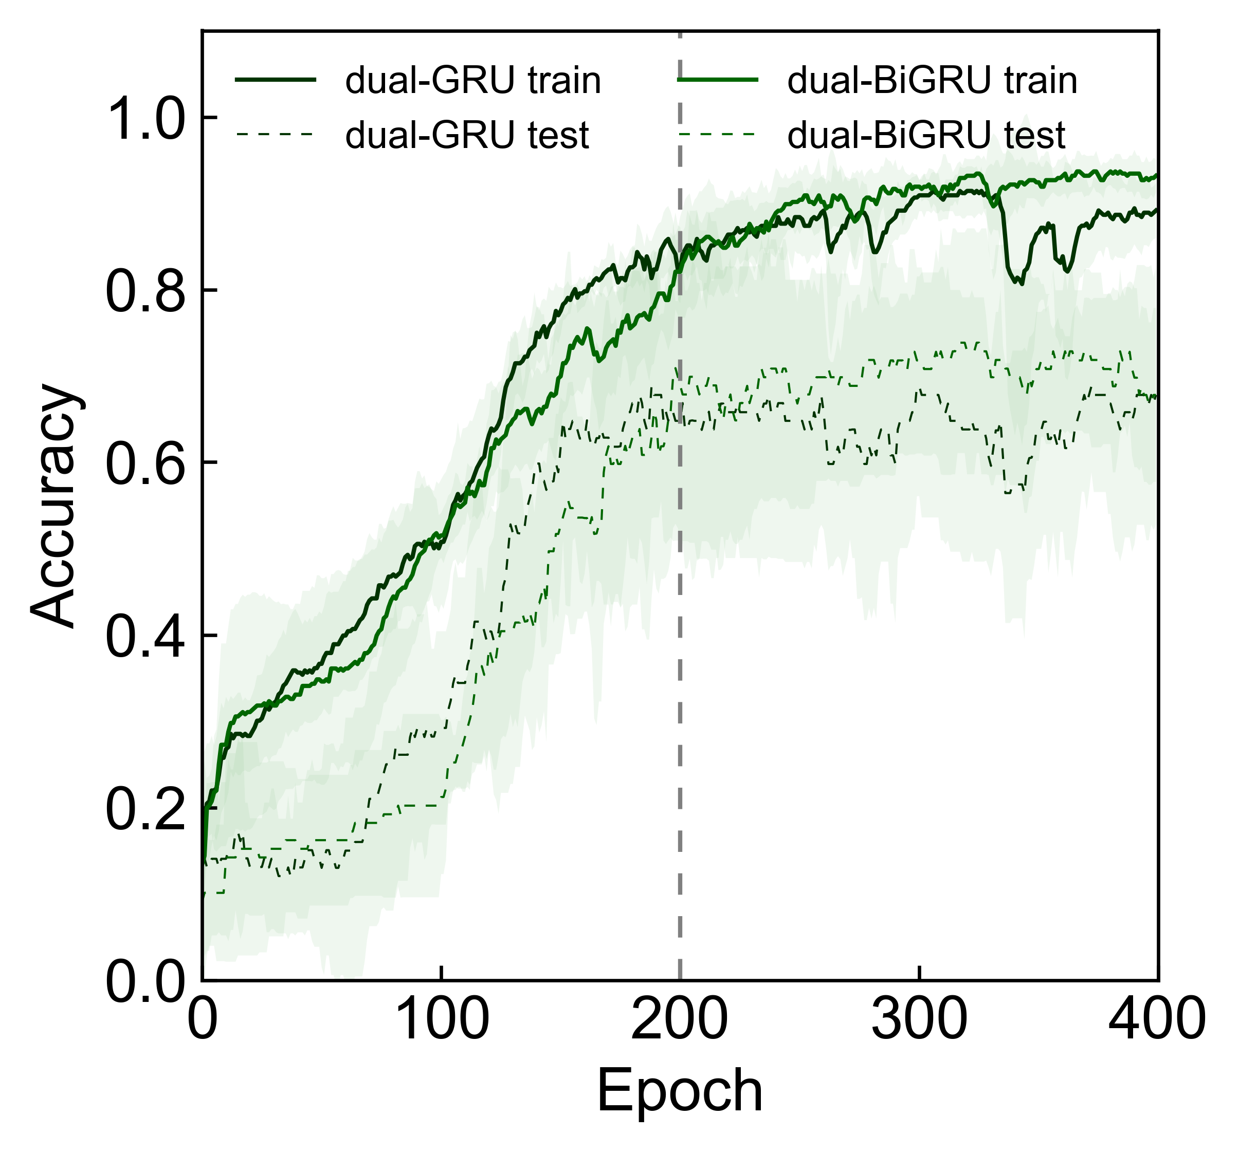
results/fig3/train_vs_test_gru.png
