BailabUNC/LaHMo/results/fig3/train_vs_test_lstm.png

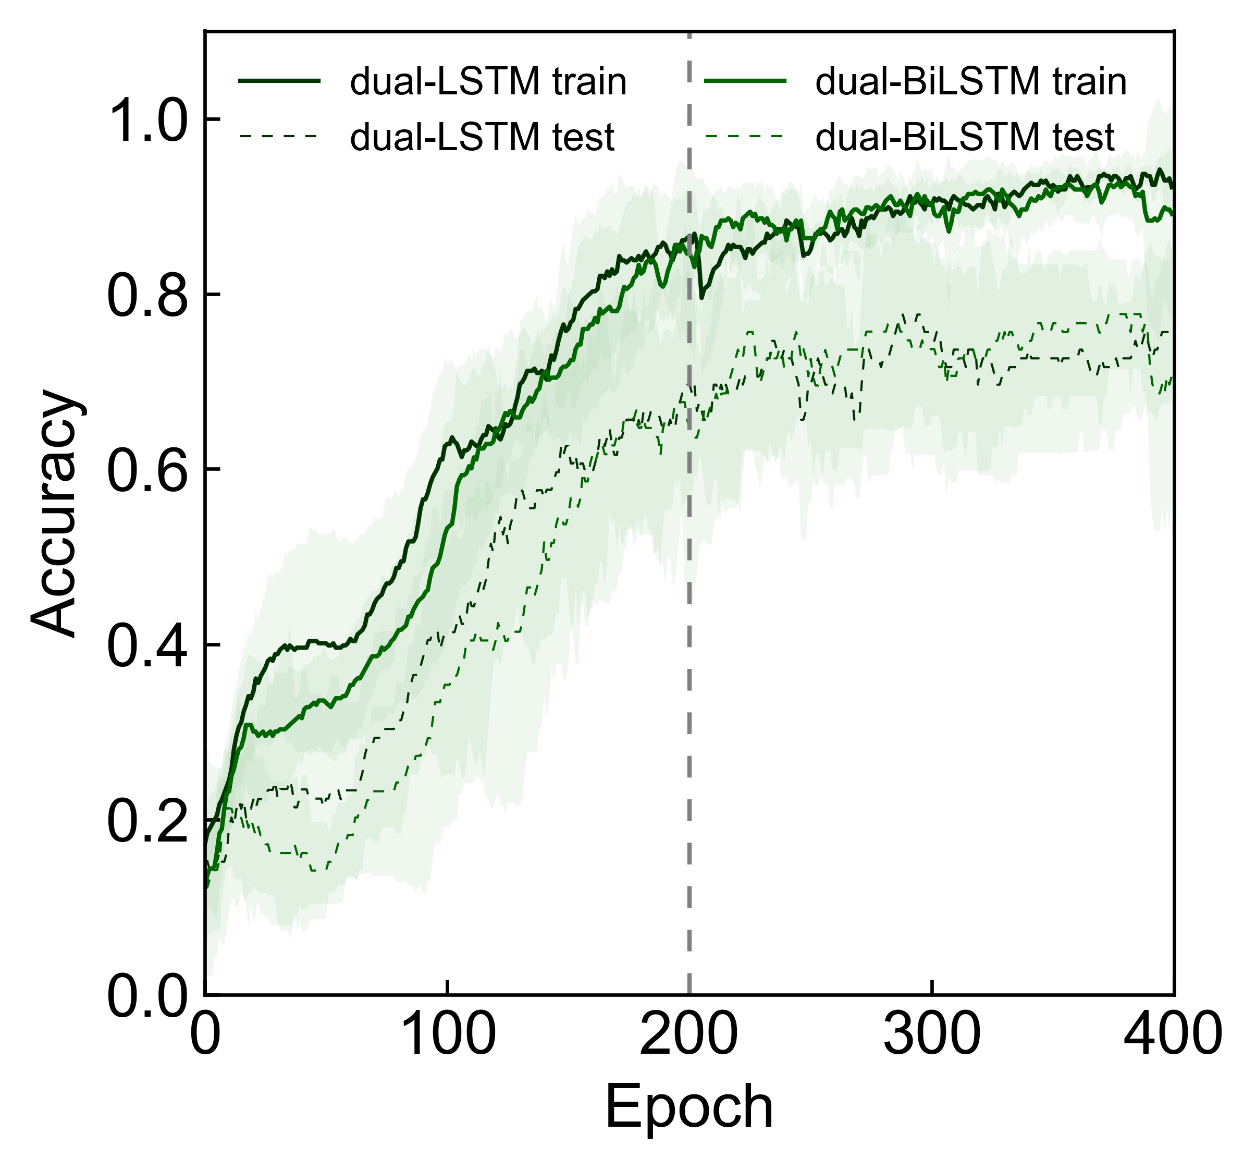
results/fig3/train_vs_test_lstm.png
