BailabUNC/LaHMo/results/fig3/train_vs_test_mono_frnn.png

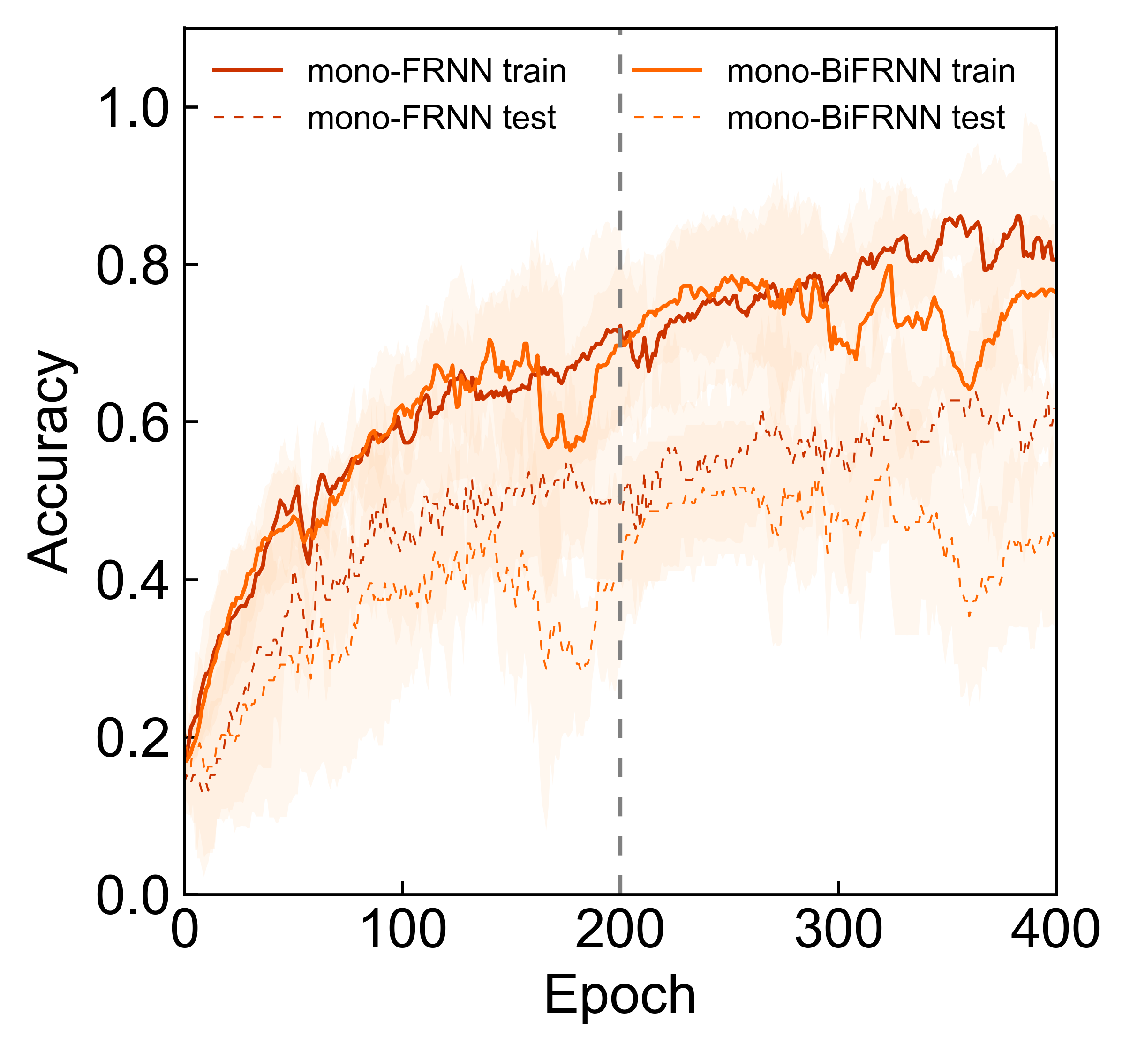
results/fig3/train_vs_test_mono_frnn.png
