BailabUNC/LaHMo/results/fig3/visualization/architechture.37.png

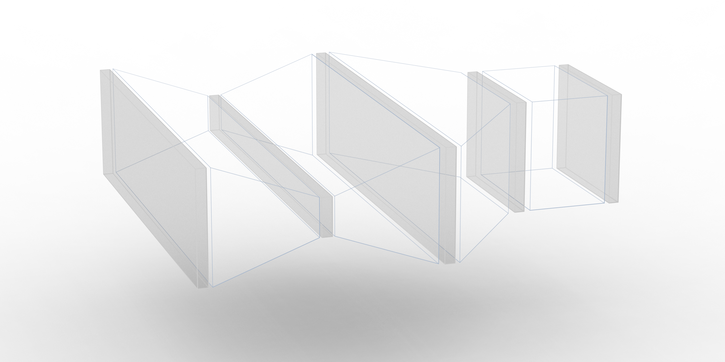
results/fig3/visualization/architechture.37.png
