BailabUNC/LaHMo/results/fig3/visualization/architechture.38.png

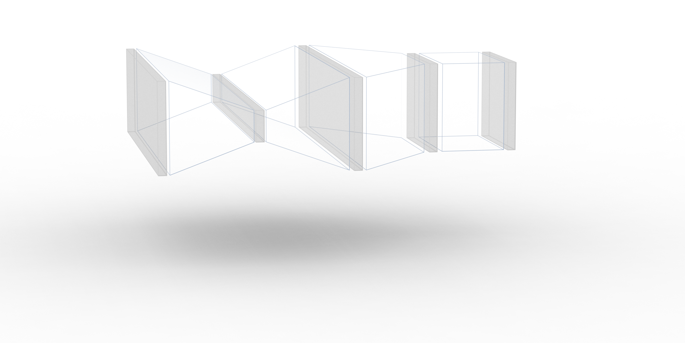
results/fig3/visualization/architechture.38.png
