BailabUNC/LaHMo/results/fig3/visualization/architechture.39.png

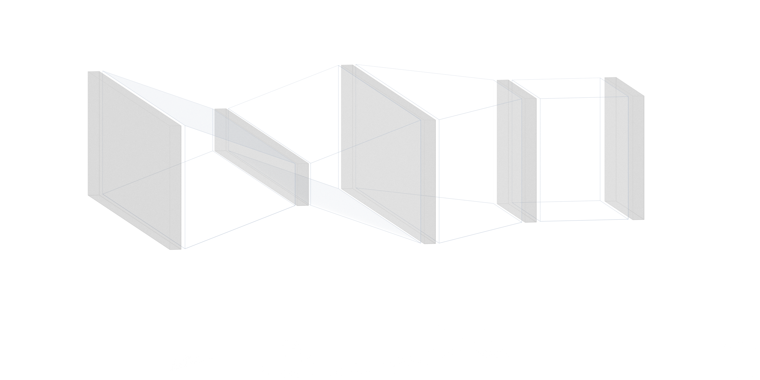
results/fig3/visualization/architechture.39.png
