BailabUNC/LaHMo/results/fig3/visualization/architechture.40.png

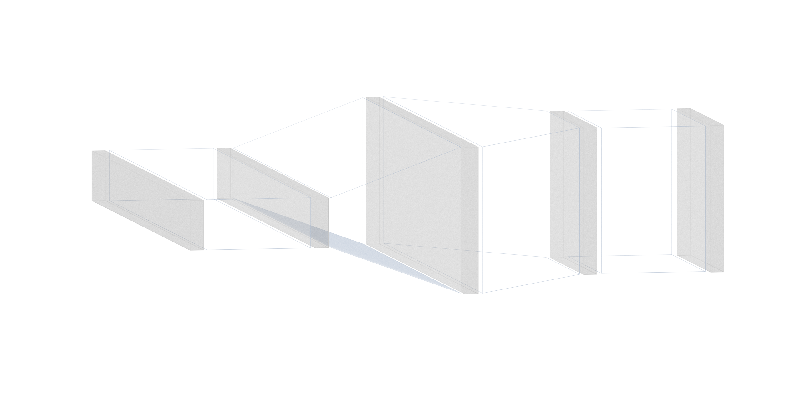
results/fig3/visualization/architechture.40.png
