BailabUNC/LaHMo/results/fig3/visualization/architechture.41.png

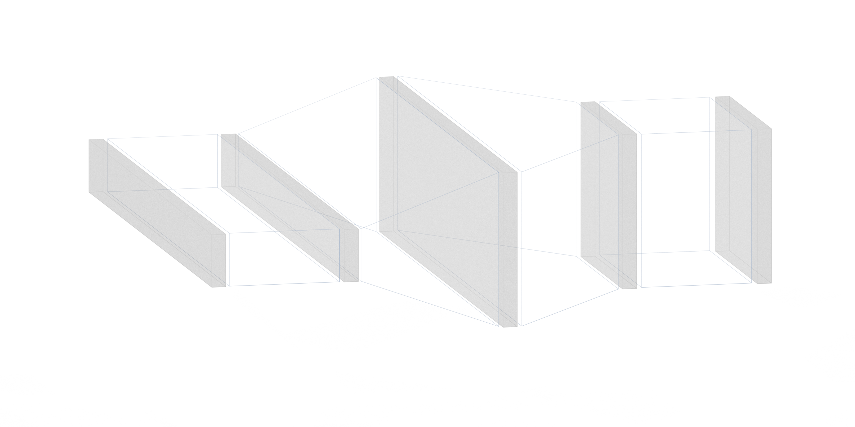
results/fig3/visualization/architechture.41.png
