BailabUNC/LaHMo/results/fig3/visualization/CodeCogsEqn.png

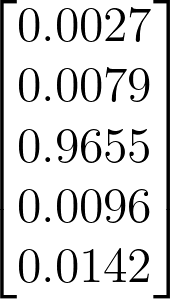
results/fig3/visualization/CodeCogsEqn.png
