BailabUNC/LaHMo/results/fig3/visualization/raw.png

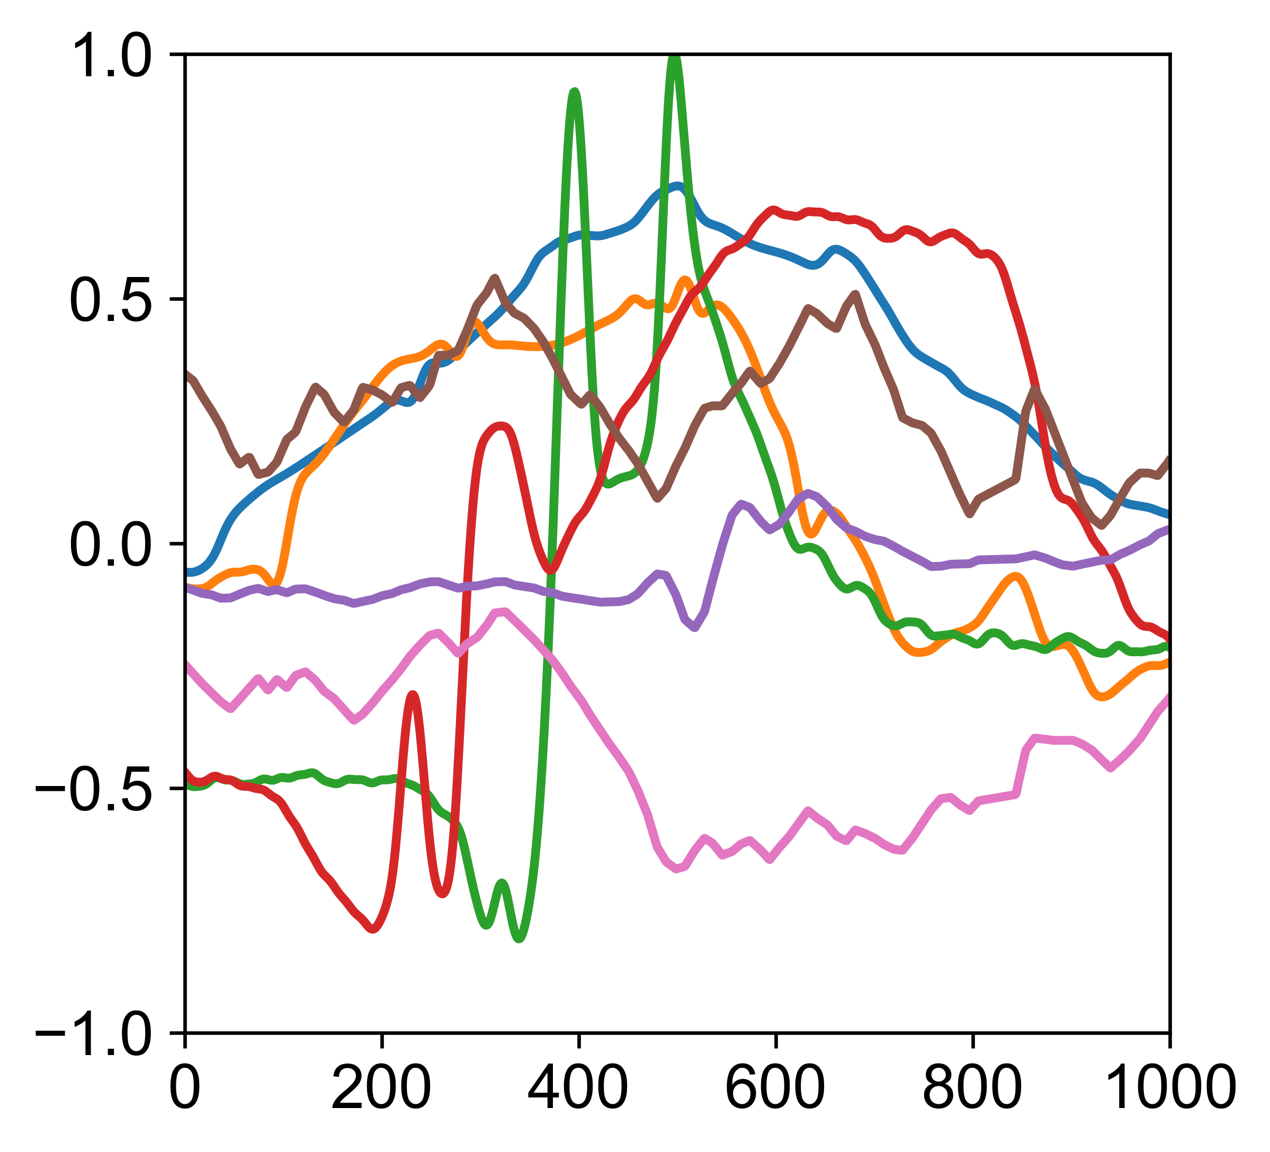
results/fig3/visualization/raw.png
