BailabUNC/LaHMo/results/fig3/visualization/render.34.png

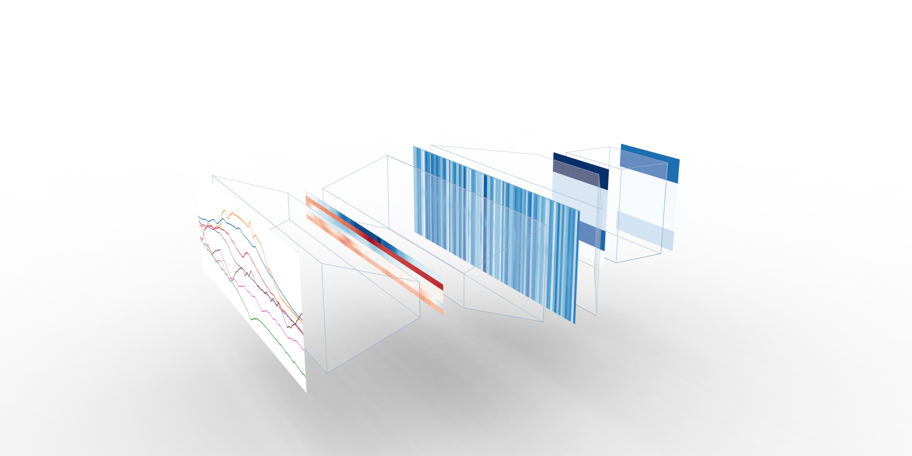
results/fig3/visualization/render.34.png
