BailabUNC/LaHMo/results/fig3/visualization/render.35.png

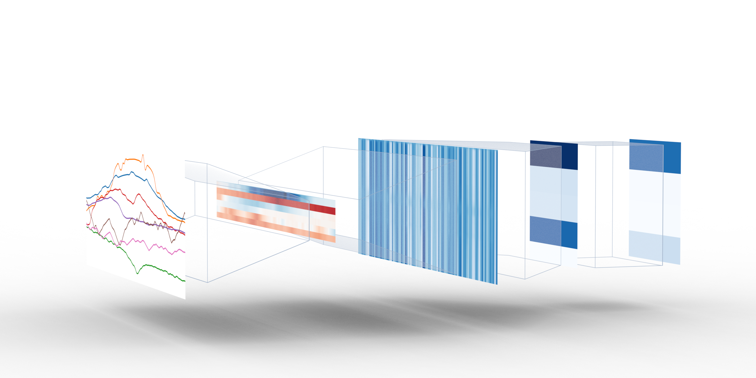
results/fig3/visualization/render.35.png
