BailabUNC/LaHMo/results/fig3/visualization/render.36.png

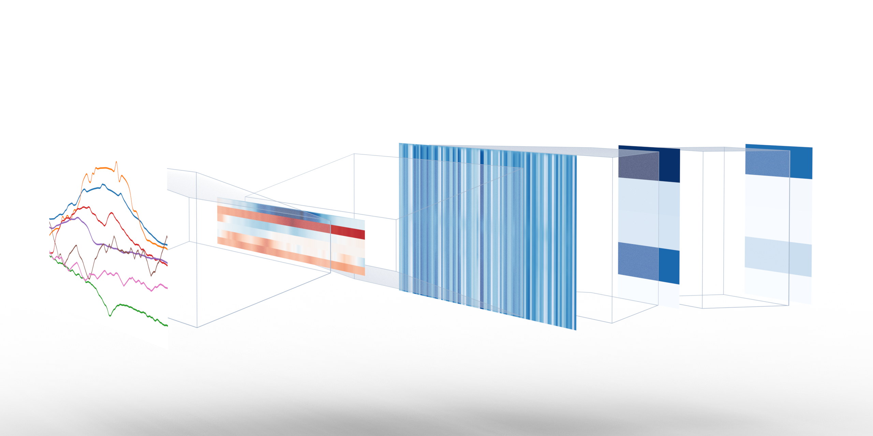
results/fig3/visualization/render.36.png
