BailabUNC/LaHMo/results/fig4/1.png

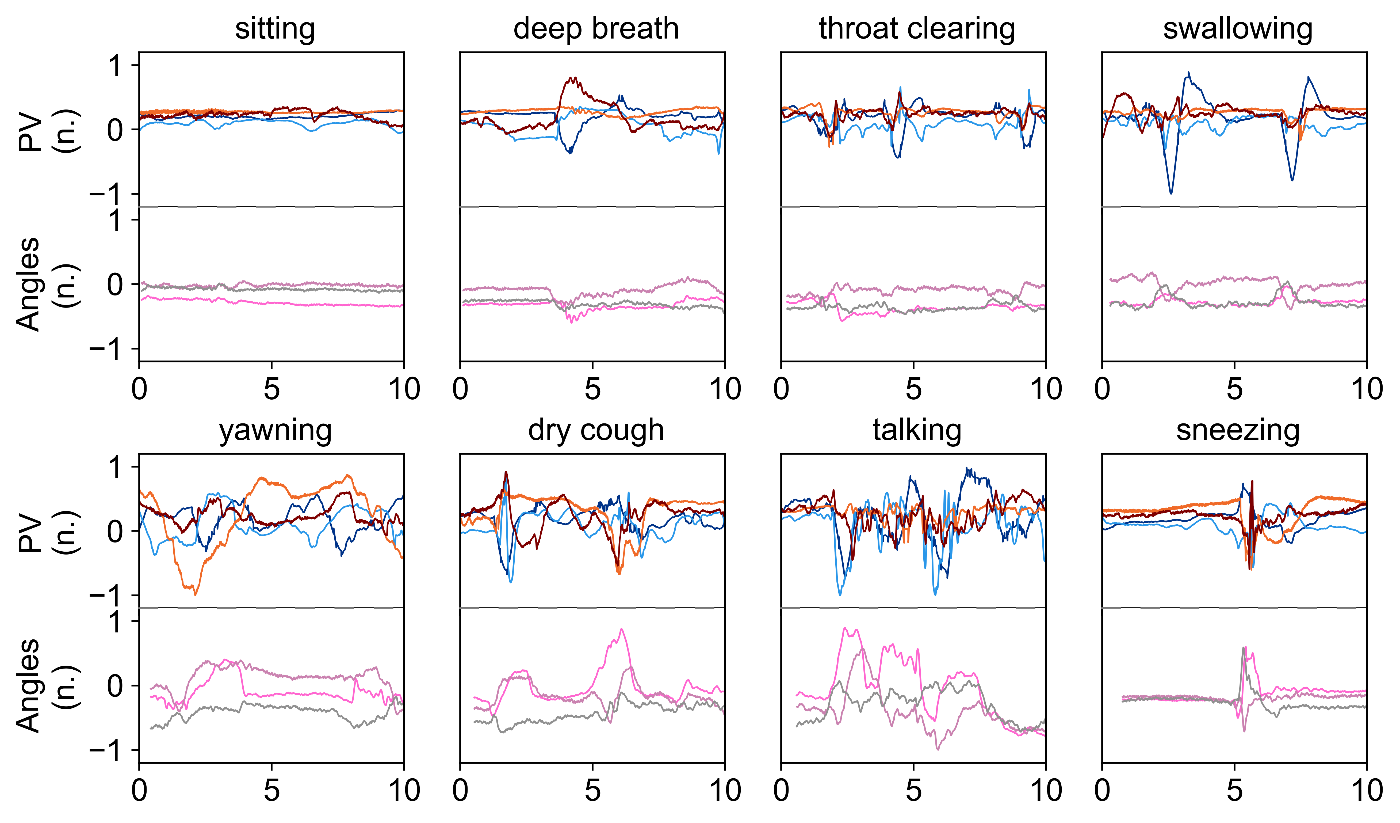
results/fig4/1.png
