BailabUNC/LaHMo/results/fig4/1.webp

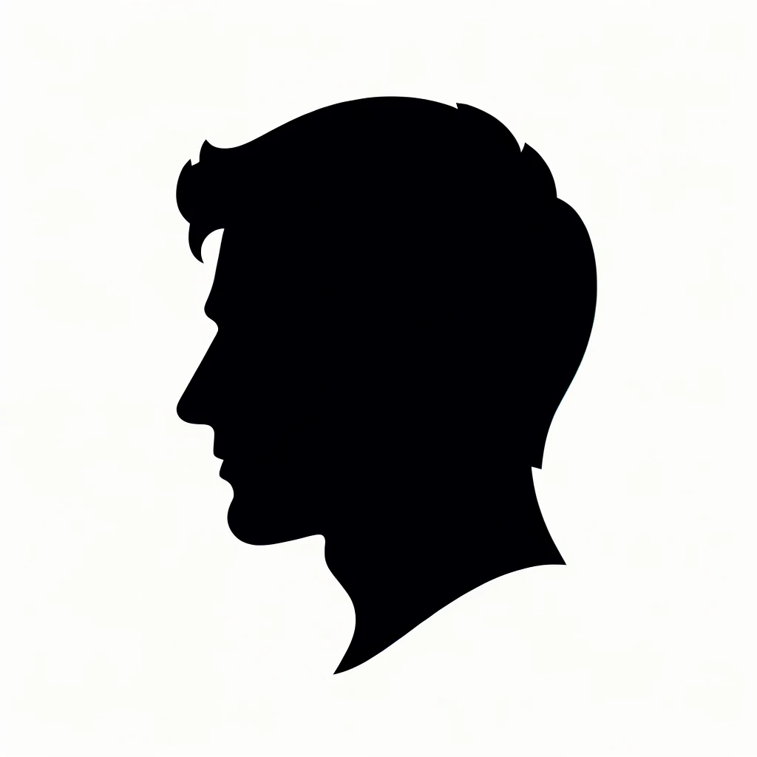
results/fig4/1.webp
