BailabUNC/LaHMo/results/fig4/2.png

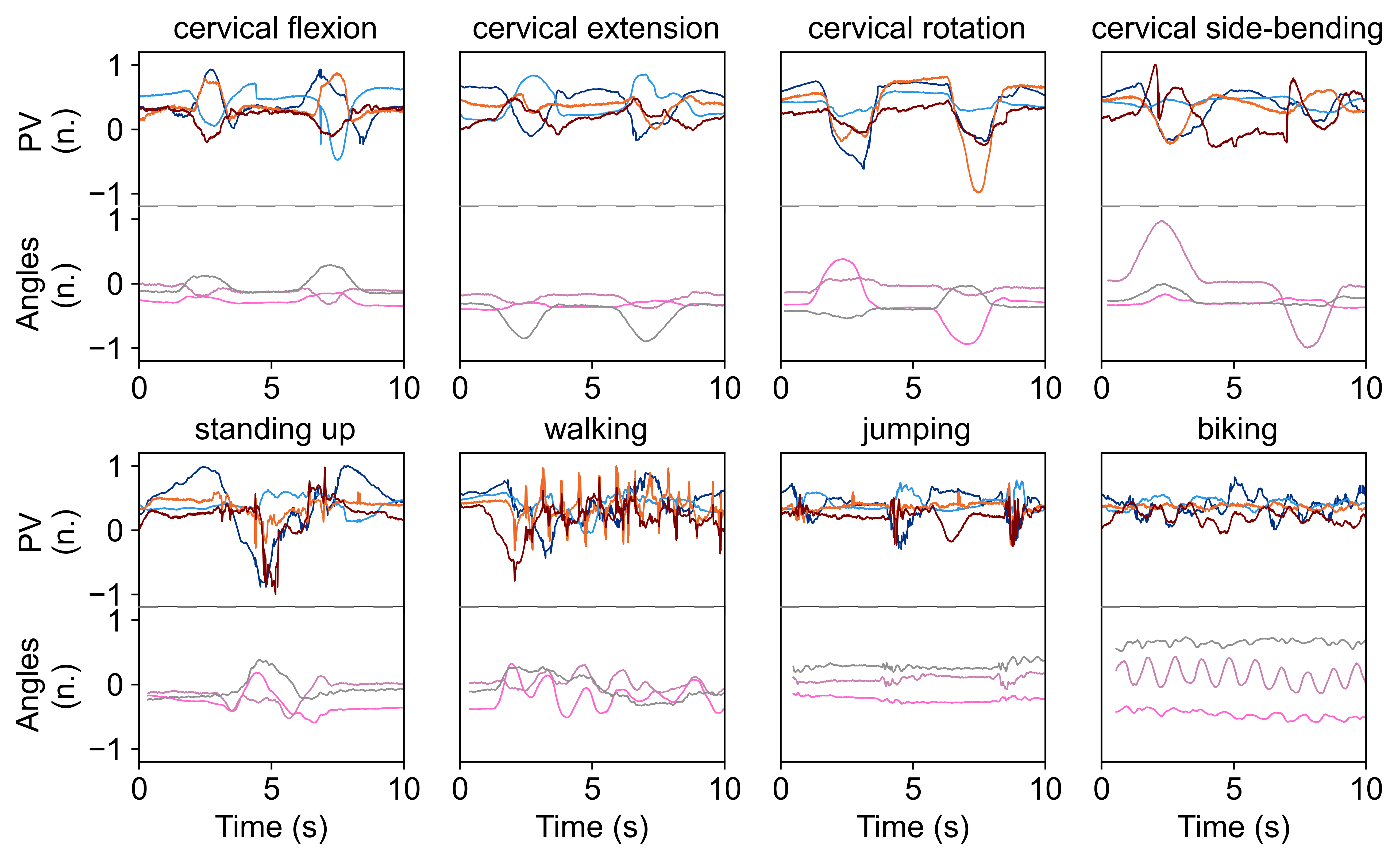
results/fig4/2.png
