BailabUNC/LaHMo/results/fig4/2.webp

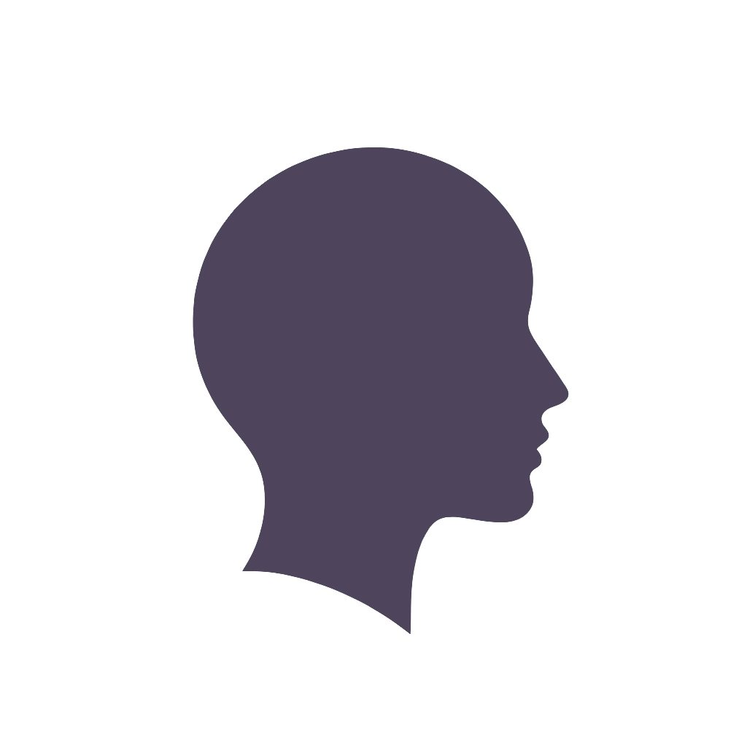
results/fig4/2.webp
