BailabUNC/LaHMo/results/fig4/adap_all.png

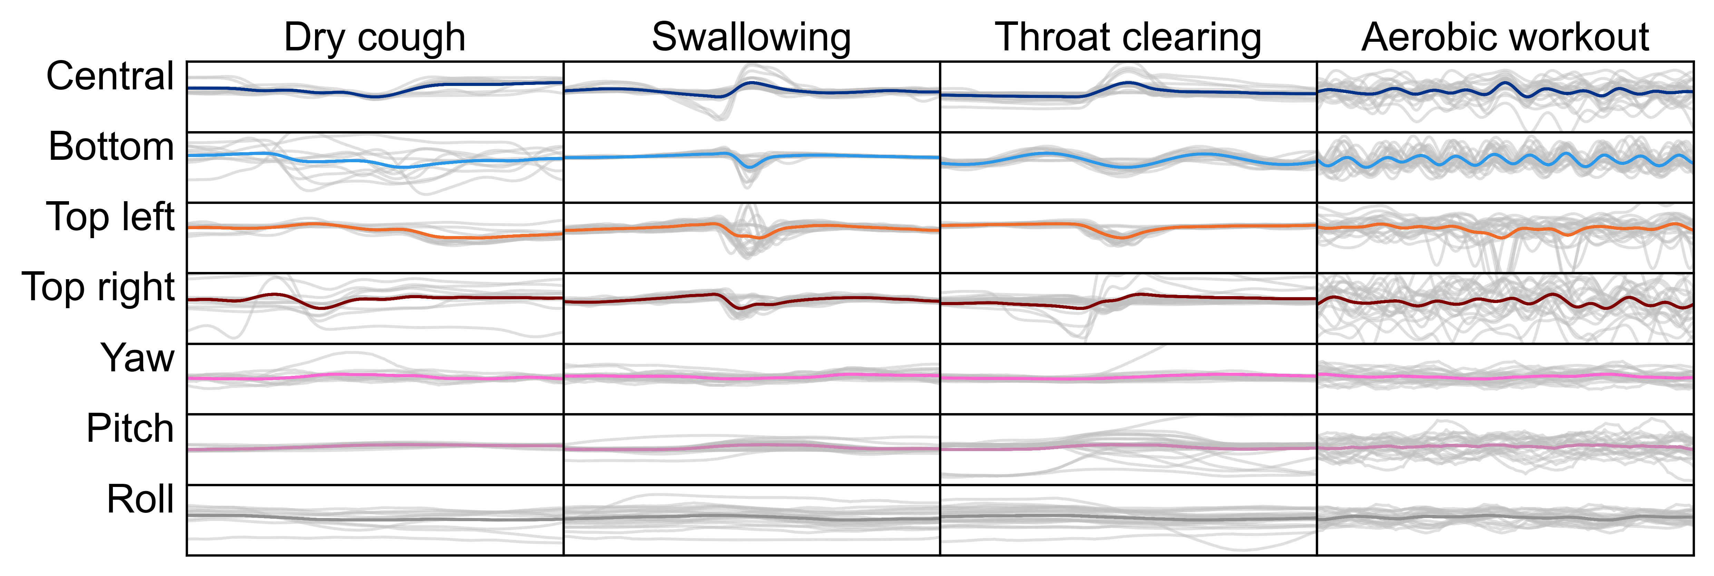
results/fig4/adap_all.png
