BailabUNC/LaHMo/results/fig4/adap_confusion_mat.png

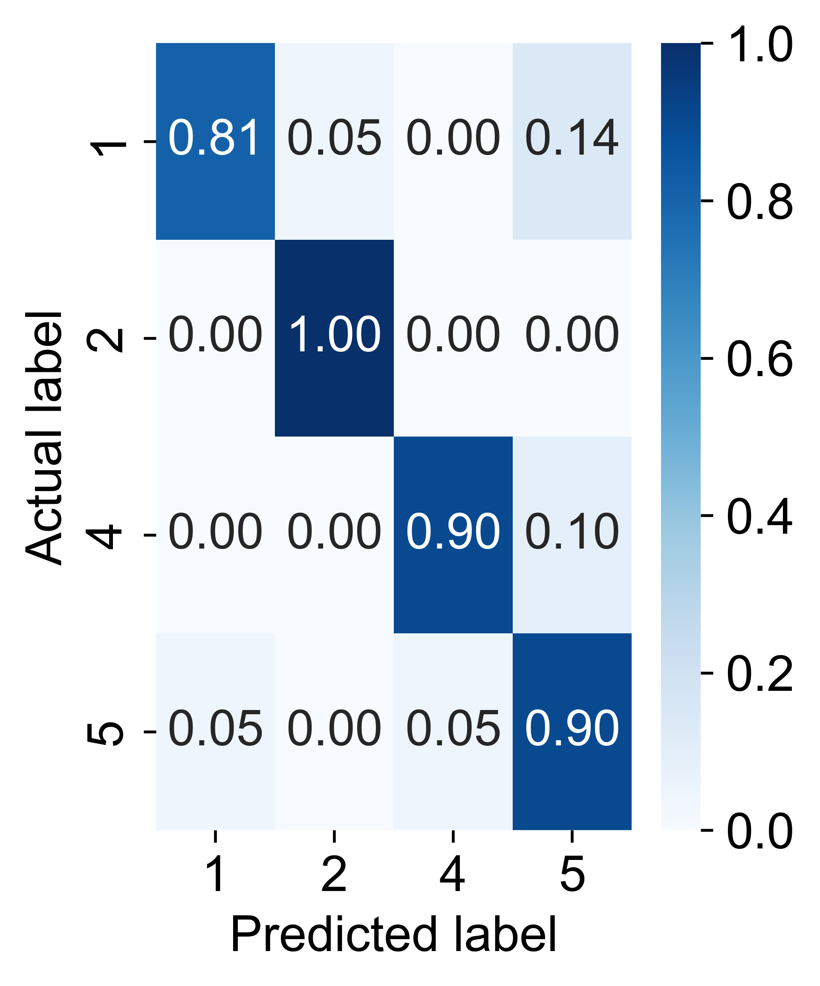
results/fig4/adap_confusion_mat.png
