BailabUNC/LaHMo/results/fig4/adap_vs_dual.png

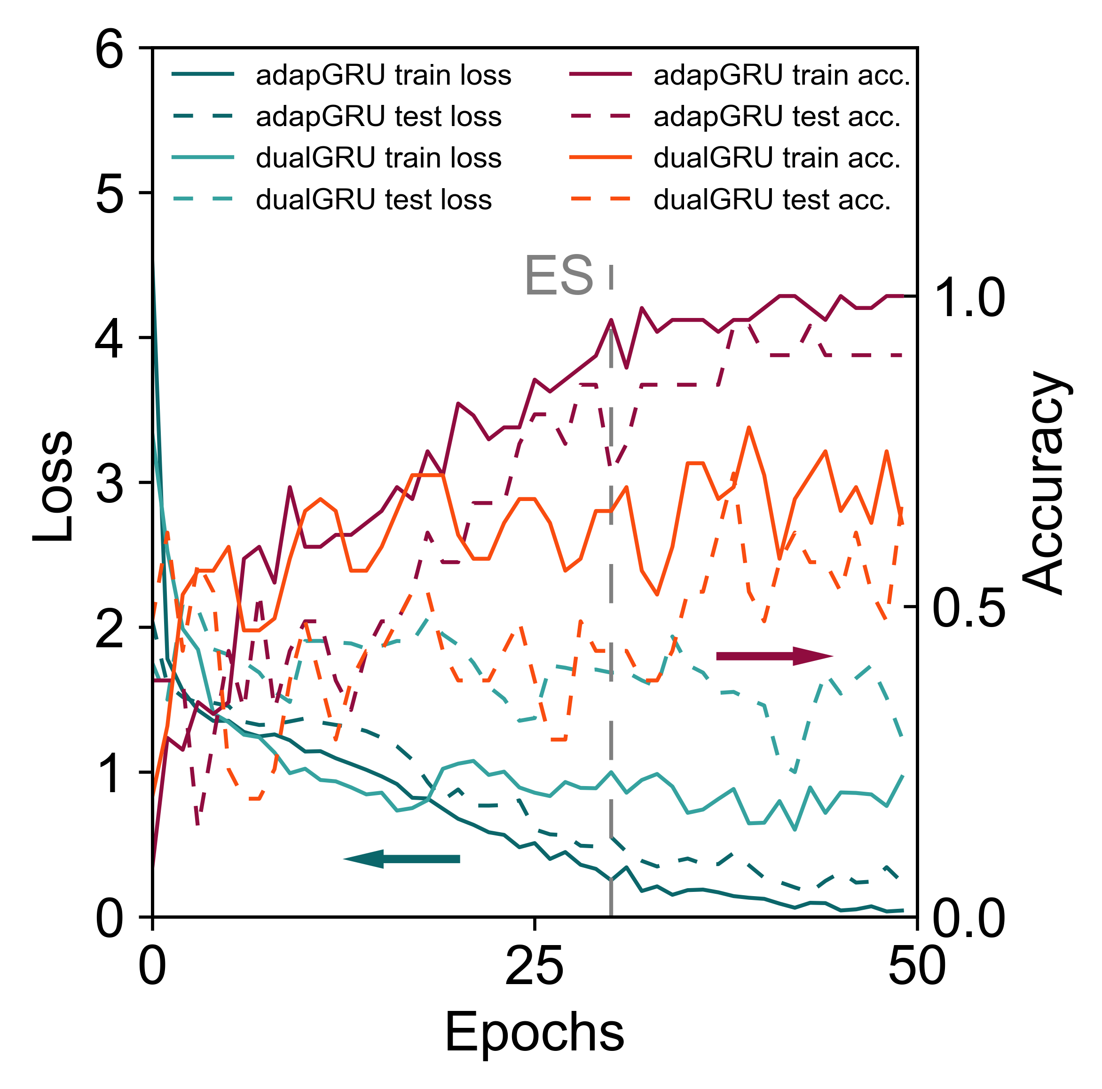
results/fig4/adap_vs_dual.png
