BailabUNC/LaHMo/results/fig4/continuous1.png

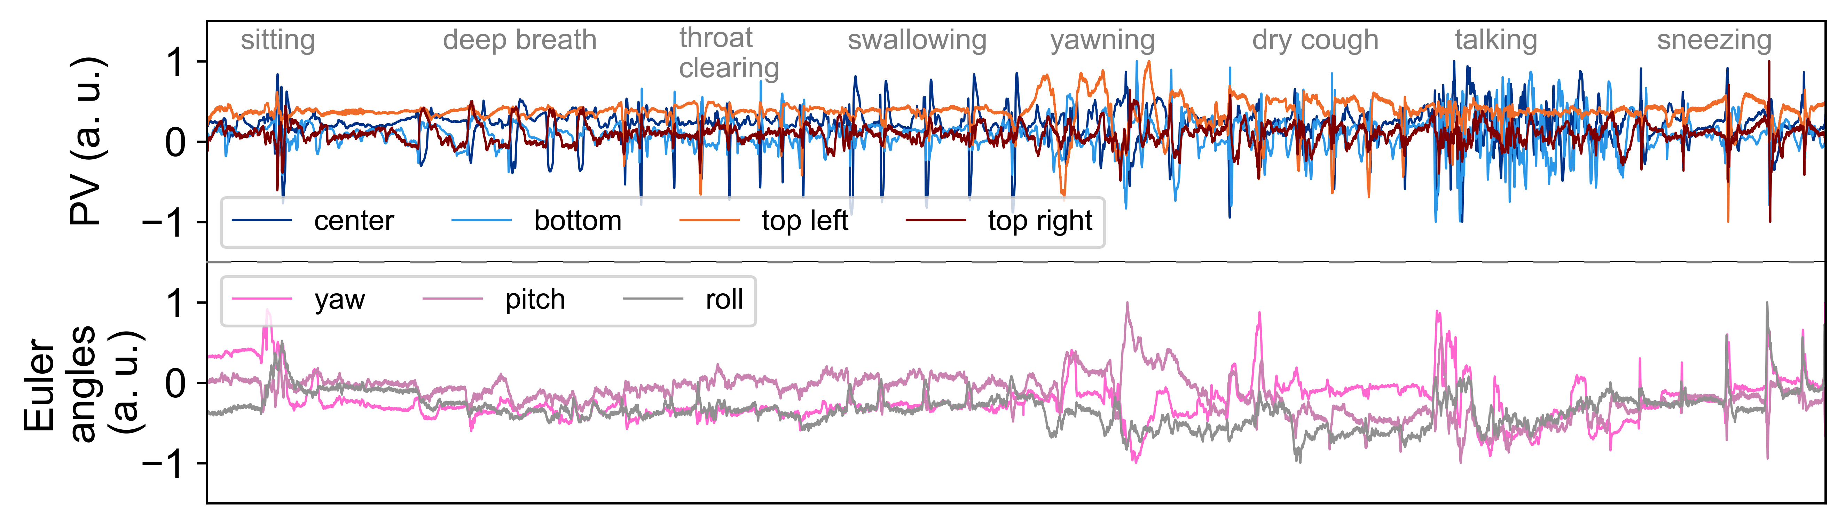
results/fig4/continuous1.png
