BailabUNC/LaHMo/results/fig4/continuous2.png

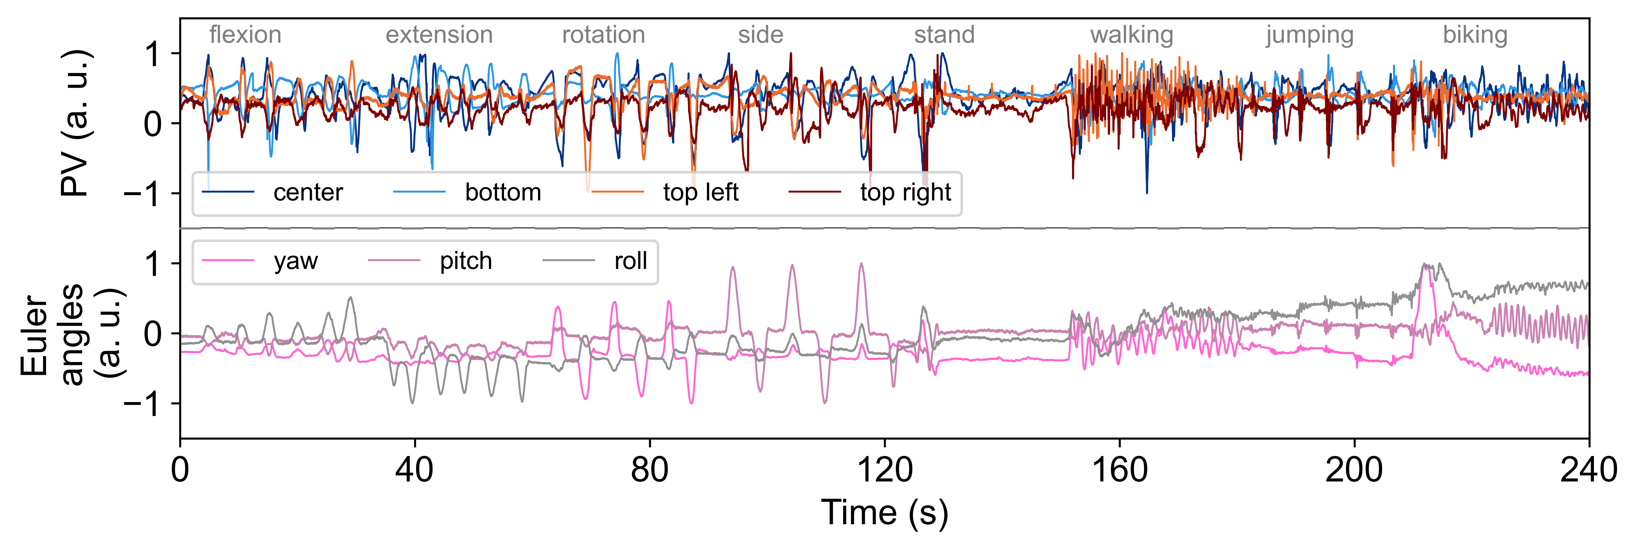
results/fig4/continuous2.png
