BailabUNC/LaHMo/results/fig5/all.png

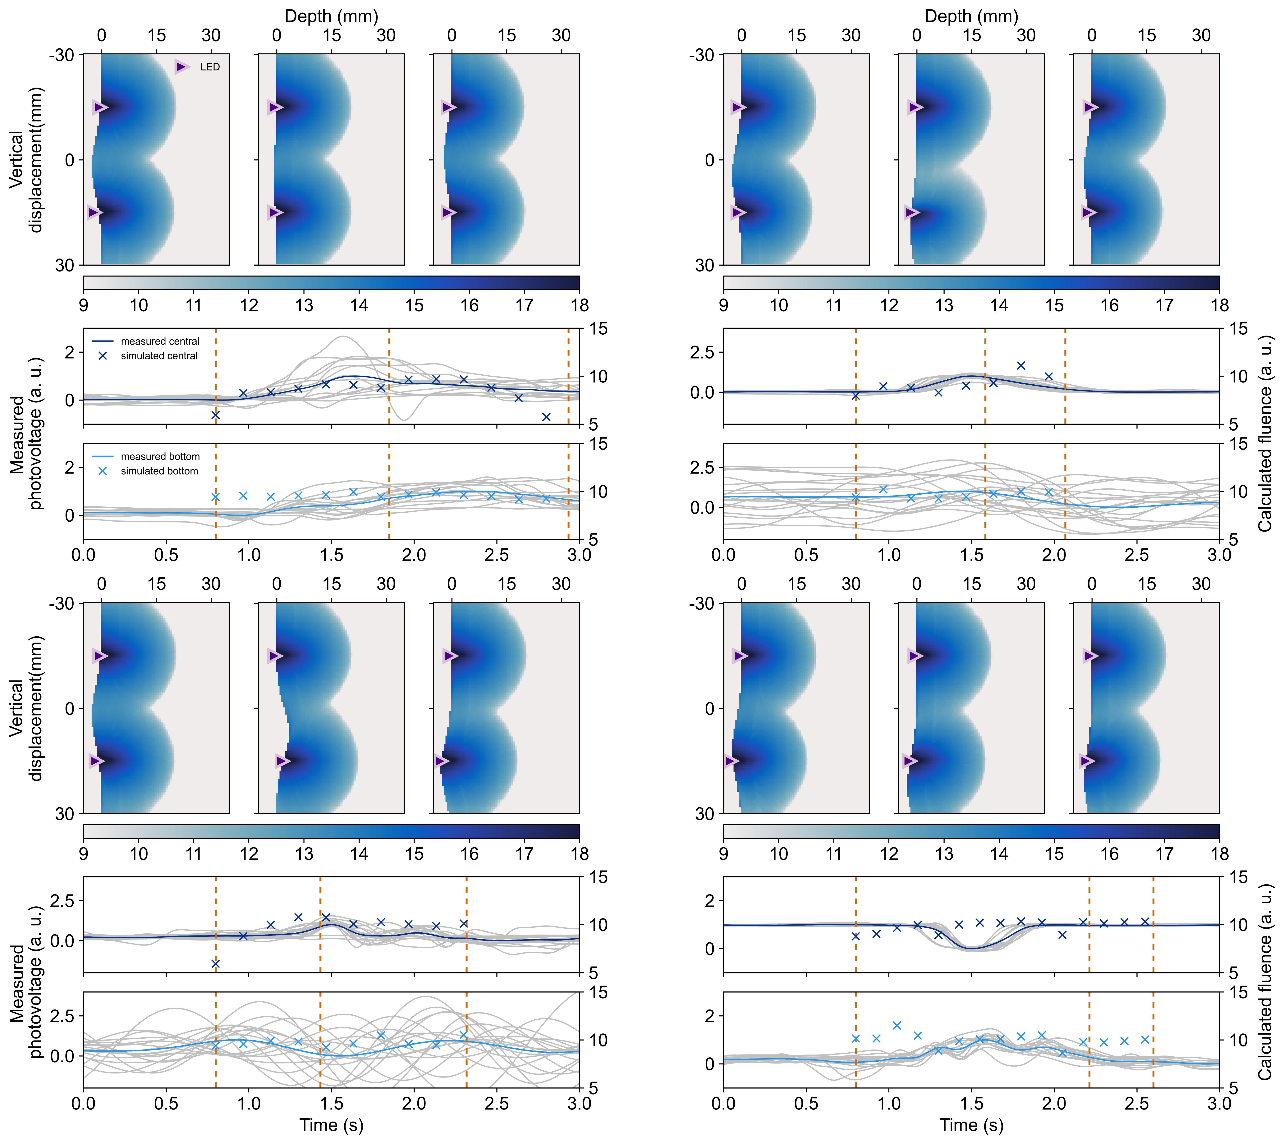
results/fig5/all.png
