BailabUNC/LaHMo/results/fig5/cross_correlation/deep breath.png

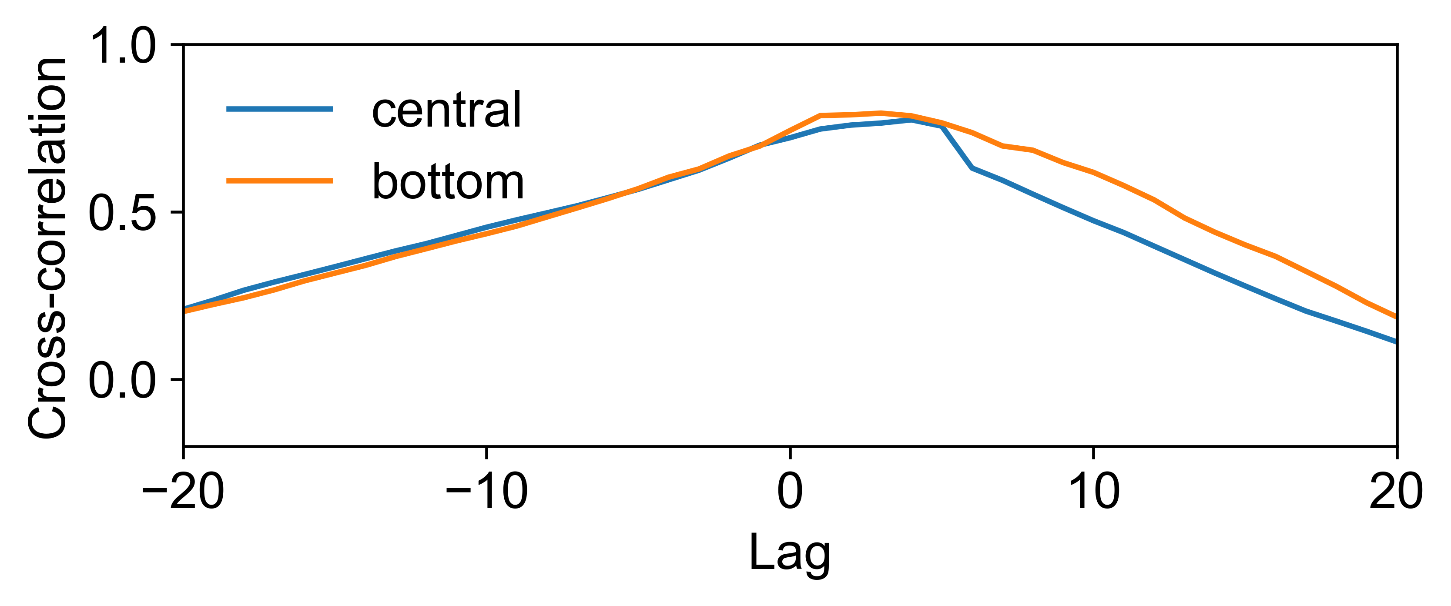
results/fig5/cross_correlation/deep breath.png
