BailabUNC/LaHMo/results/fig5/cross_correlation/dry cough.png

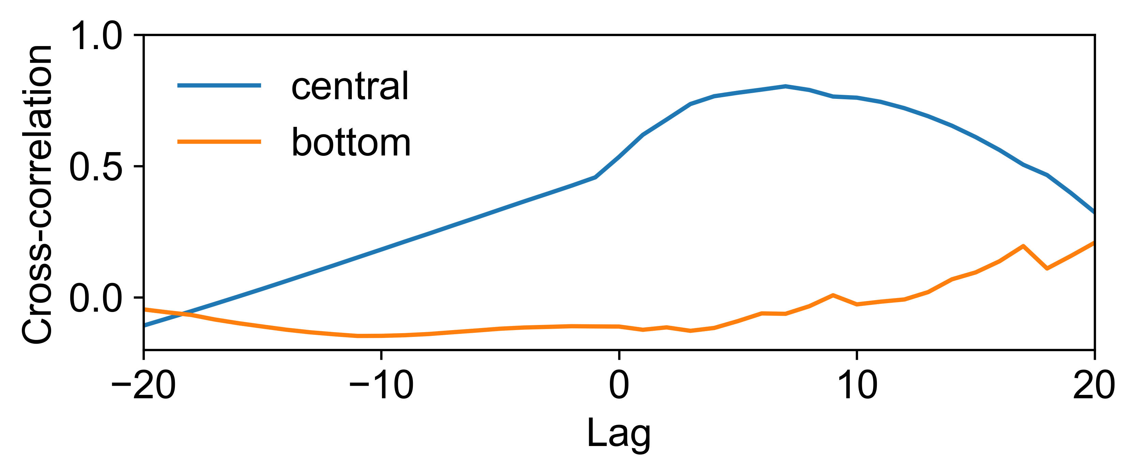
results/fig5/cross_correlation/dry cough.png
