BailabUNC/LaHMo/results/fig5/cross_correlation/swallowing.png

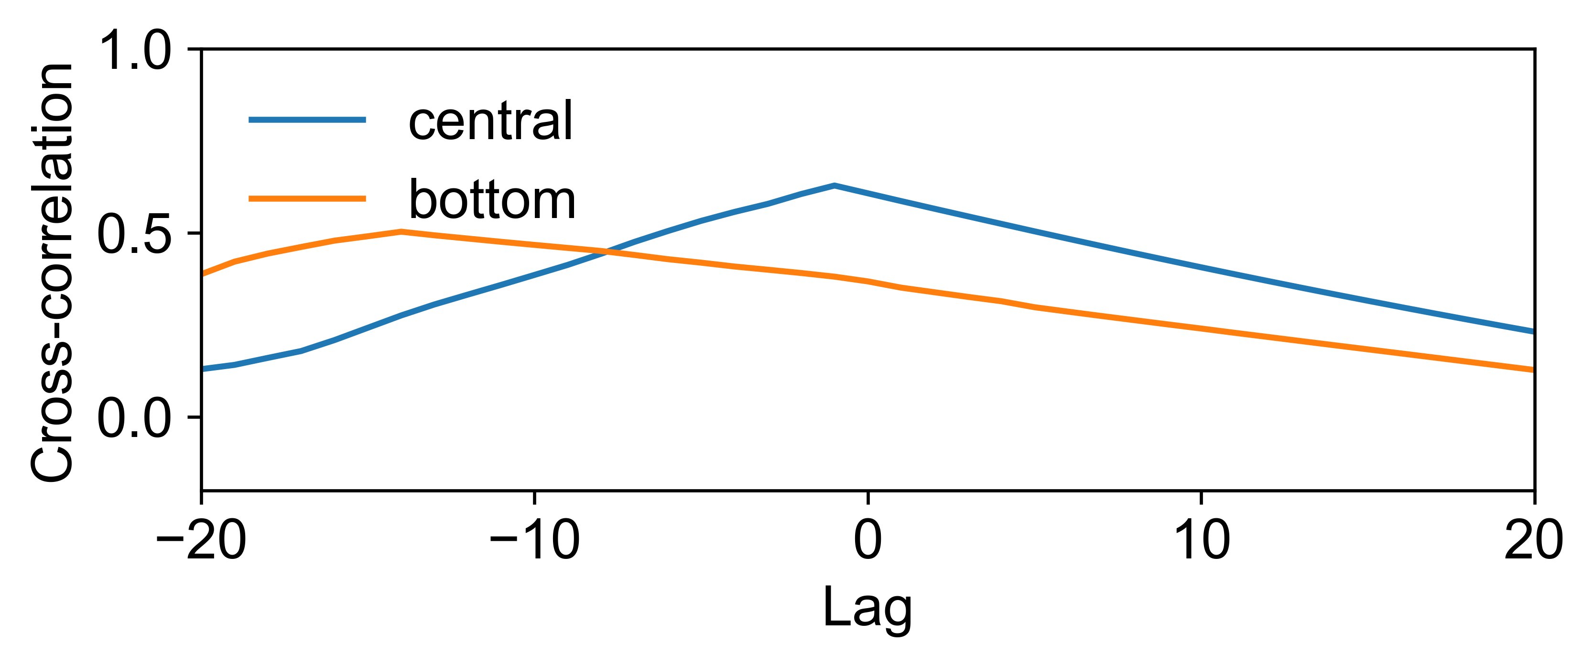
results/fig5/cross_correlation/swallowing.png
