BailabUNC/LaHMo/results/fig5/cross_correlation/throat clearing.png

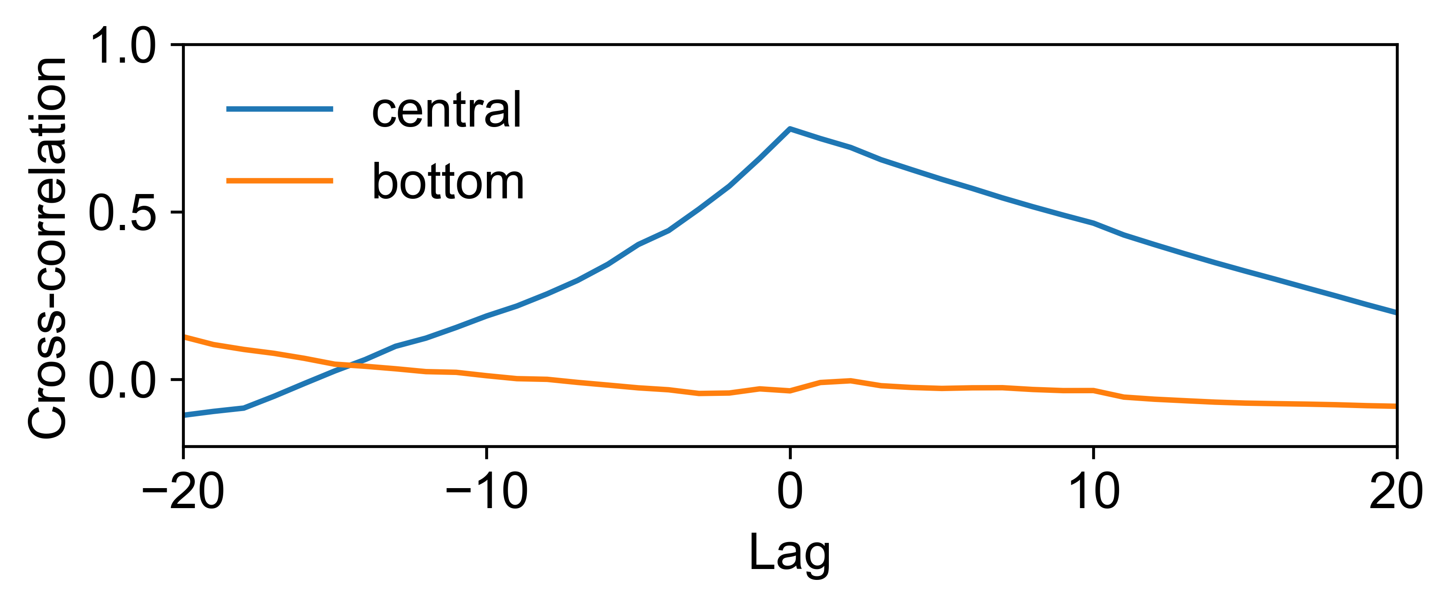
results/fig5/cross_correlation/throat clearing.png
