BailabUNC/LaHMo/results/fig5/deep_breath.png

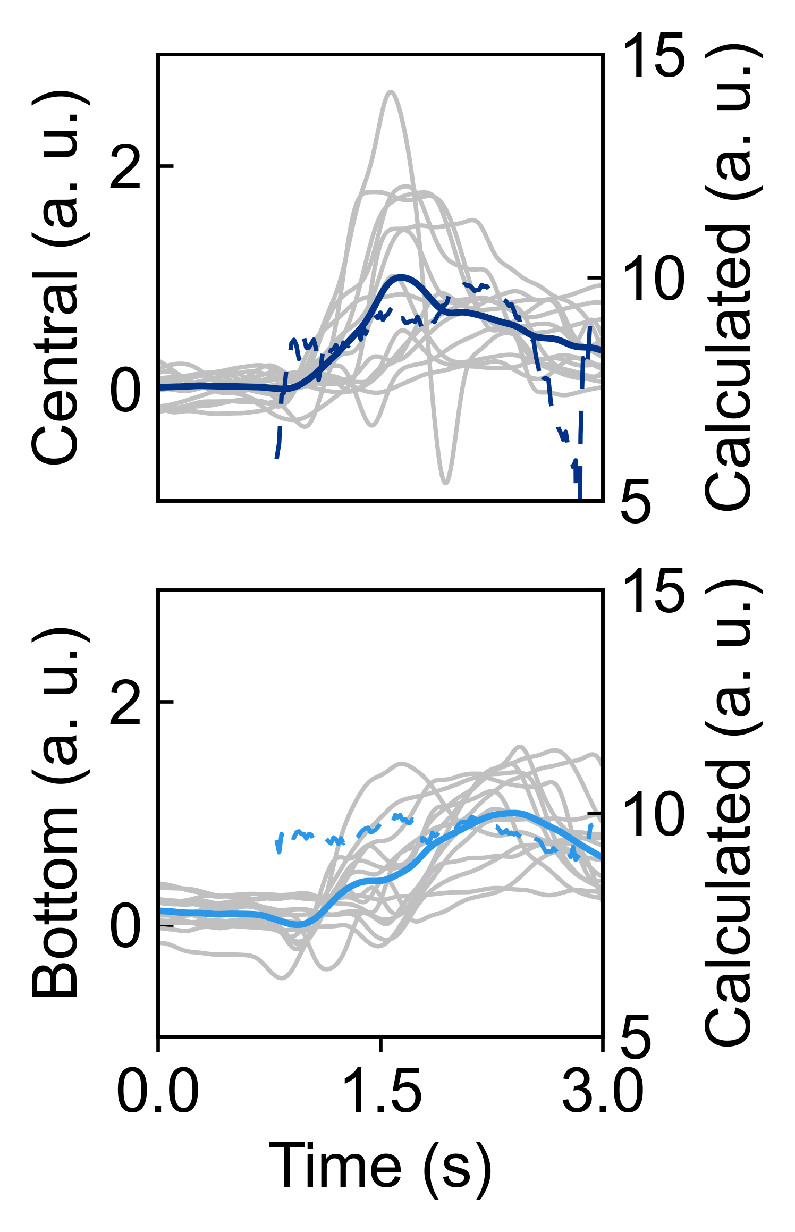
results/fig5/deep_breath.png
