BailabUNC/LaHMo/results/fig5/dry_cough.png

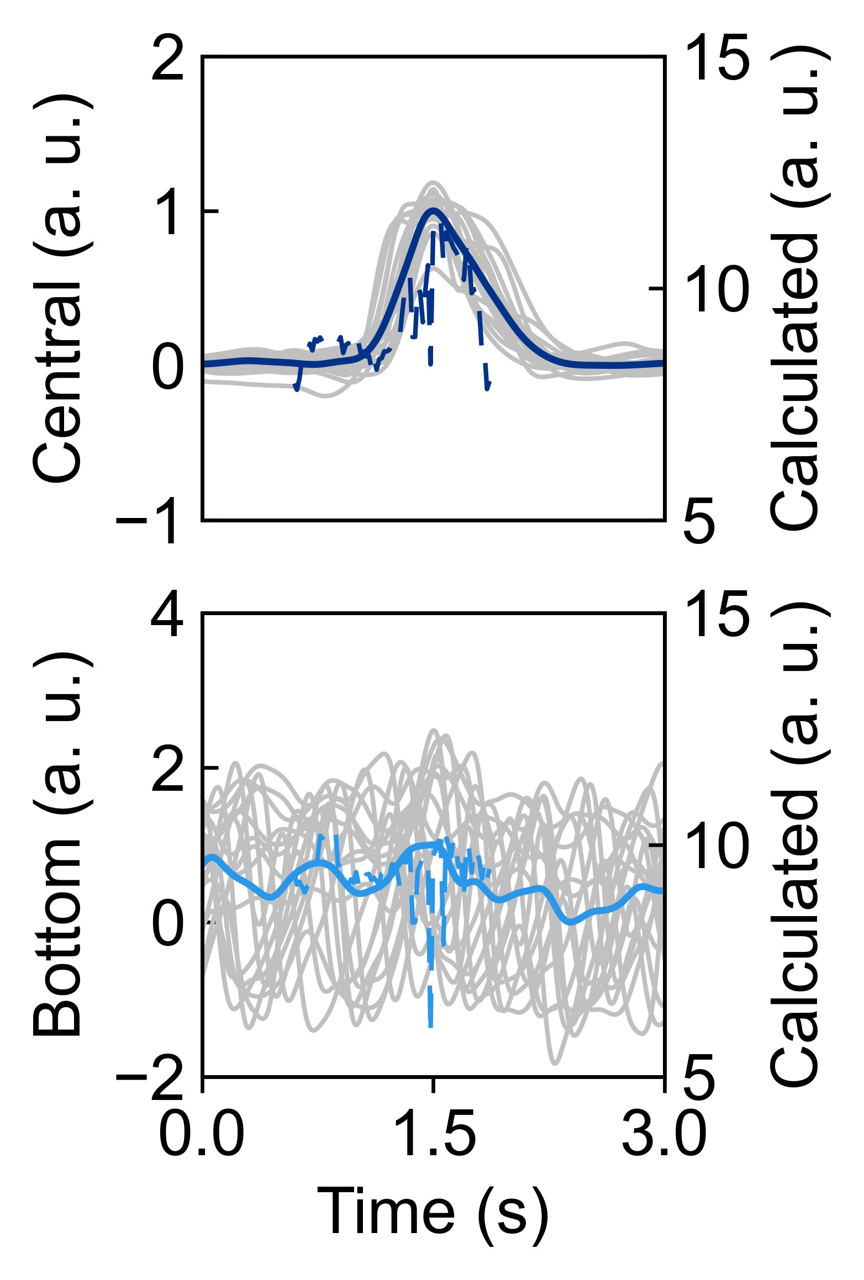
results/fig5/dry_cough.png
