BailabUNC/LaHMo/results/fig5/swallowing.png

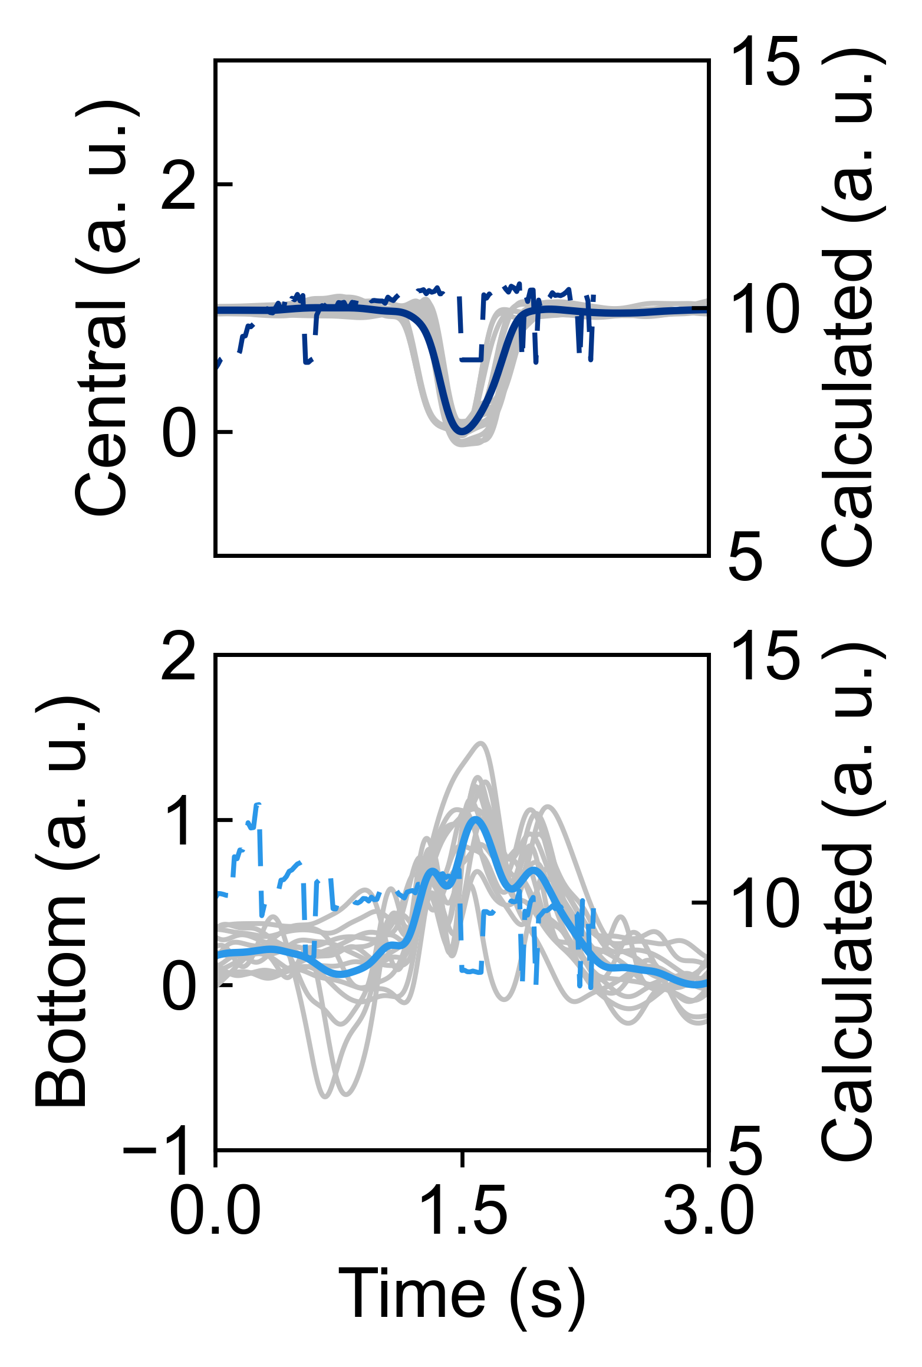
results/fig5/swallowing.png
