BailabUNC/LaHMo/results/fig5/throat_clearing.png

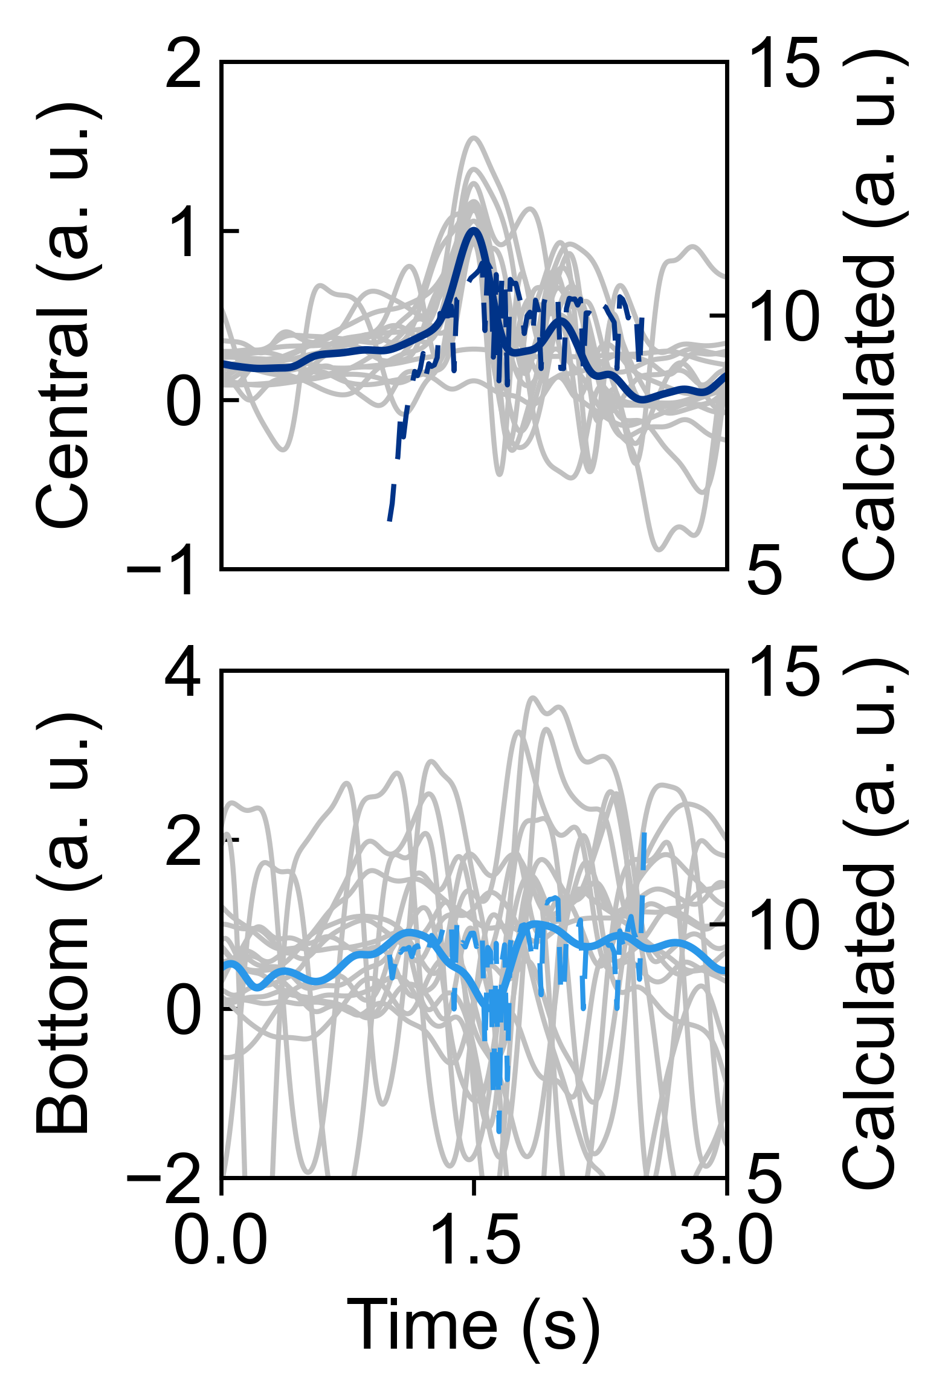
results/fig5/throat_clearing.png
