BailabUNC/LaHMo/results/fig6/basketball_long_test.png

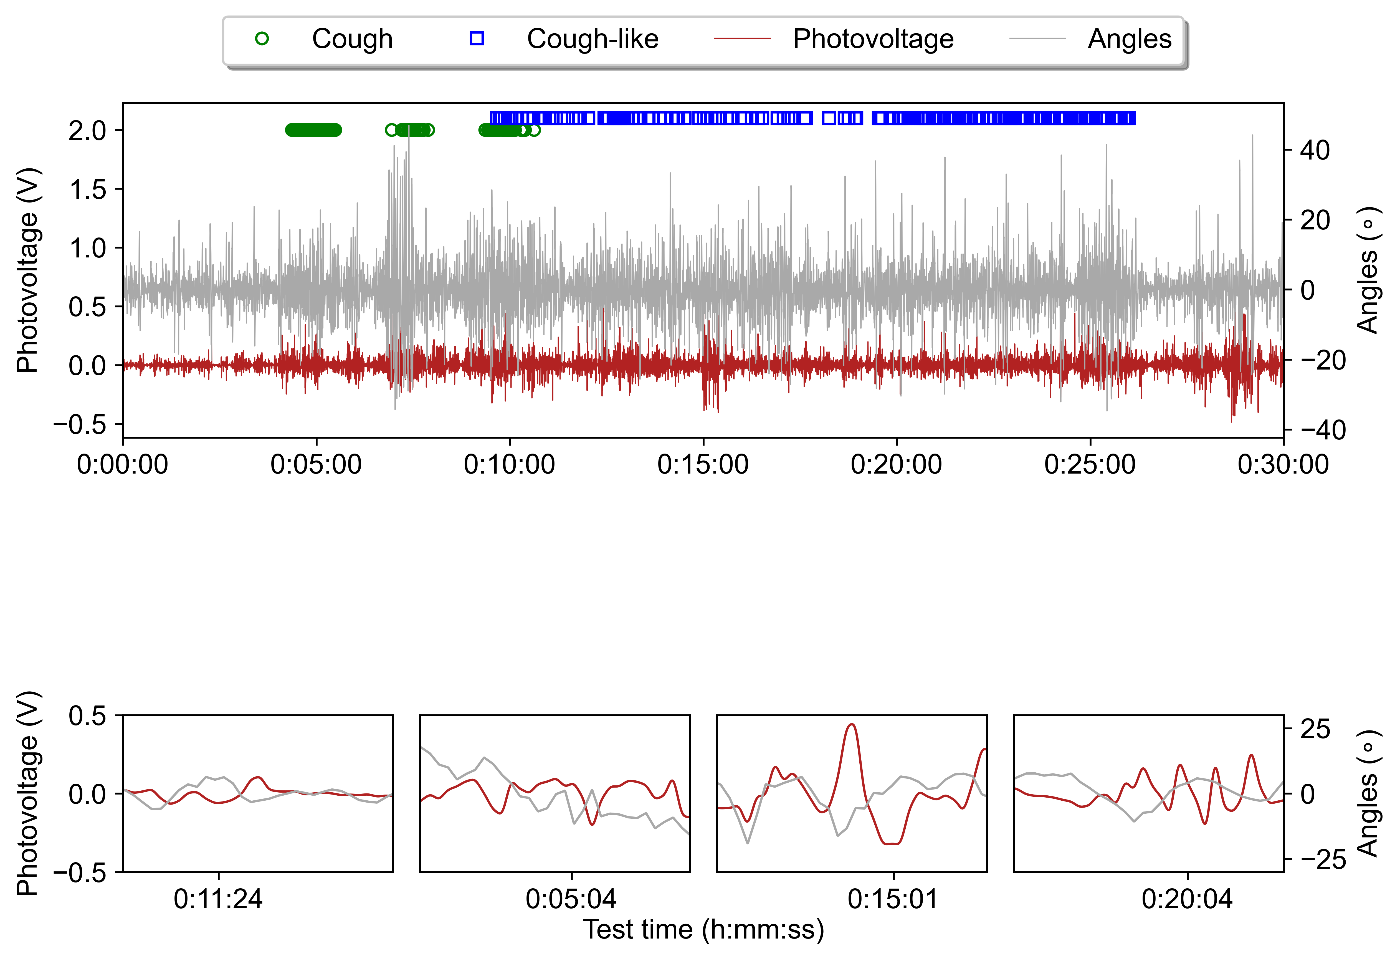
results/fig6/basketball_long_test.png
