BailabUNC/LaHMo/results/fig6/confusion_matrix.png

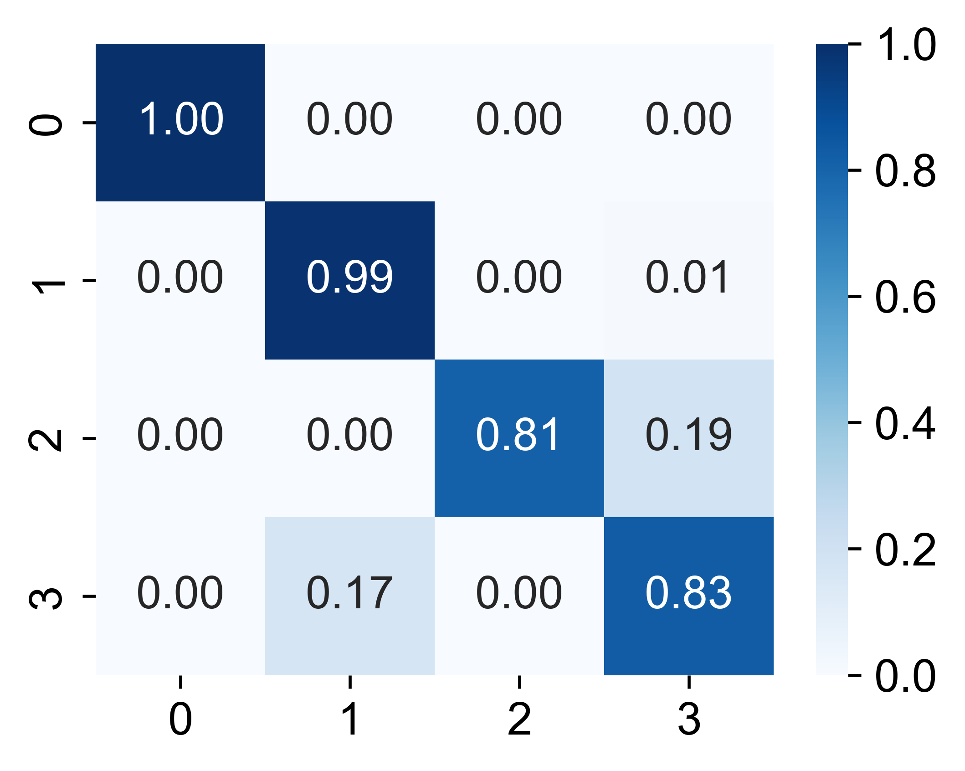
results/fig6/confusion_matrix.png
