BailabUNC/LaHMo/results/fig6/Exercise Intensity indicator.png

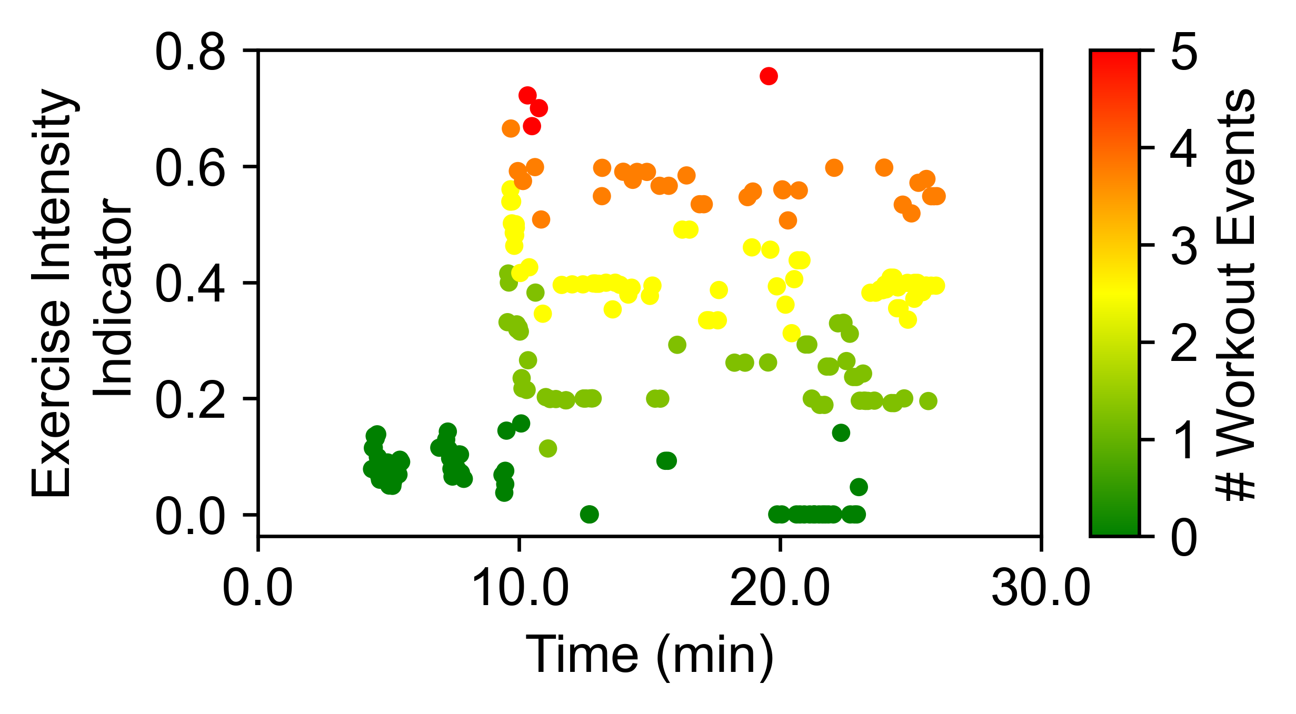
results/fig6/Exercise Intensity indicator.png
