BailabUNC/LaHMo/results/fig6/long_test_result.png

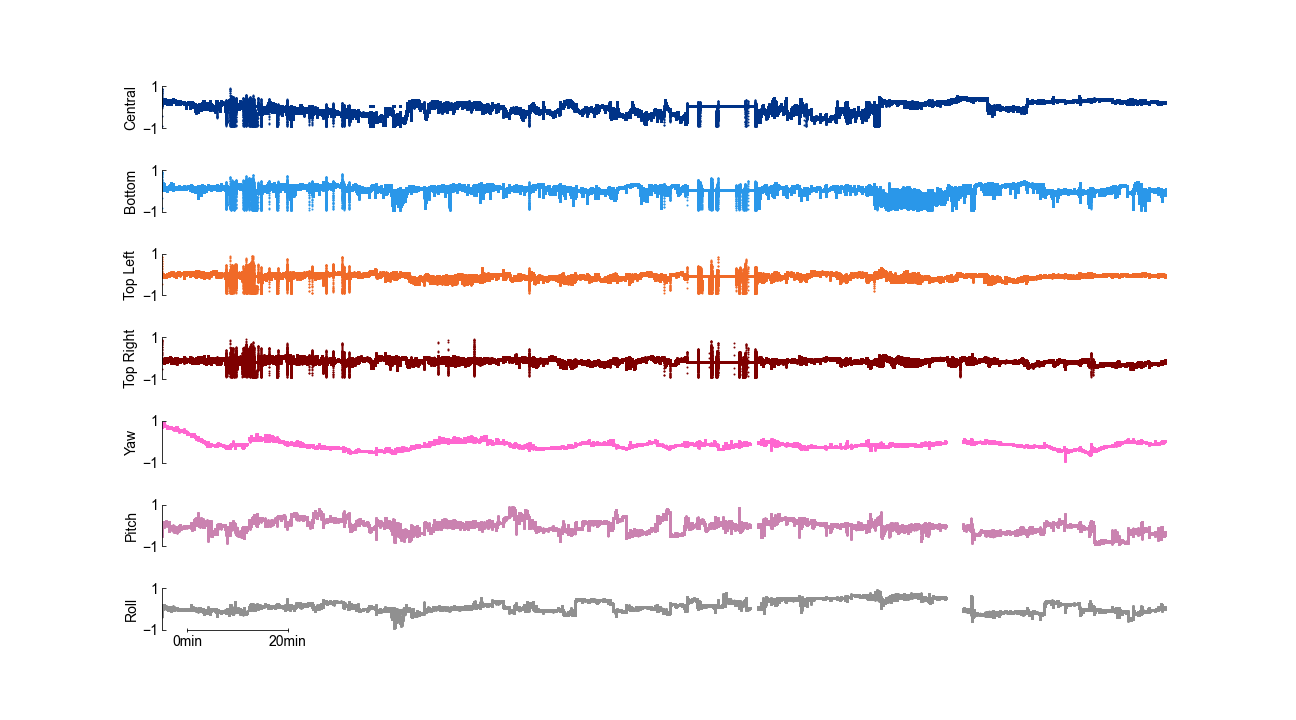
results/fig6/long_test_result.png
