BailabUNC/LaHMo/results/fig6/respiratory health indicator.png

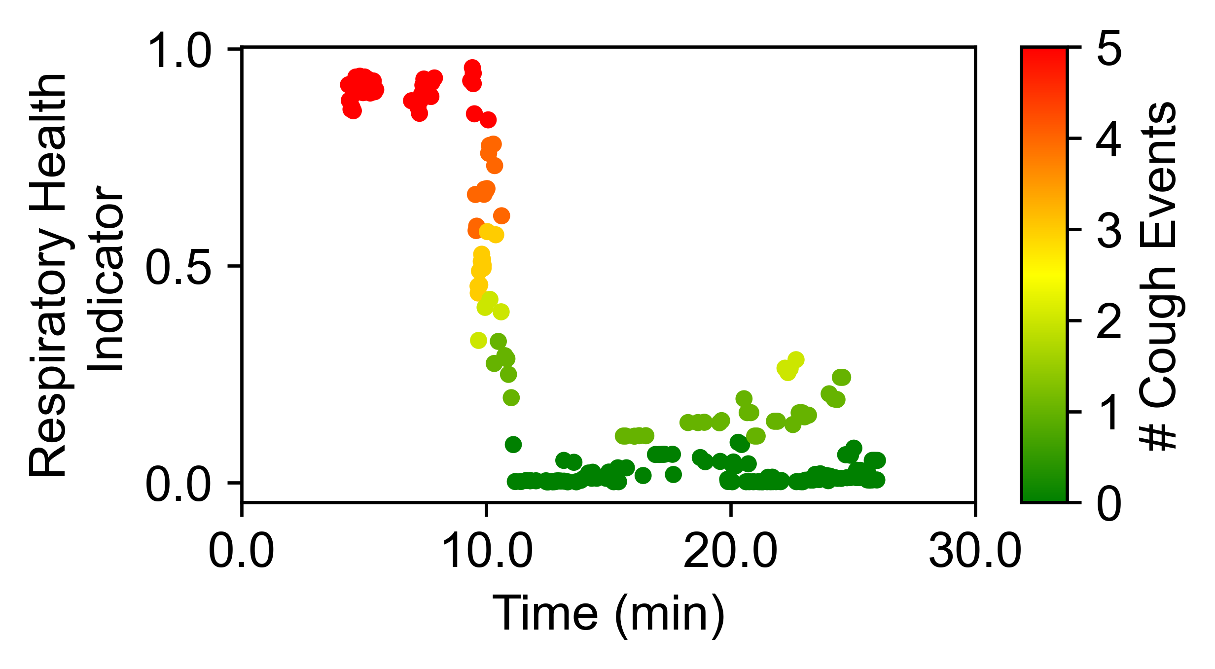
results/fig6/respiratory health indicator.png
