BailabUNC/LaHMo/results/fig6/result_9140_to_9150.png

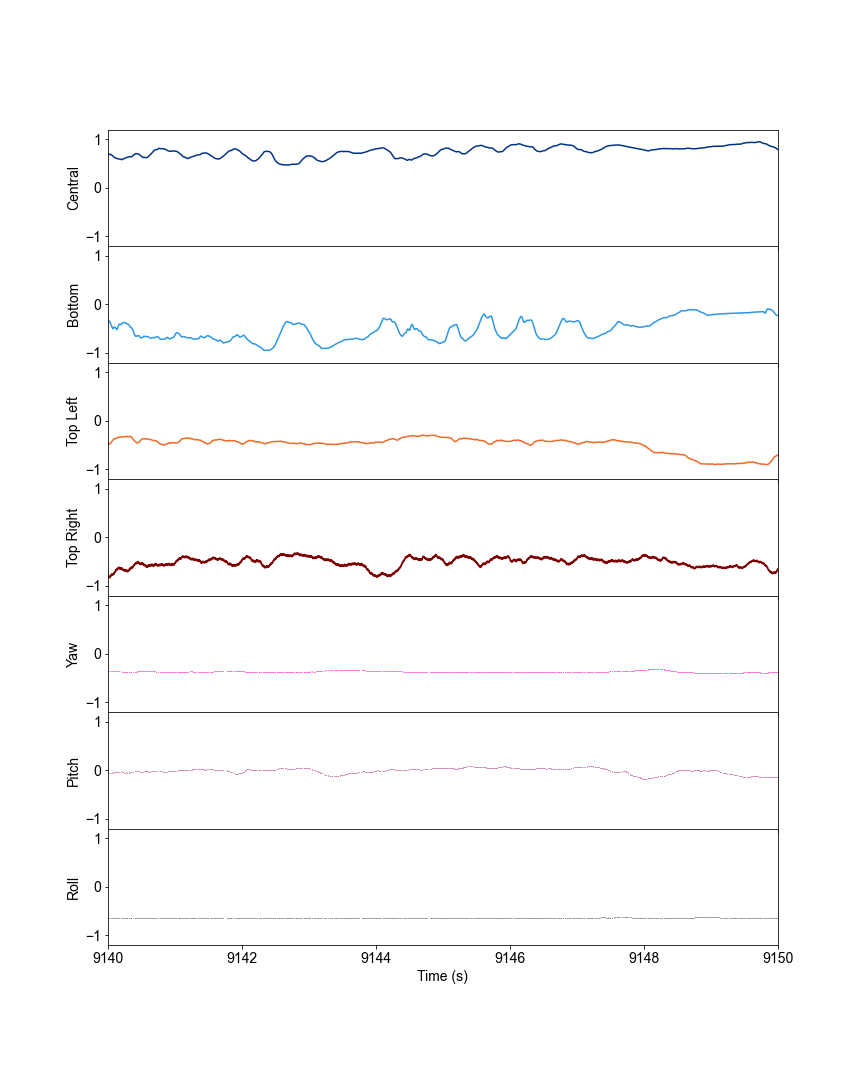
results/fig6/result_9140_to_9150.png
