BailabUNC/LaHMo/results/fig6/scores_time.png

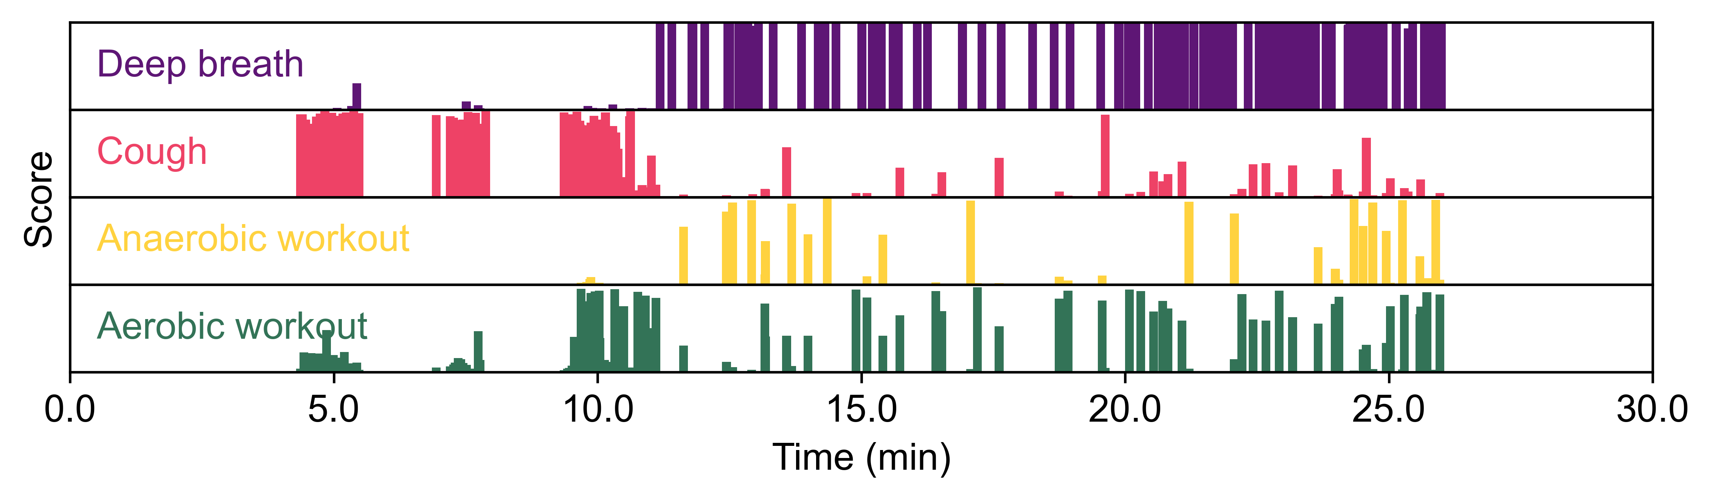
results/fig6/scores_time.png
