BailabUNC/LaHMo/results/fig6/selected_segments.png

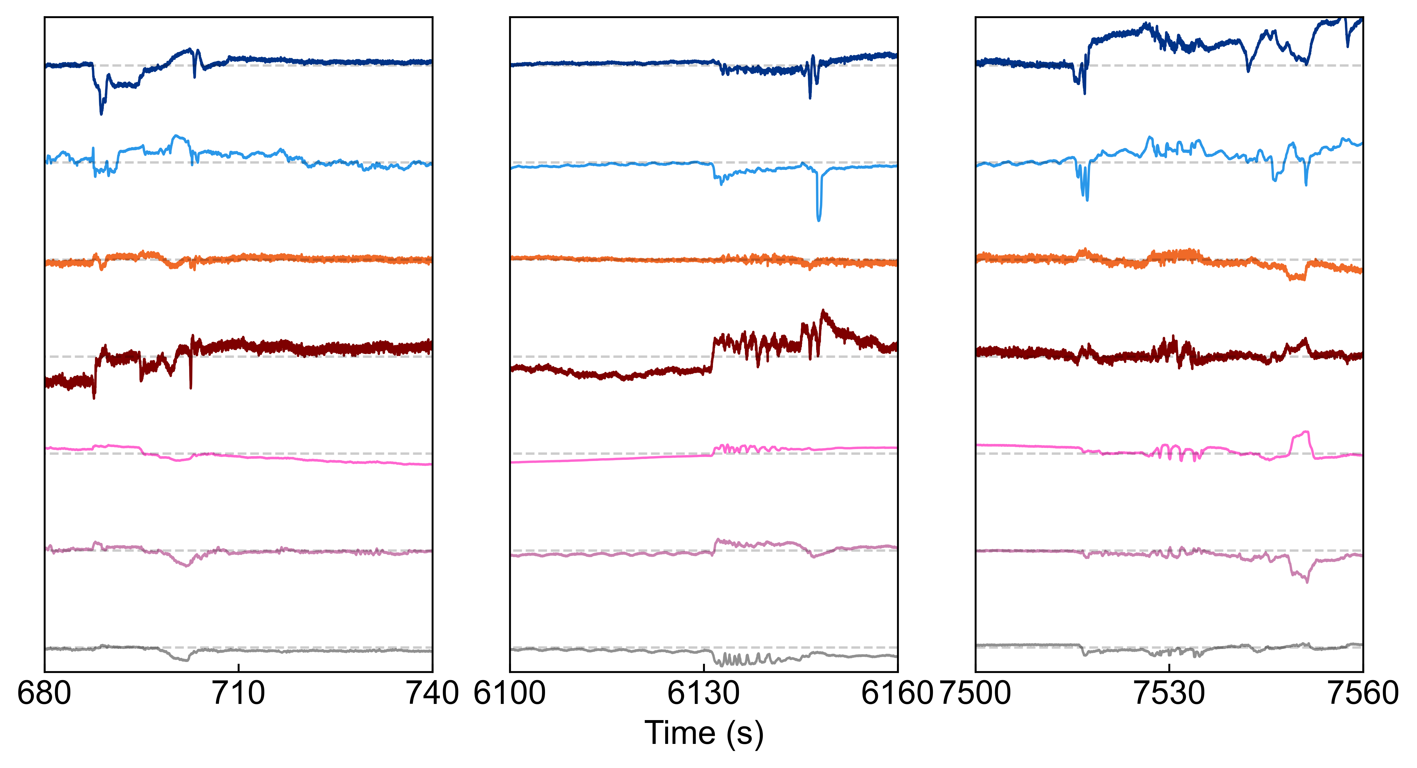
results/fig6/selected_segments.png
