BailabUNC/LaHMo/results/fig6/time_related_score.png

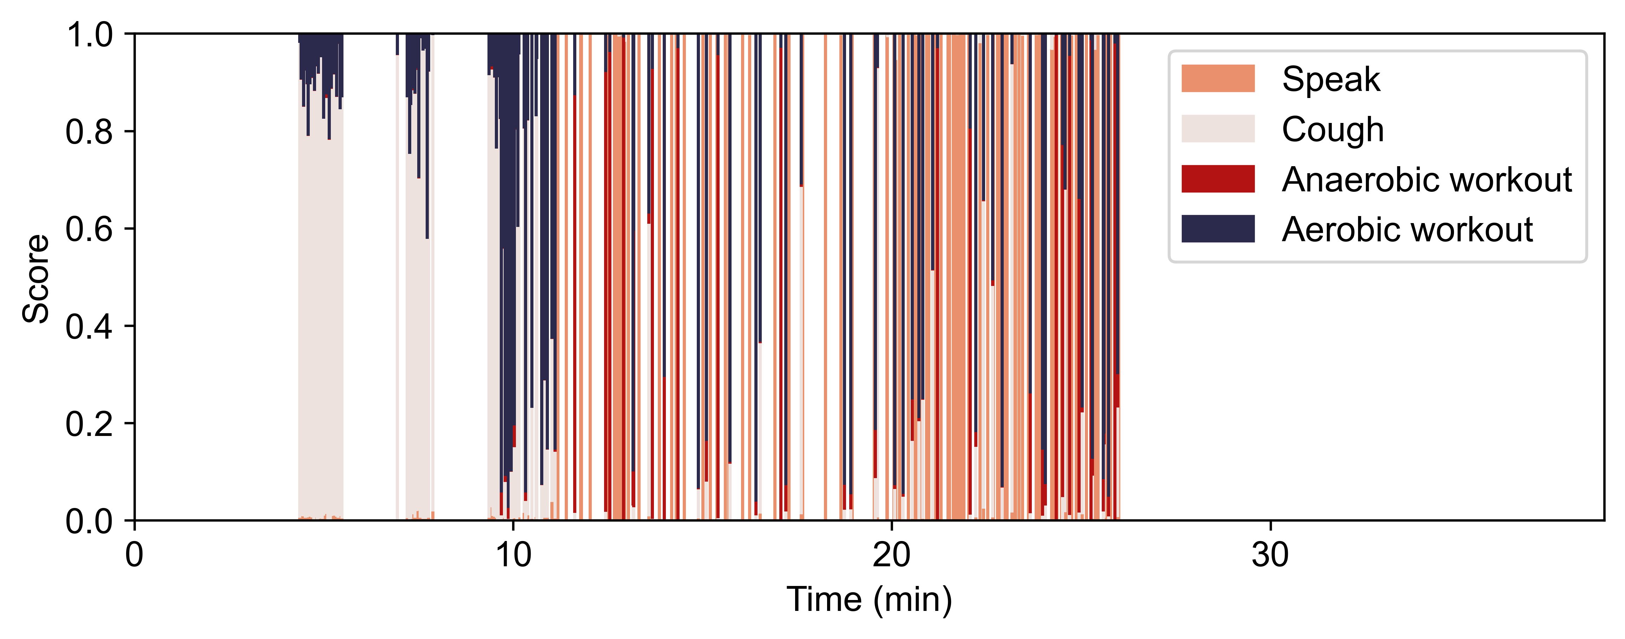
results/fig6/time_related_score.png
