BailabUNC/LaHMo/results/fig6/training_curve.png

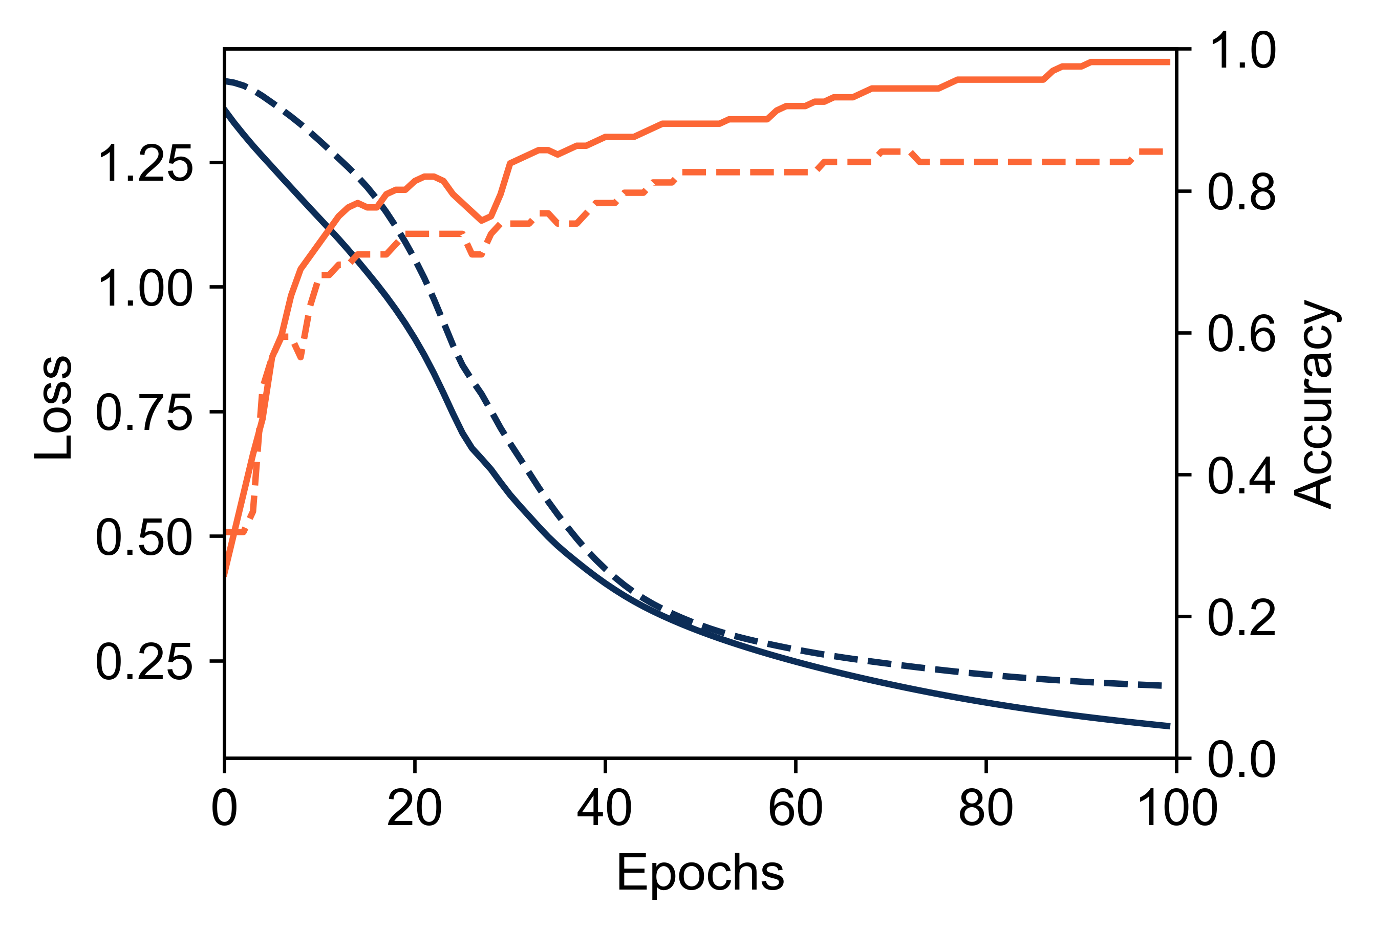
results/fig6/training_curve.png
