BailabUNC/LaHMo/results/revision/new tests/anti-motion/motion.png

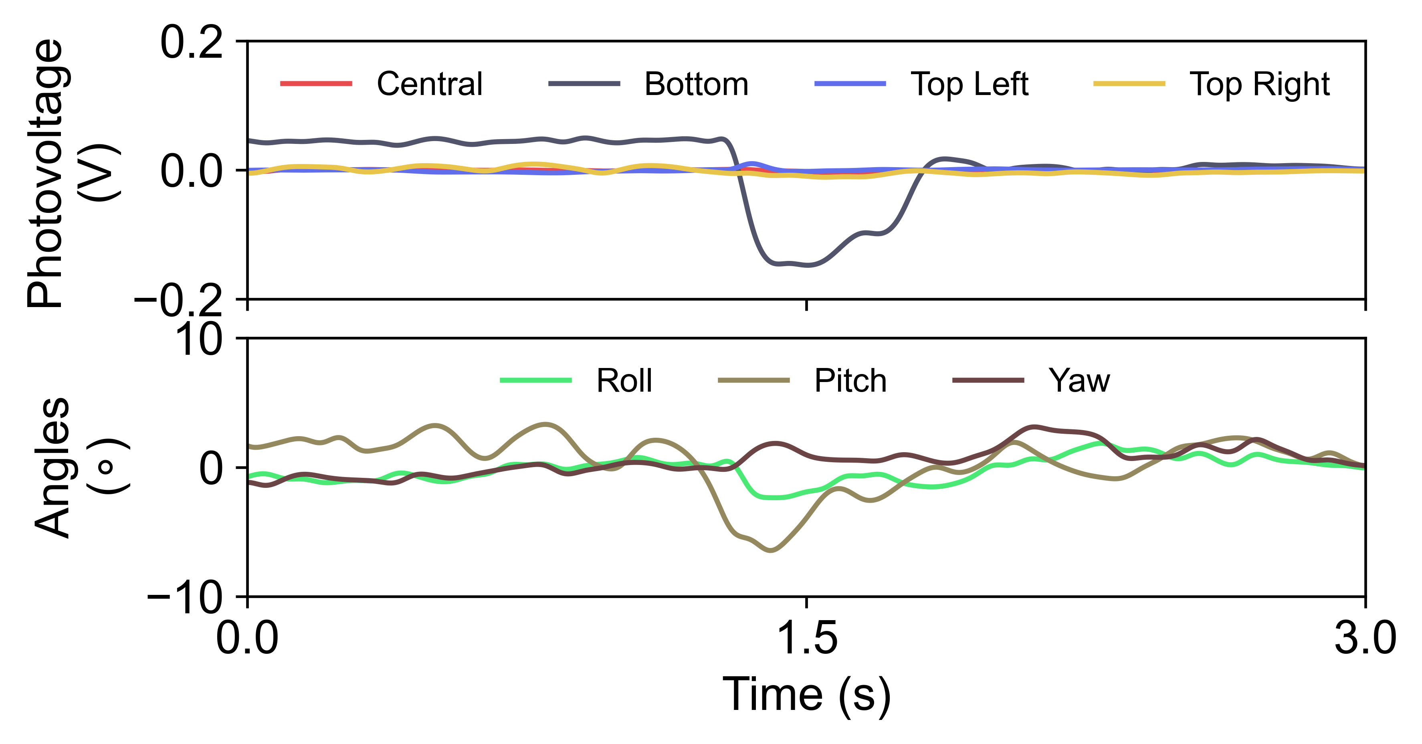
results/revision/new tests/anti-motion/motion.png
