BailabUNC/LaHMo/results/revision/new tests/anti-motion/stable.png

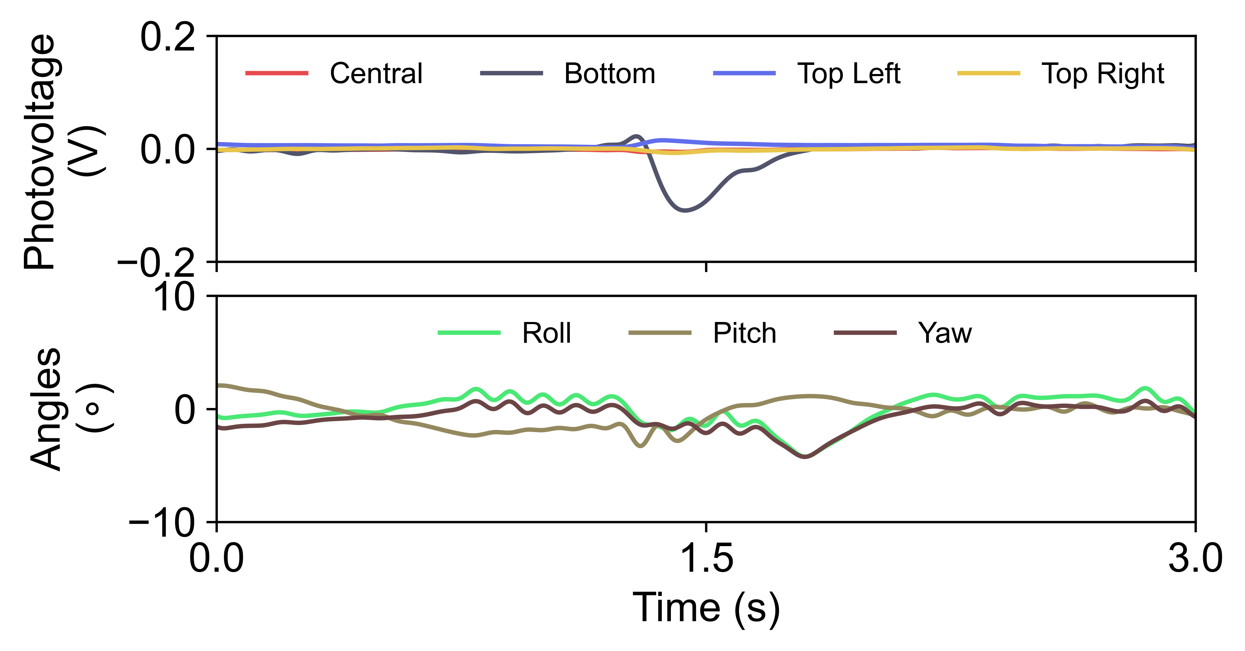
results/revision/new tests/anti-motion/stable.png
