BailabUNC/LaHMo/results/revision/new tests/bolus type/lvl3.png

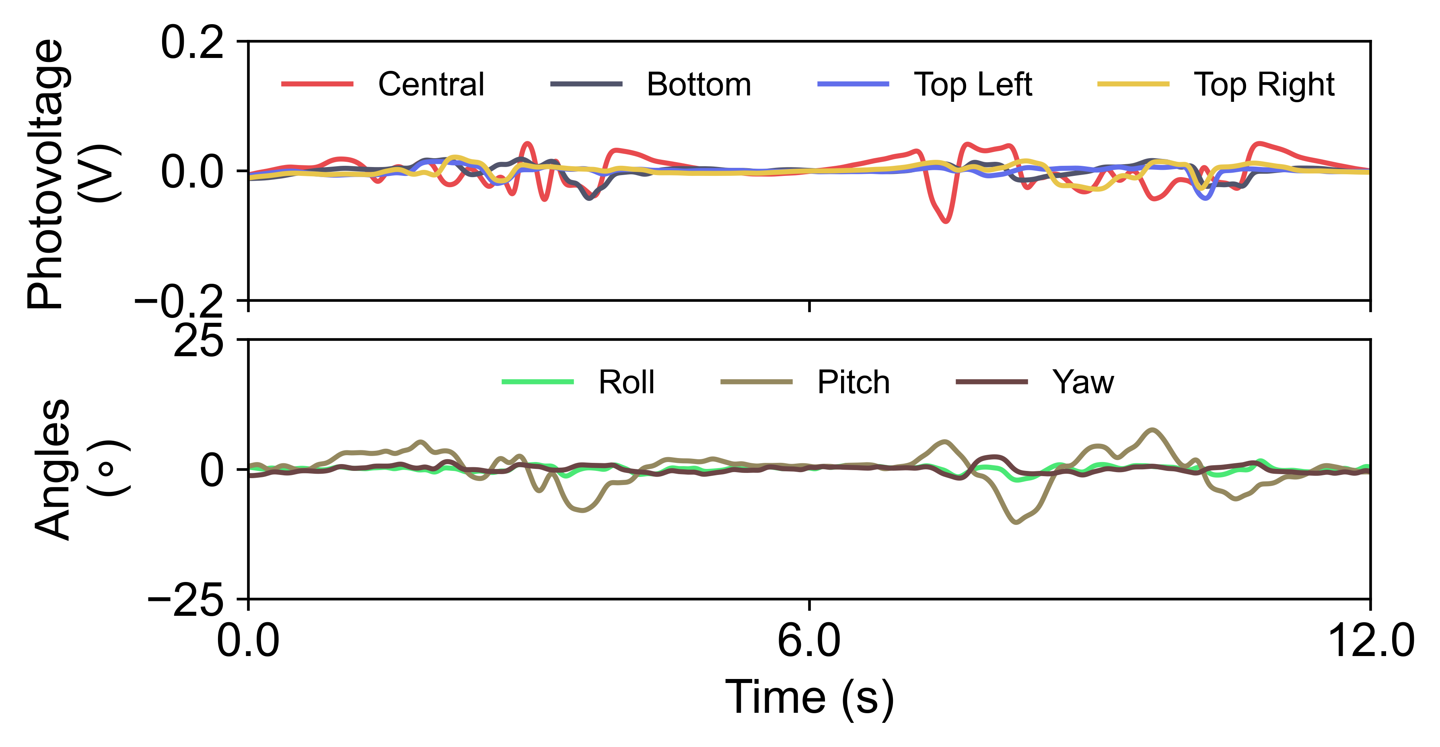
results/revision/new tests/bolus type/lvl3.png
