BailabUNC/LaHMo/results/revision/new tests/bolus type/lvl4.png

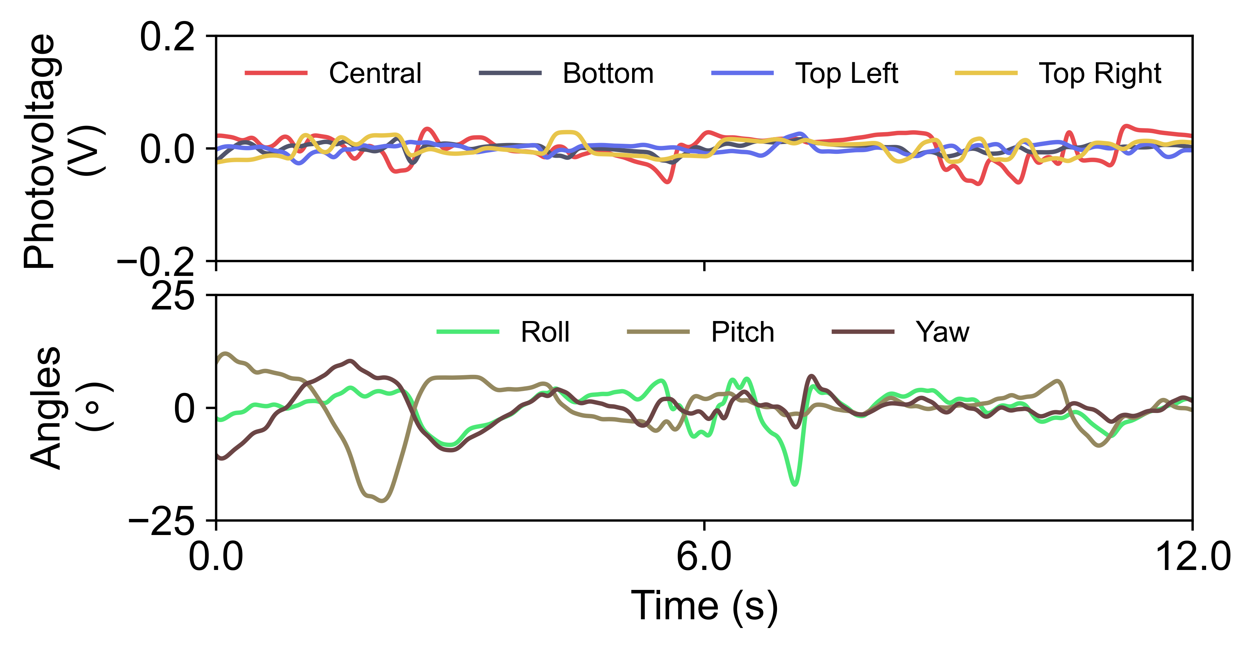
results/revision/new tests/bolus type/lvl4.png
