BailabUNC/LaHMo/results/revision/new tests/bolus type/lvl5.png

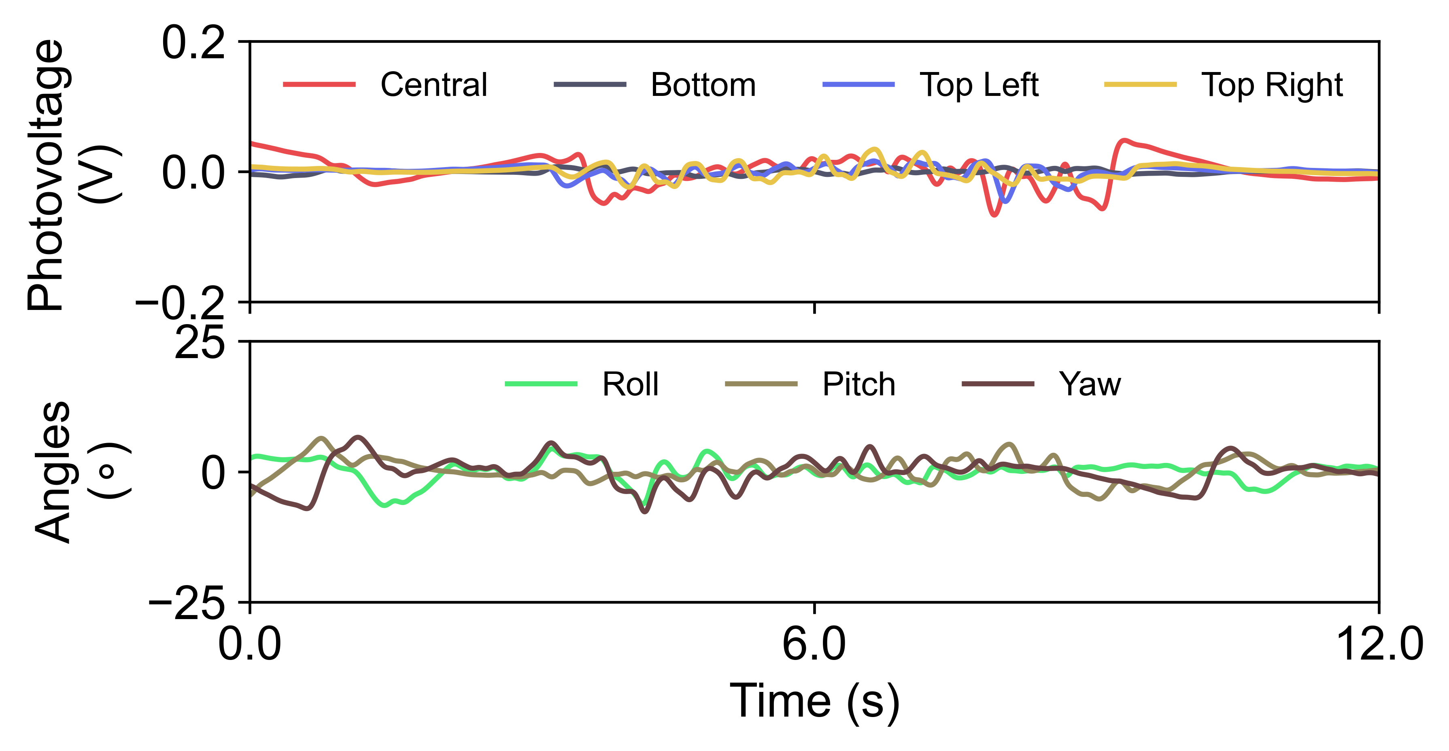
results/revision/new tests/bolus type/lvl5.png
