BailabUNC/LaHMo/results/revision/new tests/bolus type/lvl6.png

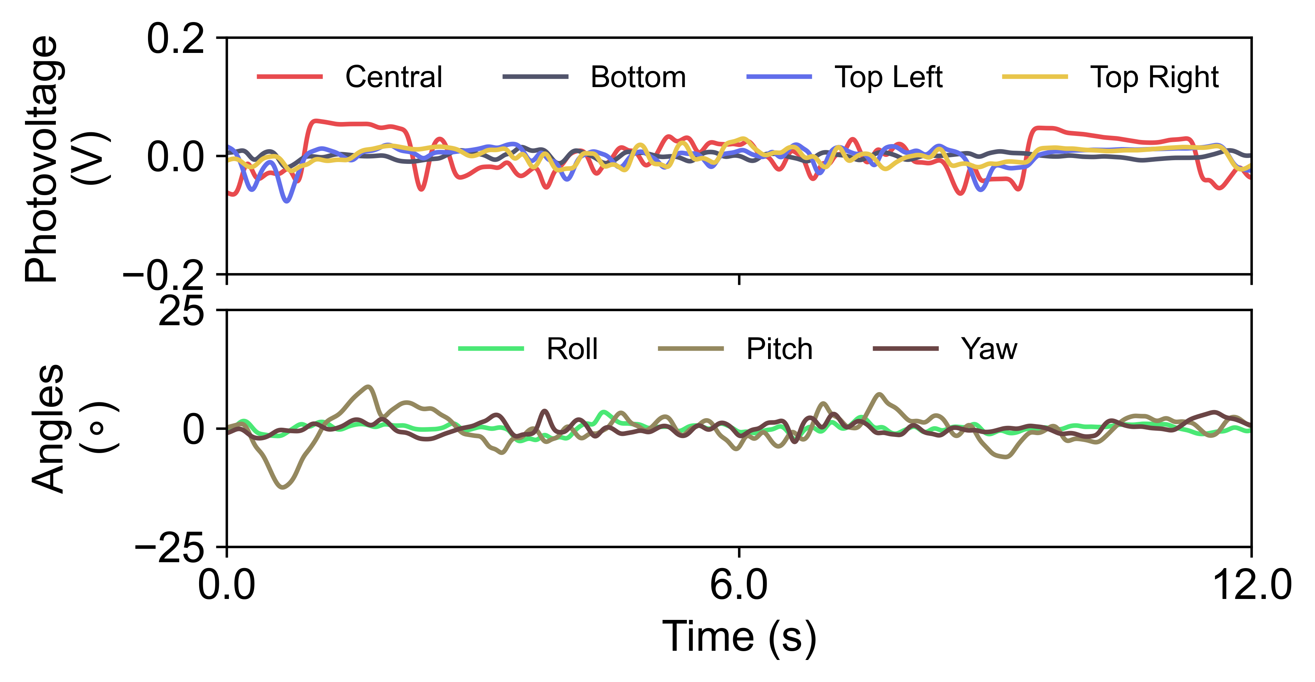
results/revision/new tests/bolus type/lvl6.png
