BailabUNC/LaHMo/results/revision/new tests/bolus type/lvl7.png

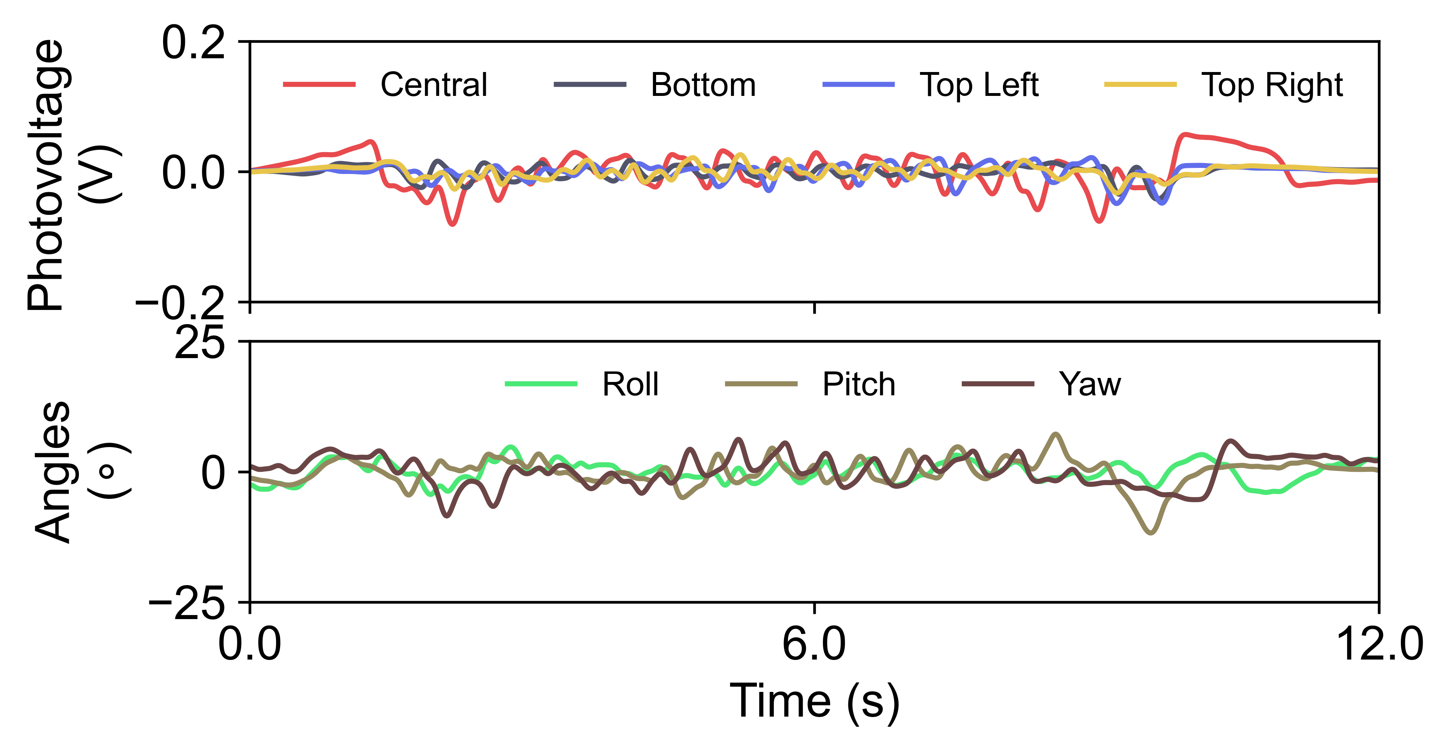
results/revision/new tests/bolus type/lvl7.png
