BailabUNC/LaHMo/results/revision/new tests/breathing/nasal.png

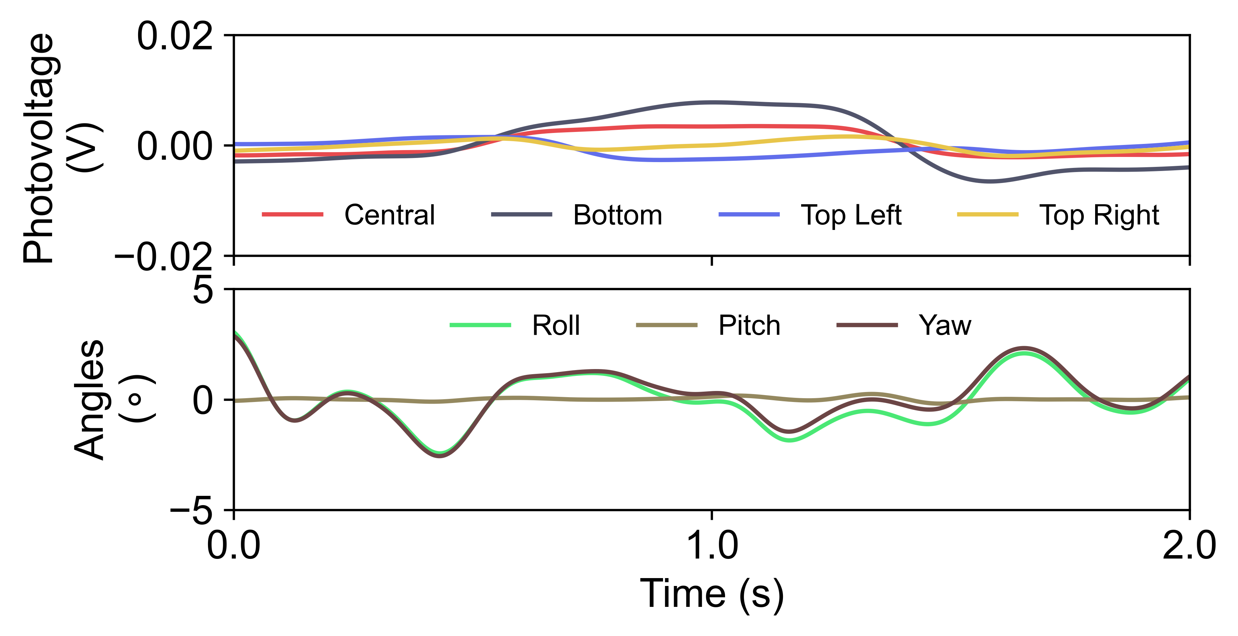
results/revision/new tests/breathing/nasal.png
