BailabUNC/LaHMo/results/revision/new tests/breathing/oral.png

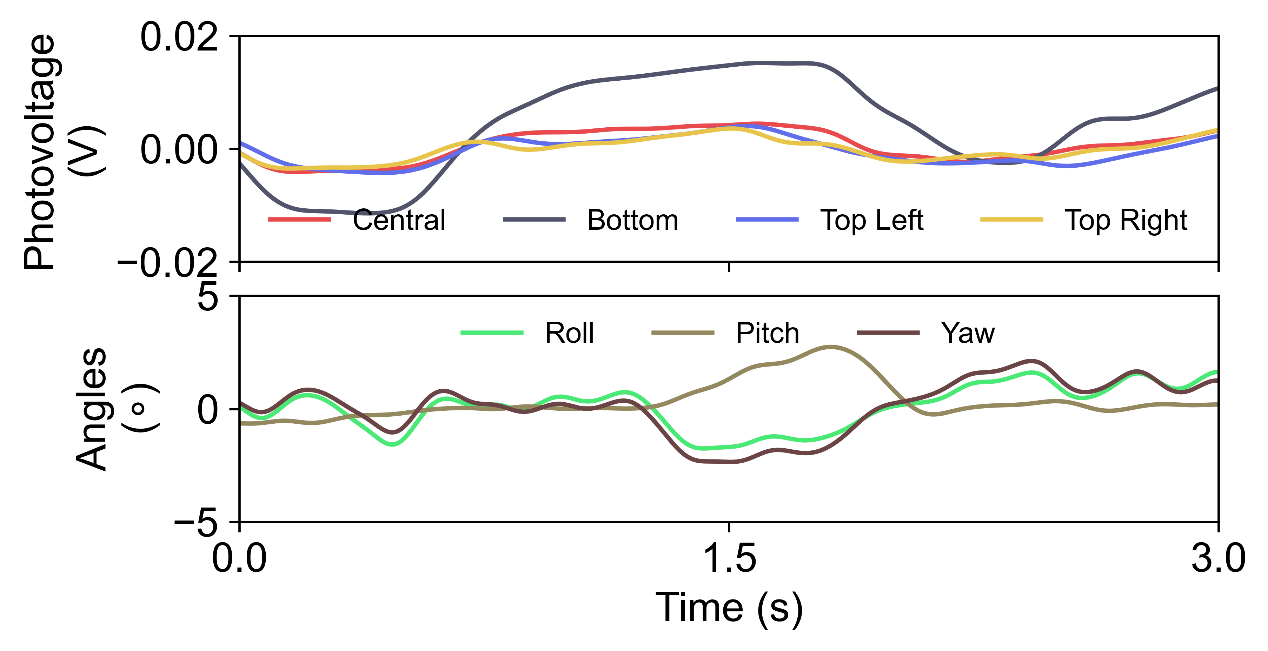
results/revision/new tests/breathing/oral.png
