BailabUNC/LaHMo/results/revision/new tests/quality/c3.png

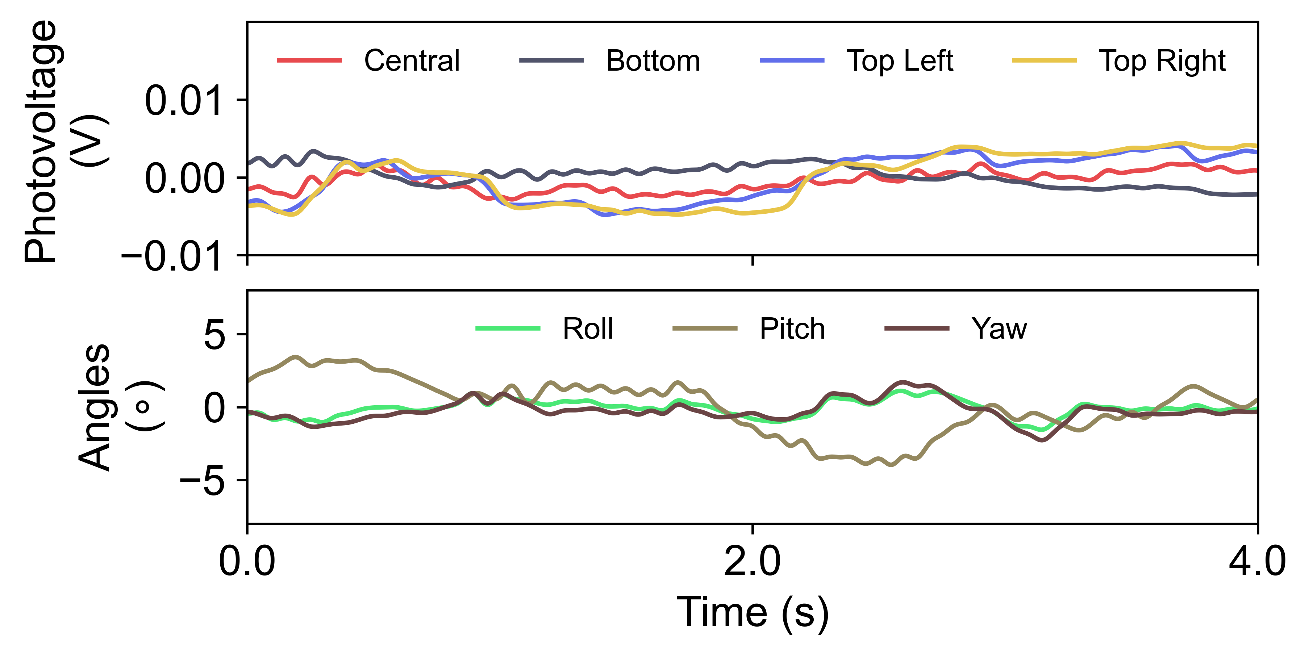
results/revision/new tests/quality/c3.png
