BailabUNC/LaHMo/results/revision/new tests/quality/falsetto.png

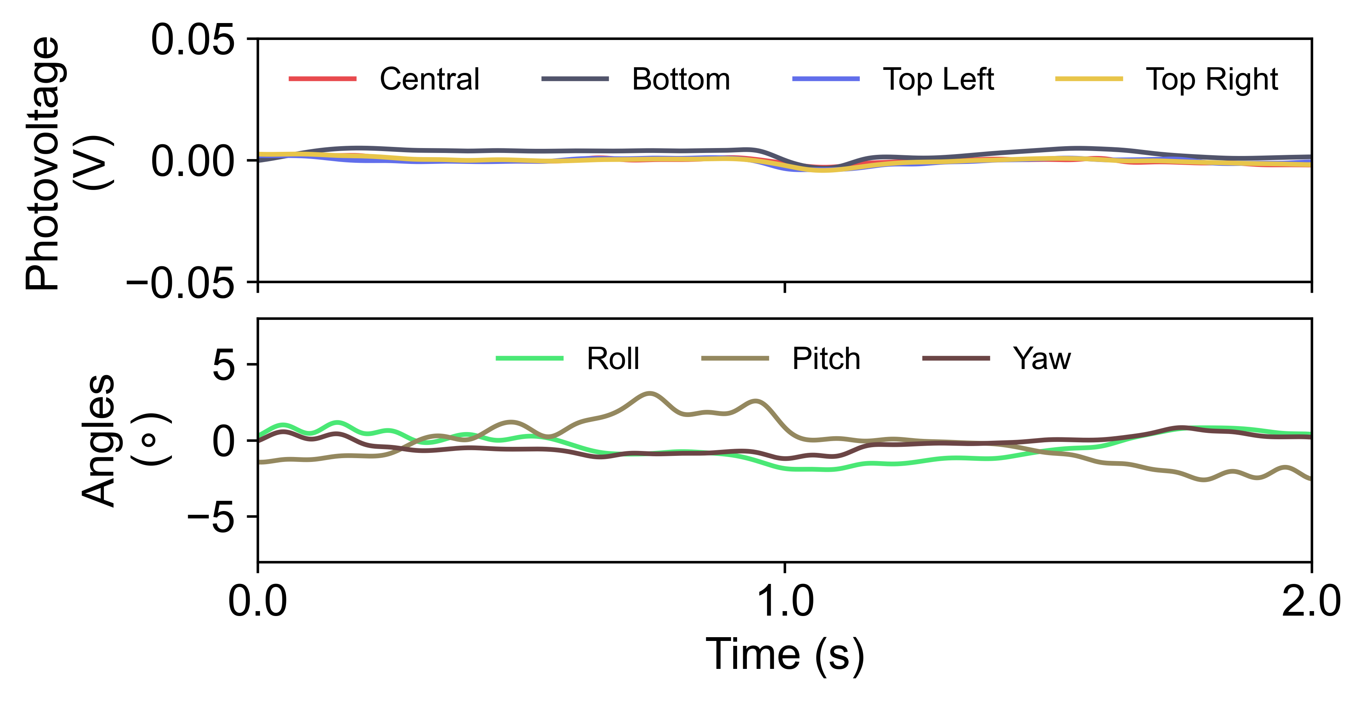
results/revision/new tests/quality/falsetto.png
