BailabUNC/LaHMo/results/revision/new tests/quality/g3.png

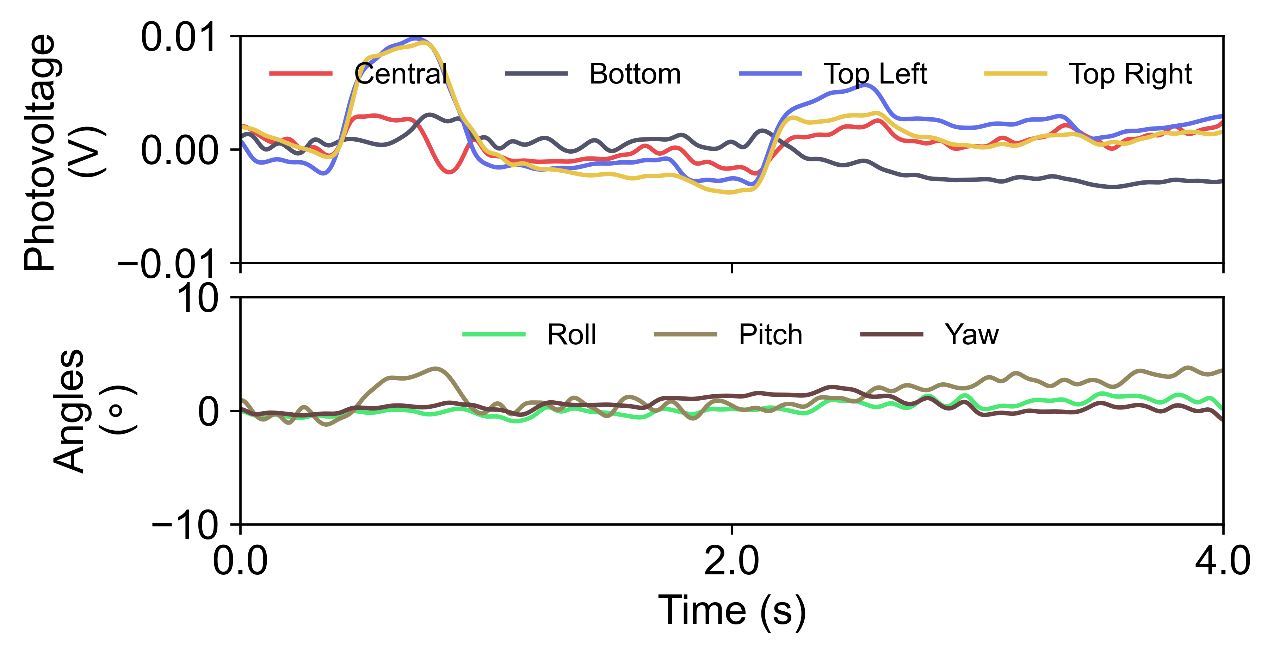
results/revision/new tests/quality/g3.png
