BailabUNC/LaHMo/results/revision/new tests/quality/g4.png

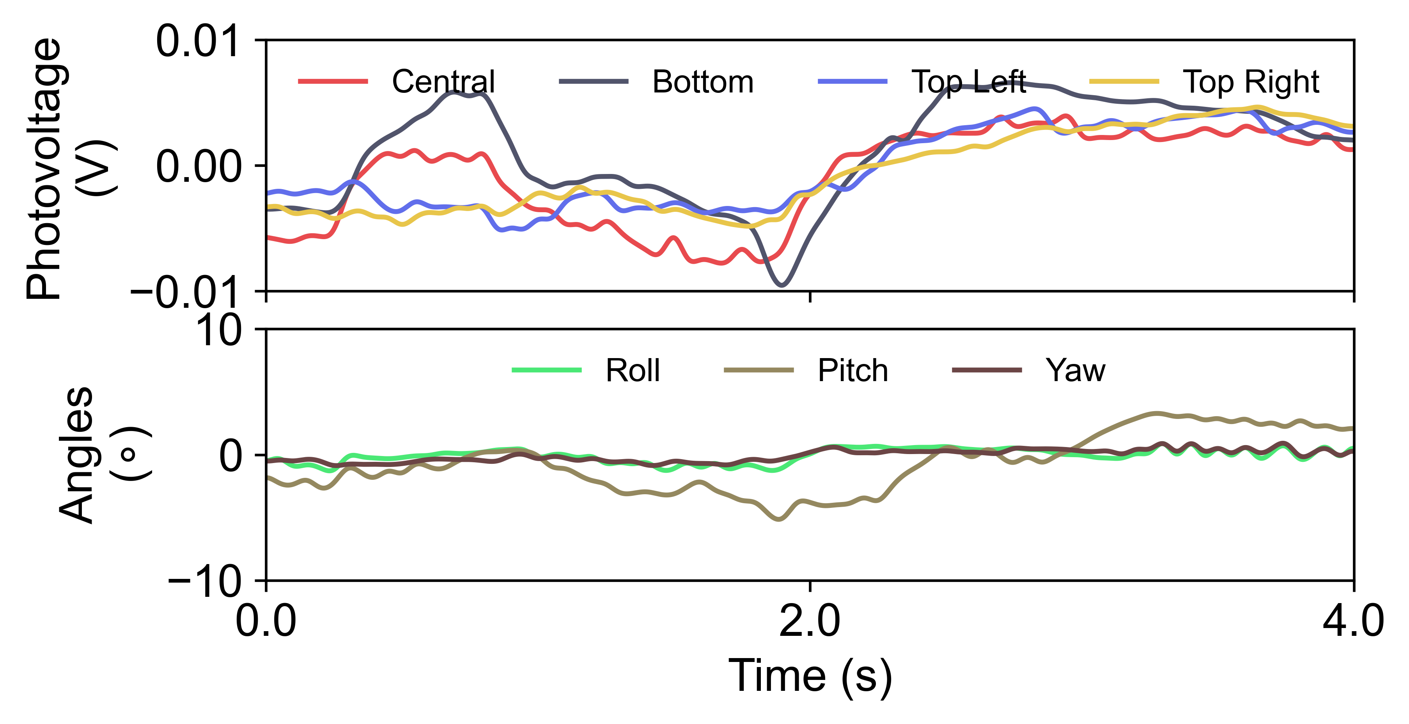
results/revision/new tests/quality/g4.png
