BailabUNC/LaHMo/results/revision/new tests/quality/head_voice.png

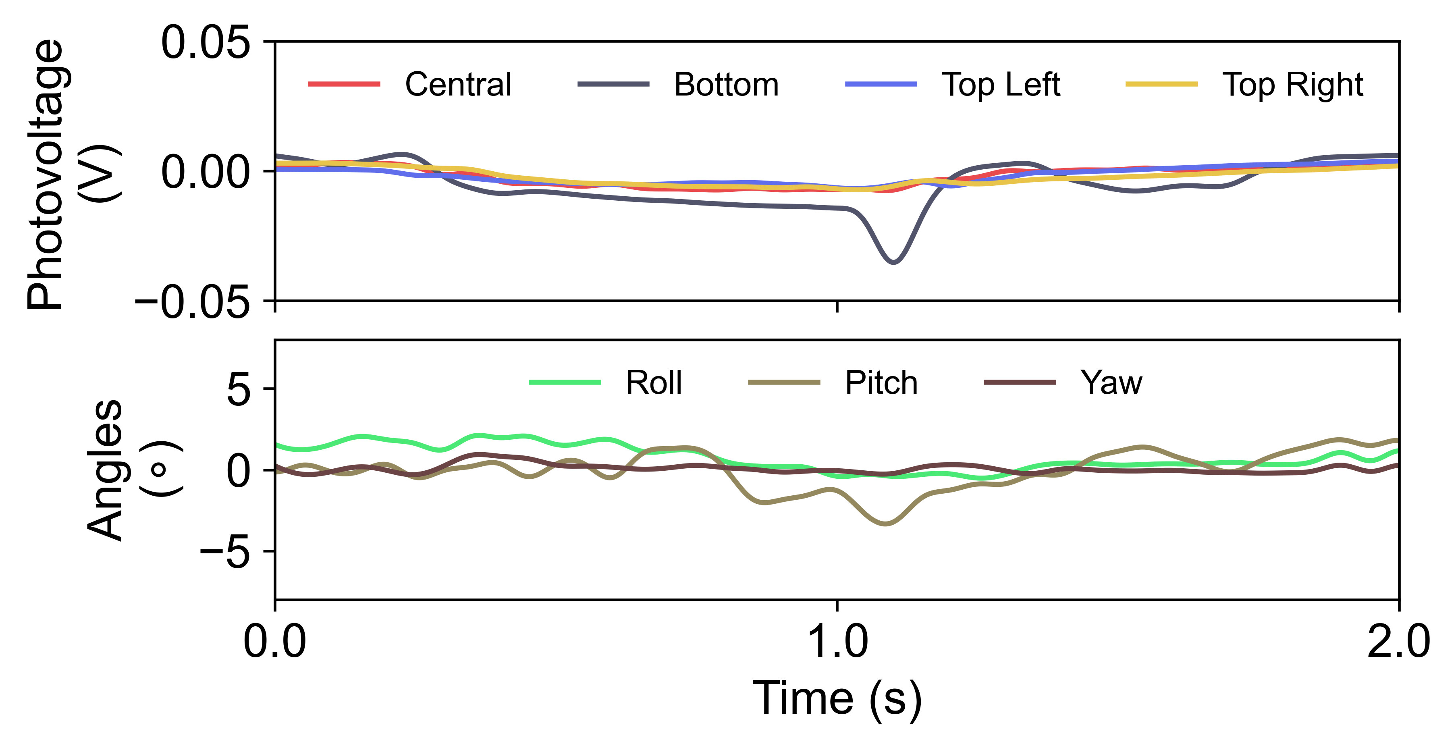
results/revision/new tests/quality/head_voice.png
