BailabUNC/LaHMo/results/revision/new tests/quality/loud.png

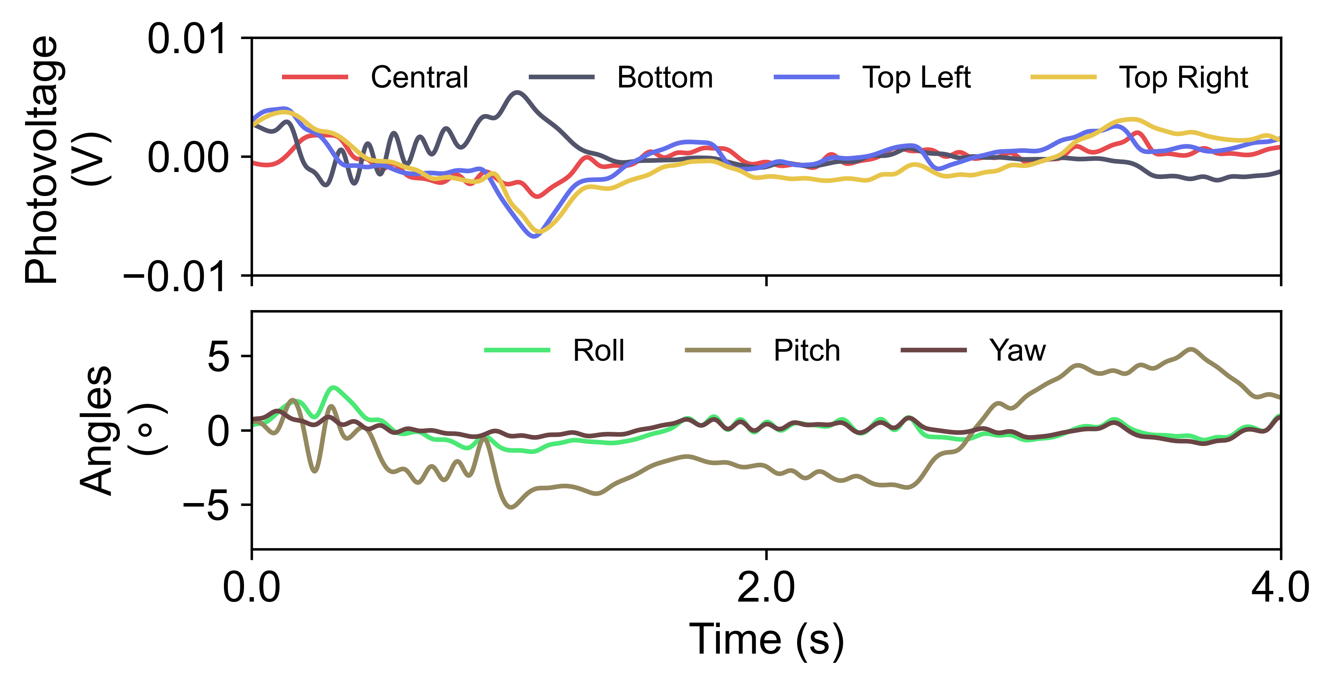
results/revision/new tests/quality/loud.png
