BailabUNC/LaHMo/results/revision/new tests/quality/whisper.png

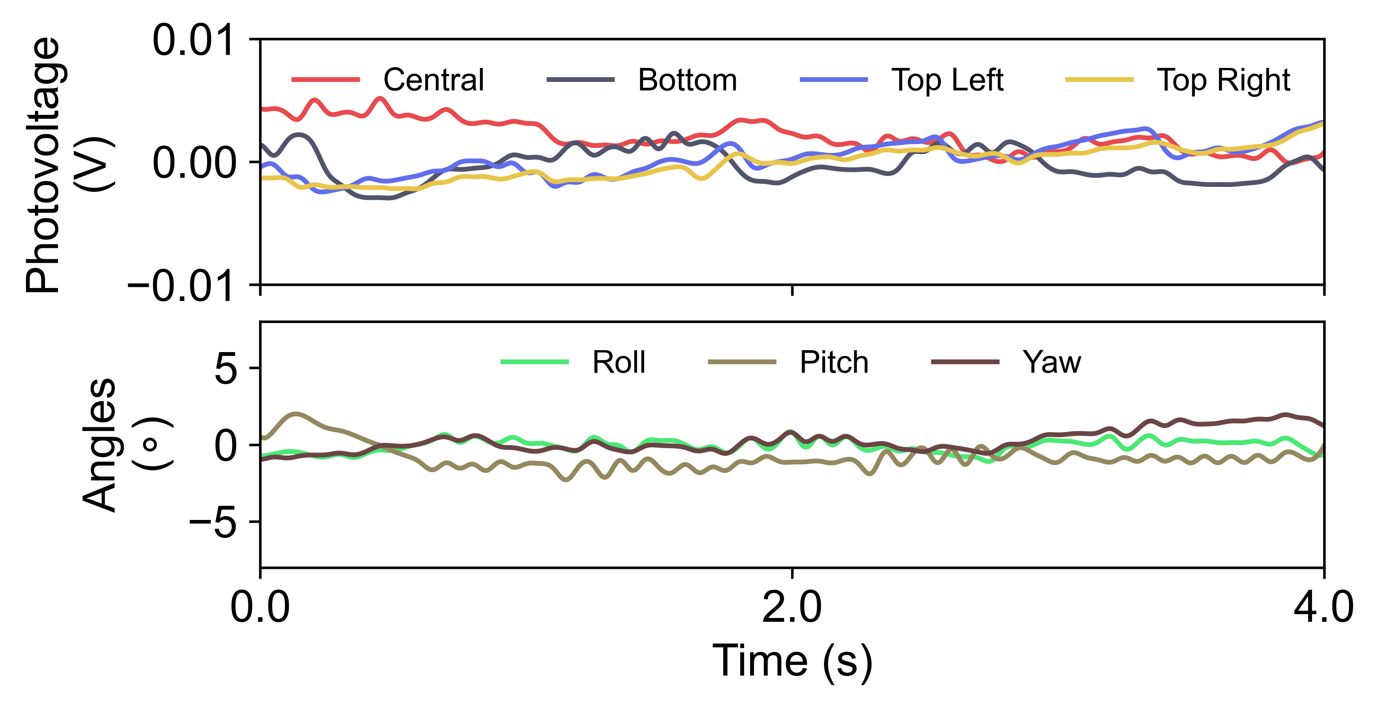
results/revision/new tests/quality/whisper.png
