BailabUNC/LaHMo/results/revision/new tests/video/chest/1.jpg

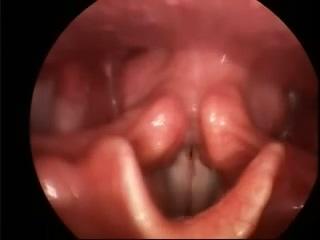
results/revision/new tests/video/chest/1.jpg
