BailabUNC/LaHMo/results/revision/new tests/video/chest/1a.jpg

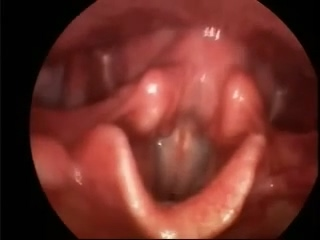
results/revision/new tests/video/chest/1a.jpg
