BailabUNC/LaHMo/results/revision/new tests/video/chest/3.jpg

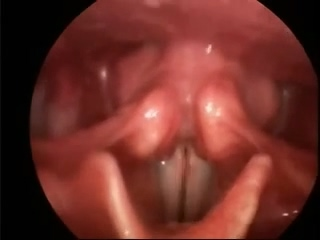
results/revision/new tests/video/chest/3.jpg
