BailabUNC/LaHMo/results/revision/new tests/video/chest/4.jpg

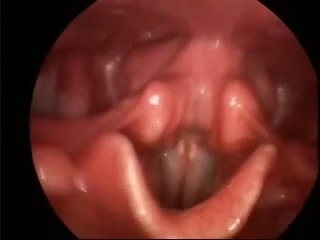
results/revision/new tests/video/chest/4.jpg
