BailabUNC/LaHMo/results/revision/new tests/video/falsetto/1.jpg

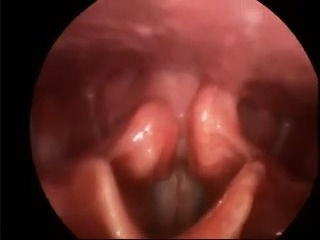
results/revision/new tests/video/falsetto/1.jpg
