BailabUNC/LaHMo/results/revision/new tests/video/falsetto/1a.jpg

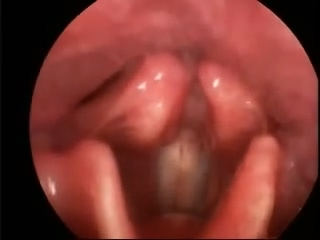
results/revision/new tests/video/falsetto/1a.jpg
