BailabUNC/LaHMo/results/revision/new tests/video/falsetto/2.jpg

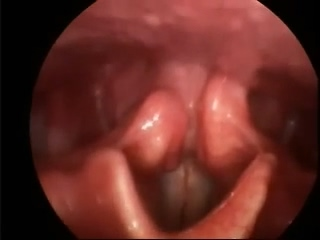
results/revision/new tests/video/falsetto/2.jpg
