BailabUNC/LaHMo/results/revision/new tests/video/falsetto/3.jpg

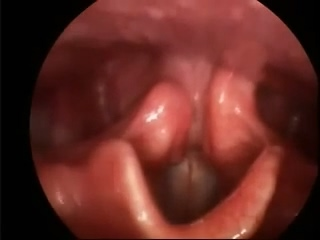
results/revision/new tests/video/falsetto/3.jpg
