BailabUNC/LaHMo/results/revision/new tests/video/falsetto/4.jpg

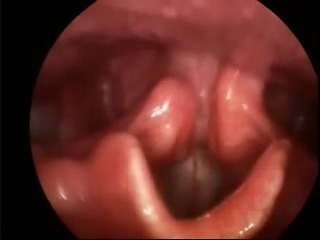
results/revision/new tests/video/falsetto/4.jpg
