BailabUNC/LaHMo/results/revision/new tests/video/falsetto/6.jpg

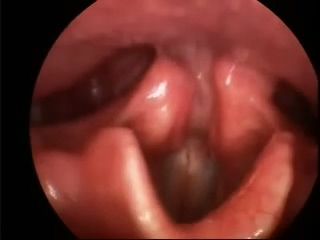
results/revision/new tests/video/falsetto/6.jpg
