BailabUNC/LaHMo/results/revision/new tests/video/falsetto/7.jpg

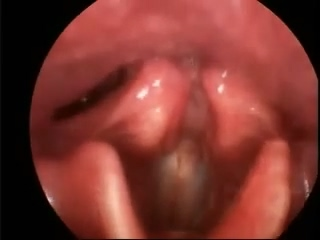
results/revision/new tests/video/falsetto/7.jpg
