BailabUNC/LaHMo/results/revision/photo/DSC_0415.JPG

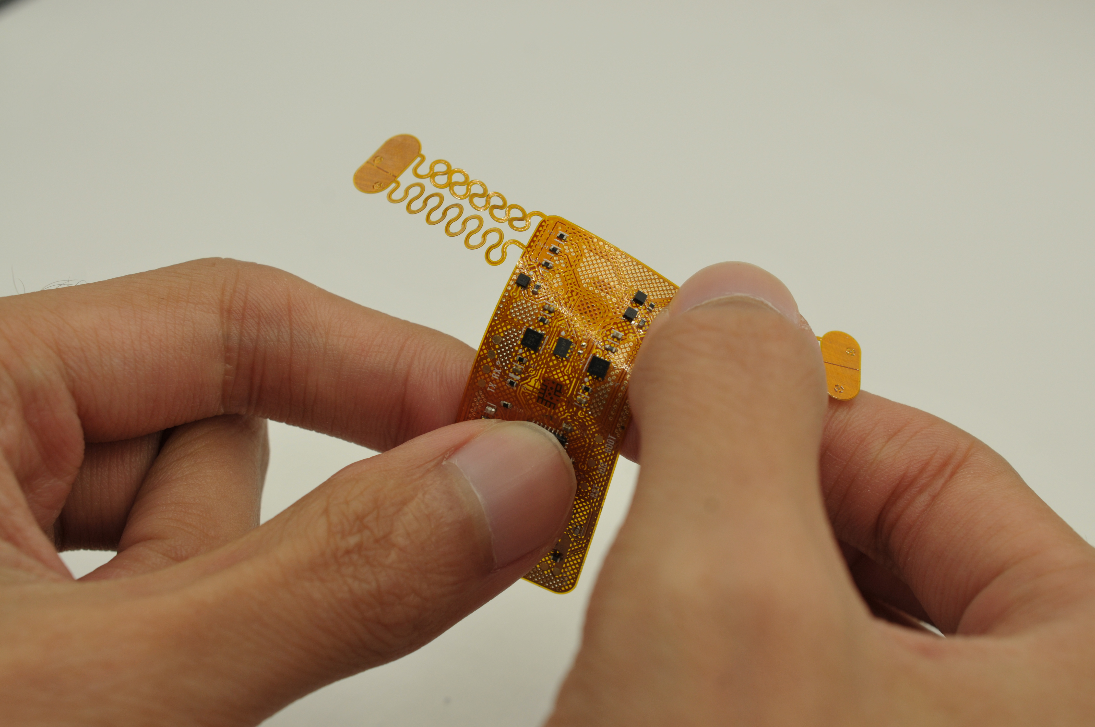
results/revision/photo/DSC_0415.JPG
