BailabUNC/LaHMo/results/revision/photo/DSC_0416.JPG

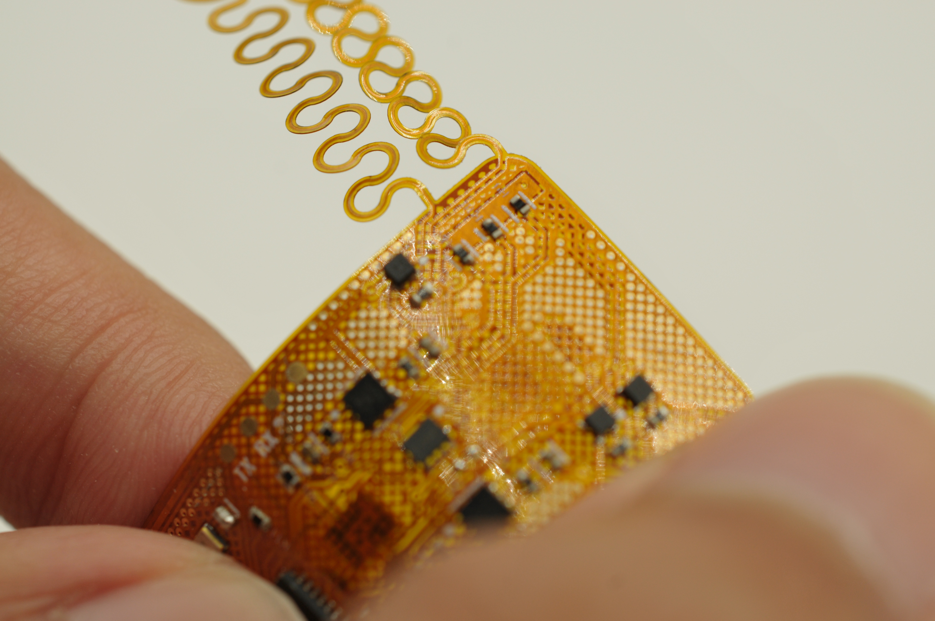
results/revision/photo/DSC_0416.JPG
