BailabUNC/LaHMo/results/revision/photo/DSC_0420.JPG

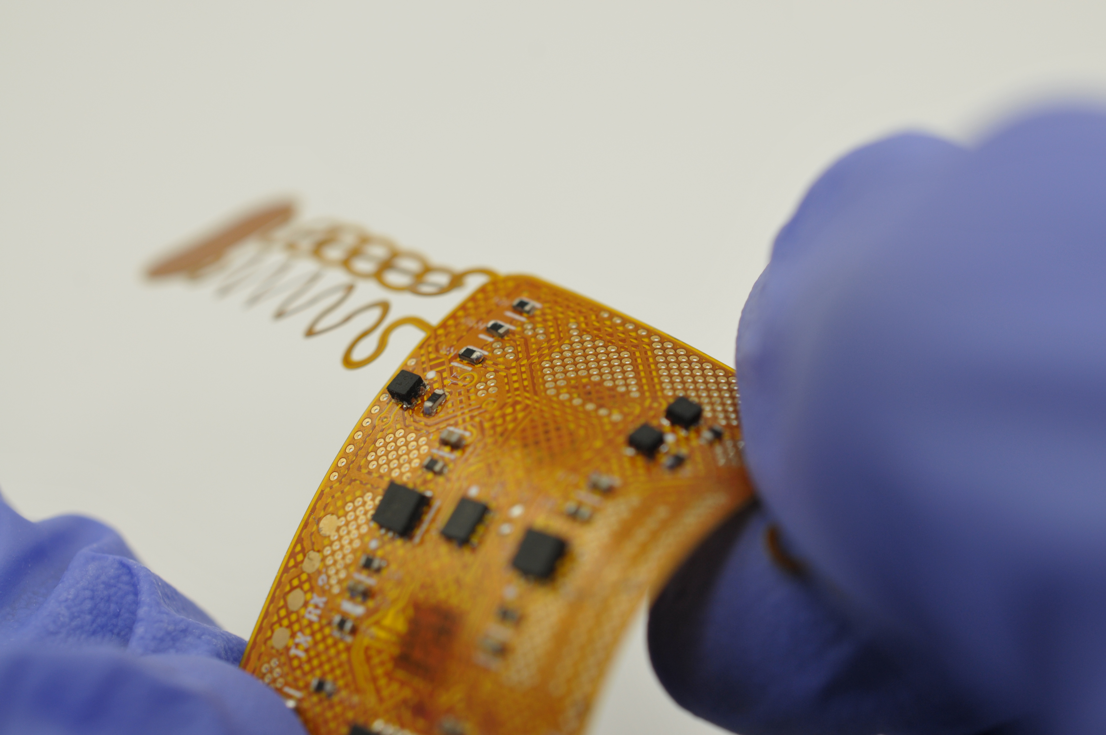
results/revision/photo/DSC_0420.JPG
