BailabUNC/LaHMo/results/revision/photo/DSC_0421.JPG

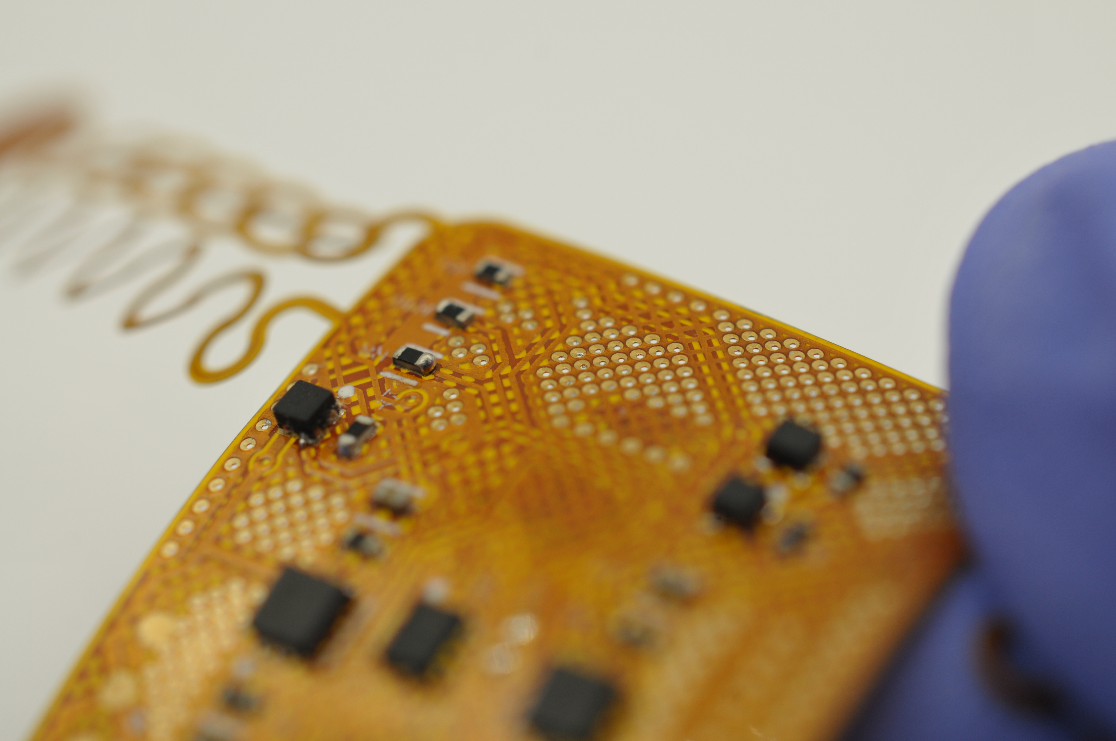
results/revision/photo/DSC_0421.JPG
