BailabUNC/LaHMo/results/revision/photo/DSC_0422.JPG

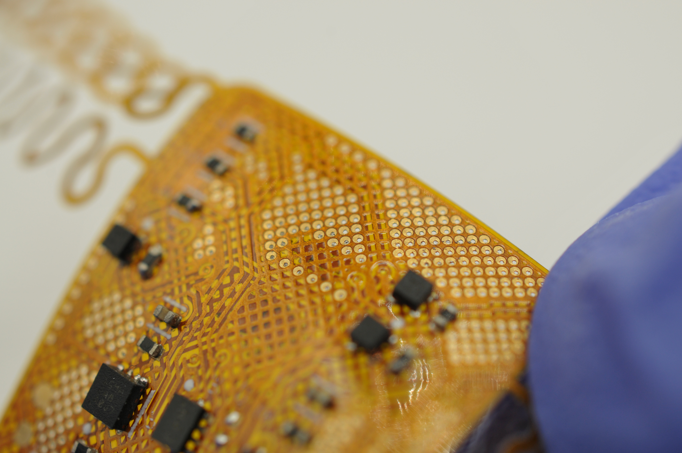
results/revision/photo/DSC_0422.JPG
