BailabUNC/LaHMo/results/revision/photo/DSC_0423.JPG

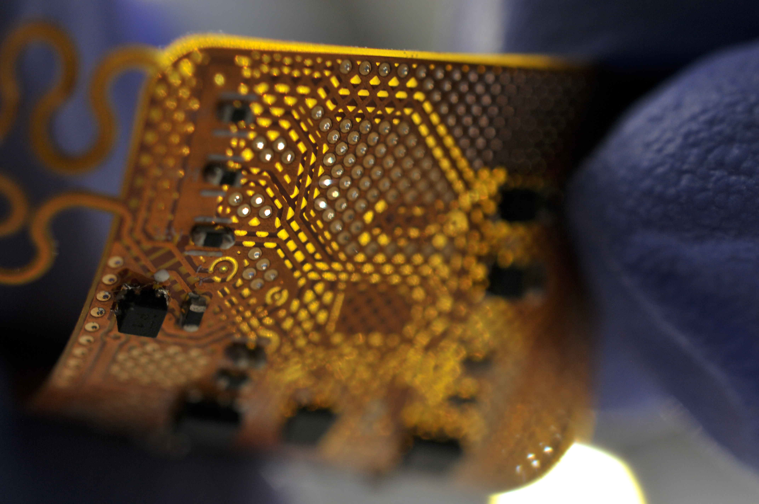
results/revision/photo/DSC_0423.JPG
