BailabUNC/LaHMo/results/revision/photo/DSC_0424.JPG

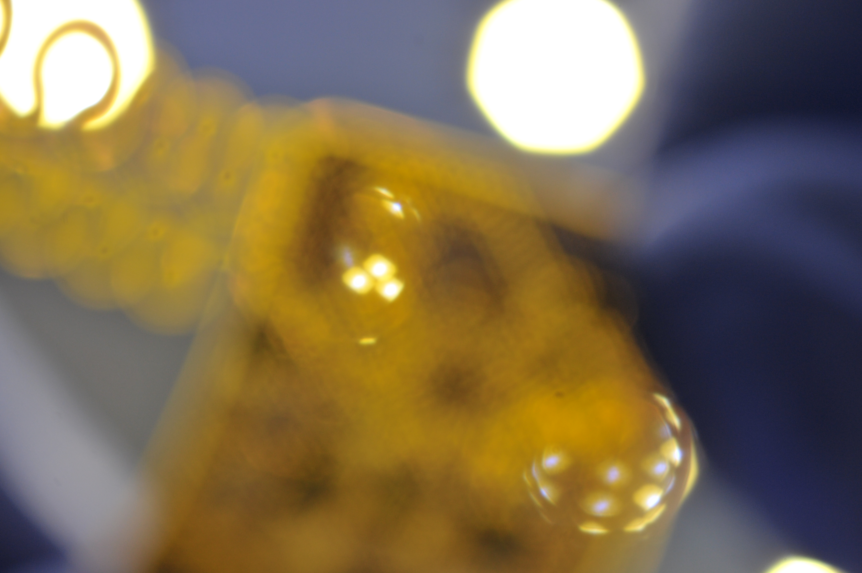
results/revision/photo/DSC_0424.JPG
