BailabUNC/LaHMo/results/revision/photo/DSC_0425.JPG

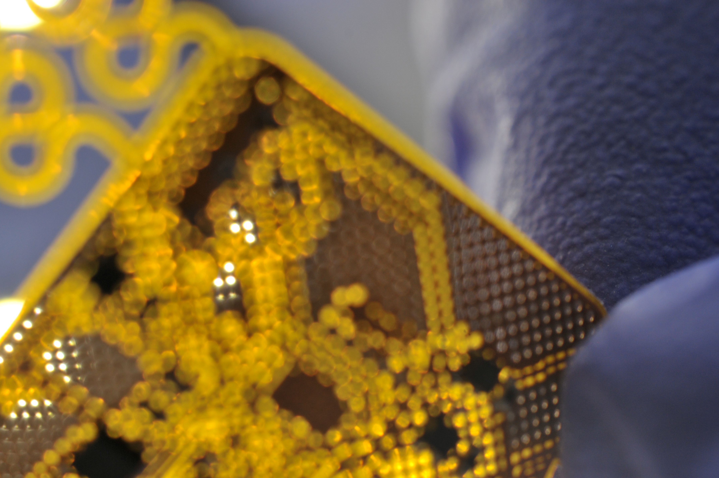
results/revision/photo/DSC_0425.JPG
