BailabUNC/LaHMo/results/revision/photo/DSC_0426.JPG

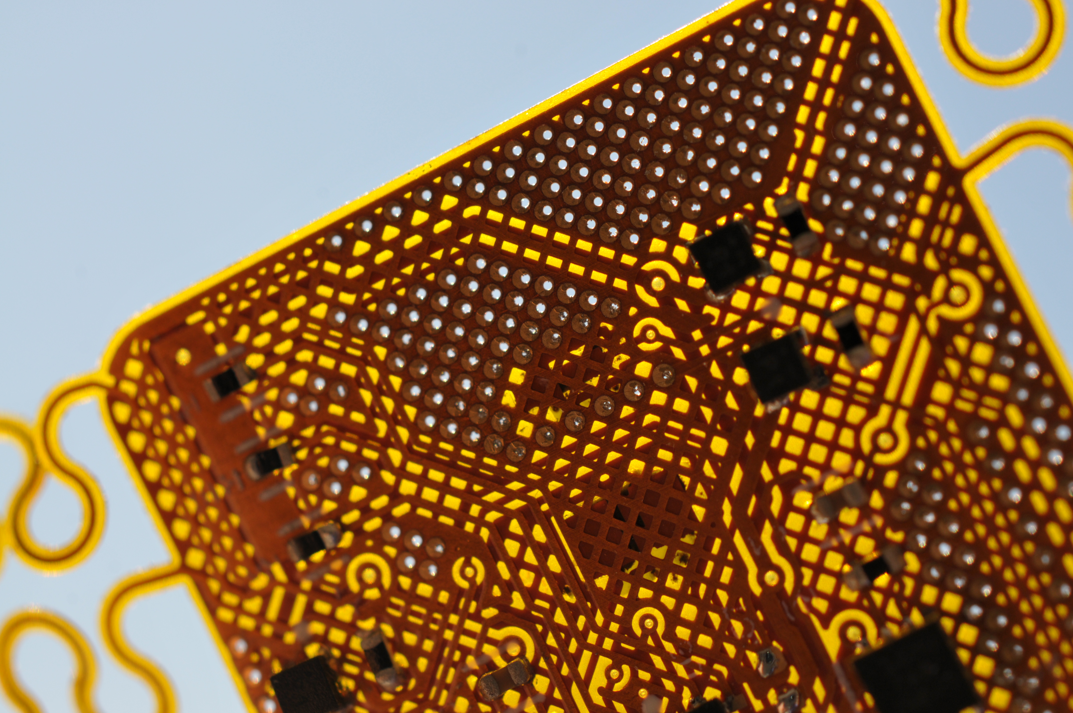
results/revision/photo/DSC_0426.JPG
