BailabUNC/LaHMo/results/revision/photo/DSC_0427.JPG

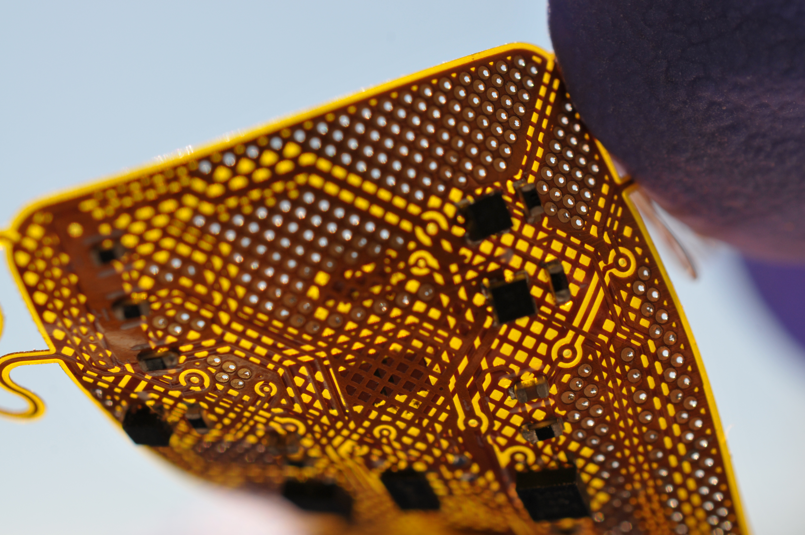
results/revision/photo/DSC_0427.JPG
