BailabUNC/LaHMo/results/revision/photo/DSC_0428.JPG

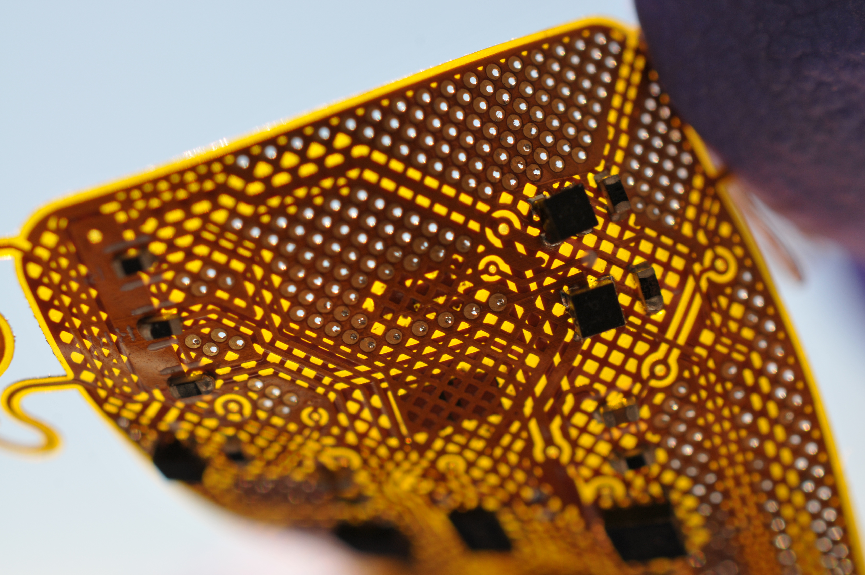
results/revision/photo/DSC_0428.JPG
