BailabUNC/LaHMo/results/revision/photo/DSC_0430.JPG

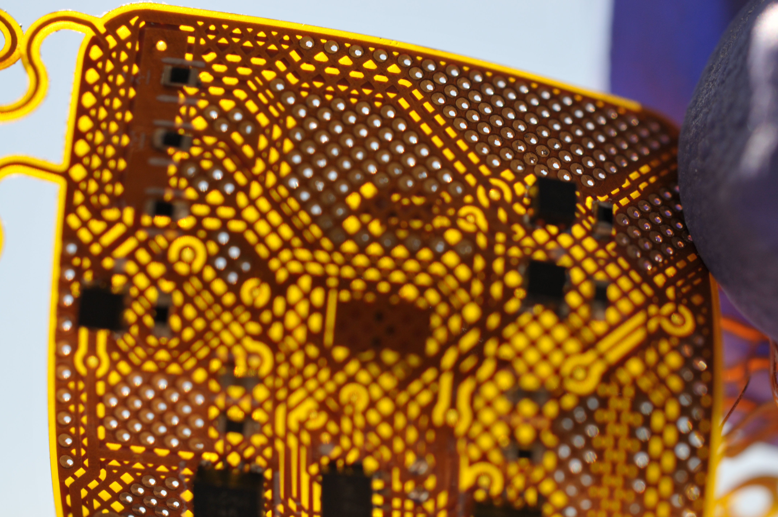
results/revision/photo/DSC_0430.JPG
