BailabUNC/LaHMo/results/revision/photo/DSC_0431.JPG

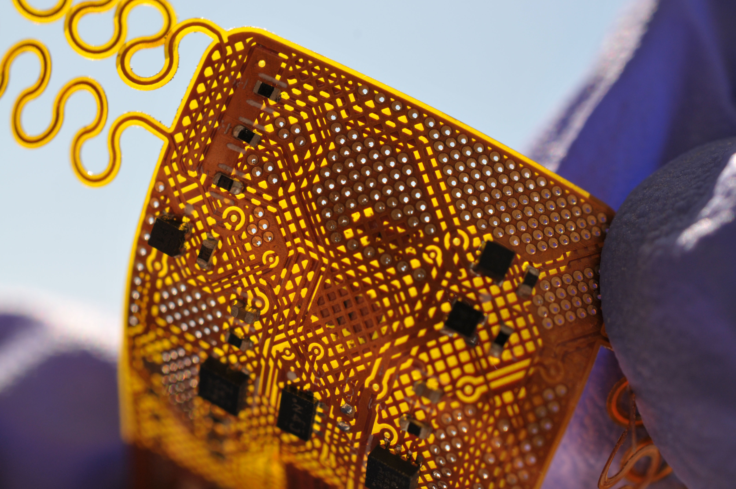
results/revision/photo/DSC_0431.JPG
