BailabUNC/LaHMo/results/si/flat.6.jpg

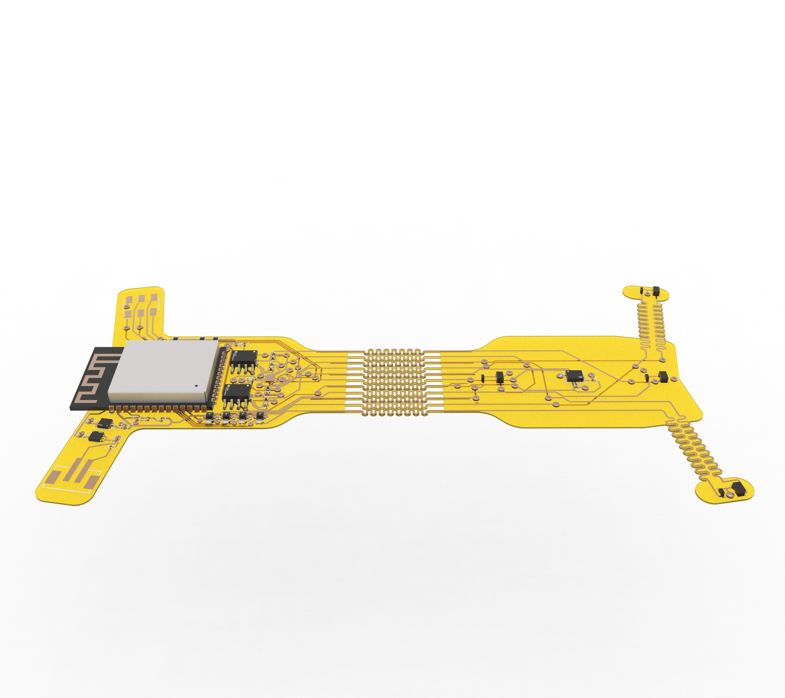
results/si/flat.6.jpg
