BailabUNC/LaHMo/results/si/gaussian_vs_lambertian.png

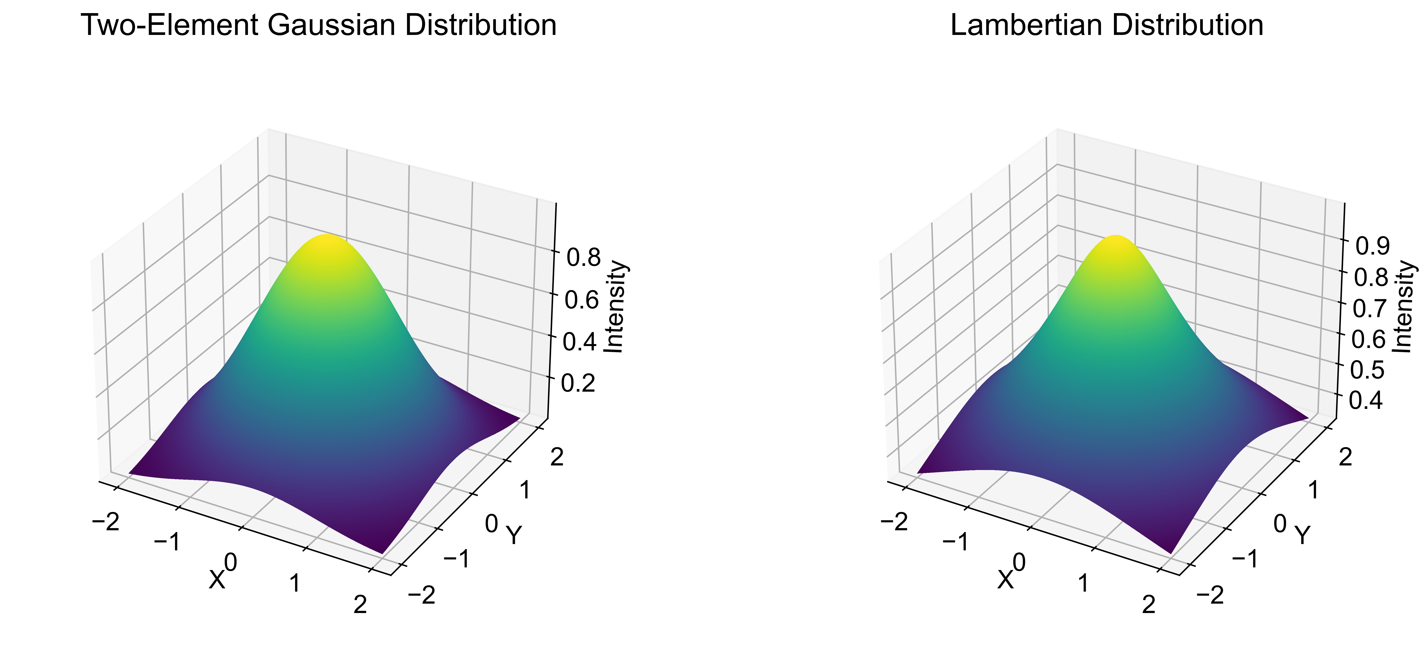
results/si/gaussian_vs_lambertian.png
