BailabUNC/LaHMo/results/videos/basketball/1.jpg

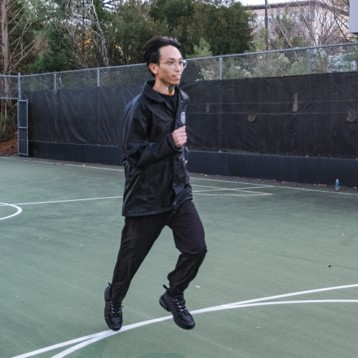
results/videos/basketball/1.jpg
