BailabUNC/LaHMo/results/videos/basketball/2.jpg

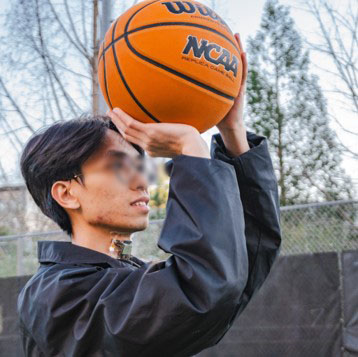
results/videos/basketball/2.jpg
