BailabUNC/LaHMo/results/videos/basketball/3.jpg

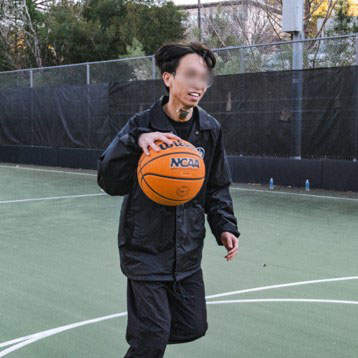
results/videos/basketball/3.jpg
