BailabUNC/LaHMo/results/videos/basketball/4.jpg

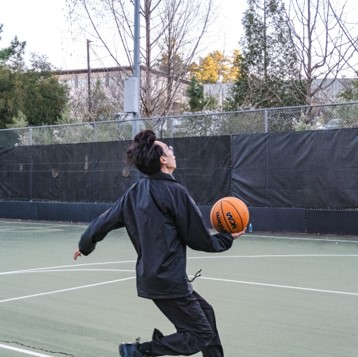
results/videos/basketball/4.jpg
