BailabUNC/LaHMo/results/videos/closeup/1.png

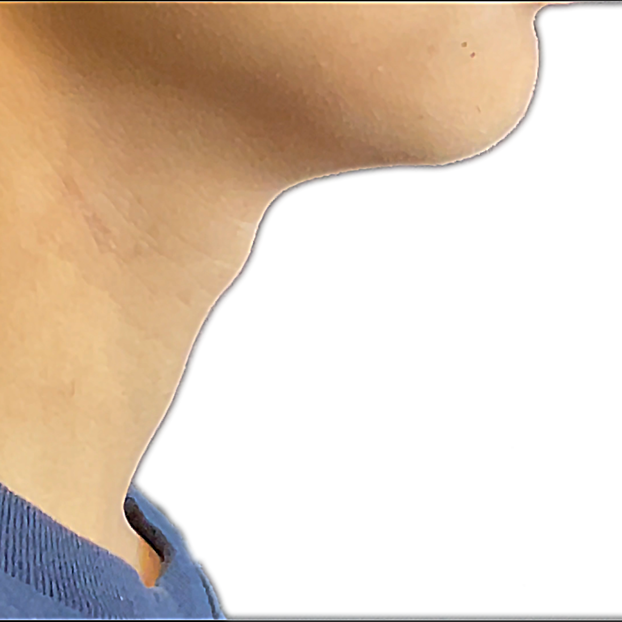
results/videos/closeup/1.png
