BailabUNC/LaHMo/results/videos/closeup/fig5b.png

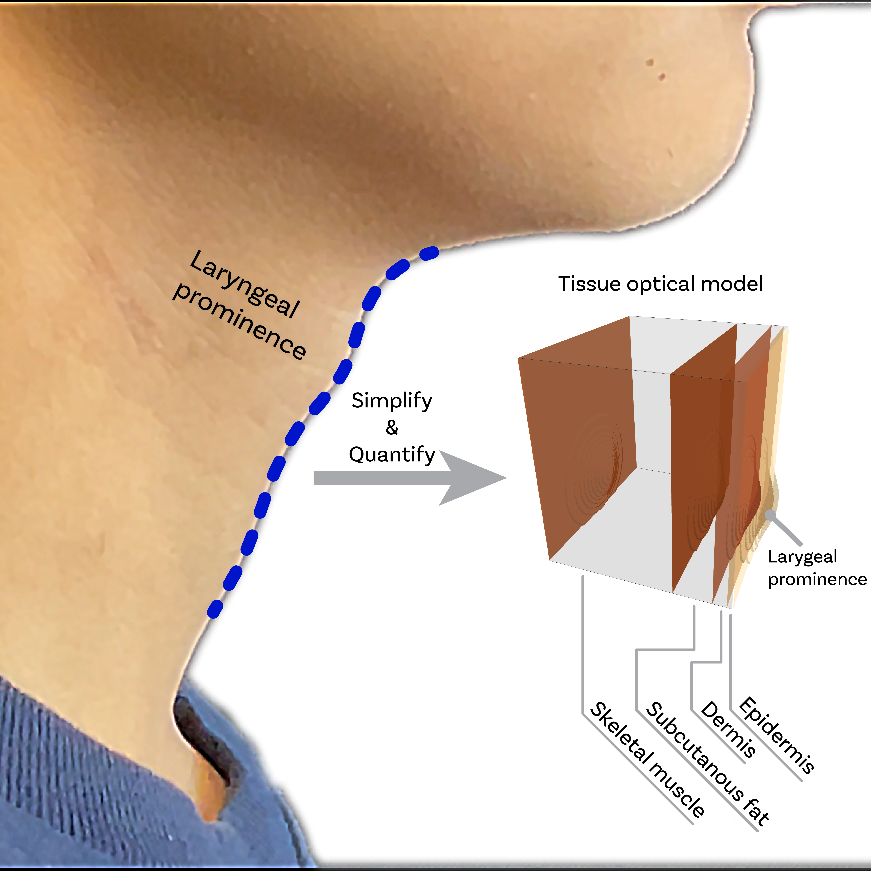
results/videos/closeup/fig5b.png
