BailabUNC/LaHMo/results/videos/closeup/monte-carlo diagram.png

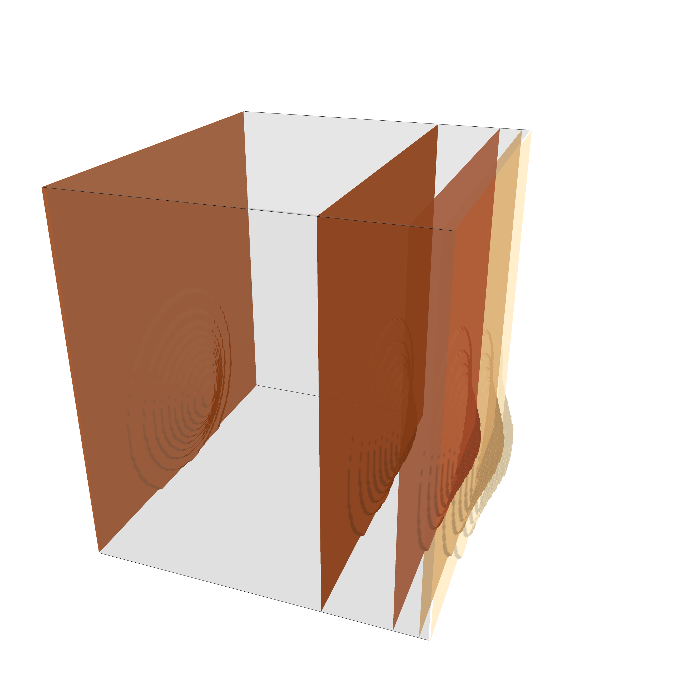
results/videos/closeup/monte-carlo diagram.png
