BailabUNC/LaHMo/results/videos/multi-modal/box.png

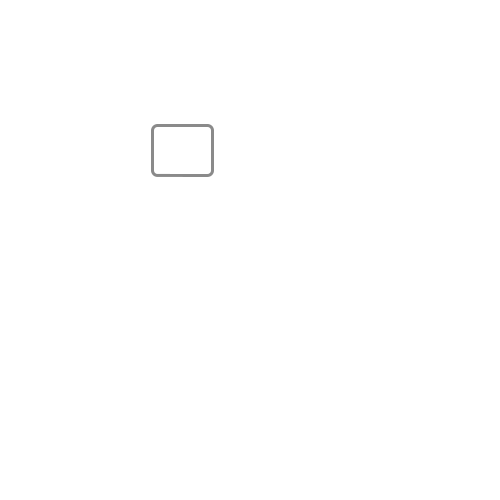
results/videos/multi-modal/box.png
