BailabUNC/LaHMo/results/videos/multi-modal/progress bar.png

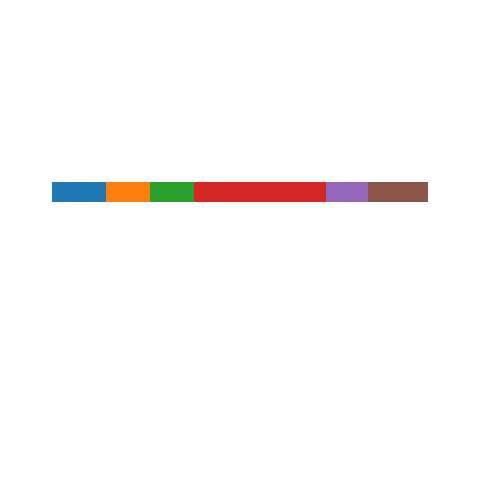
results/videos/multi-modal/progress bar.png
