BailabUNC/LaHMo/results/videos/multi-modal/Screenshot 2023-11-22 115138.png

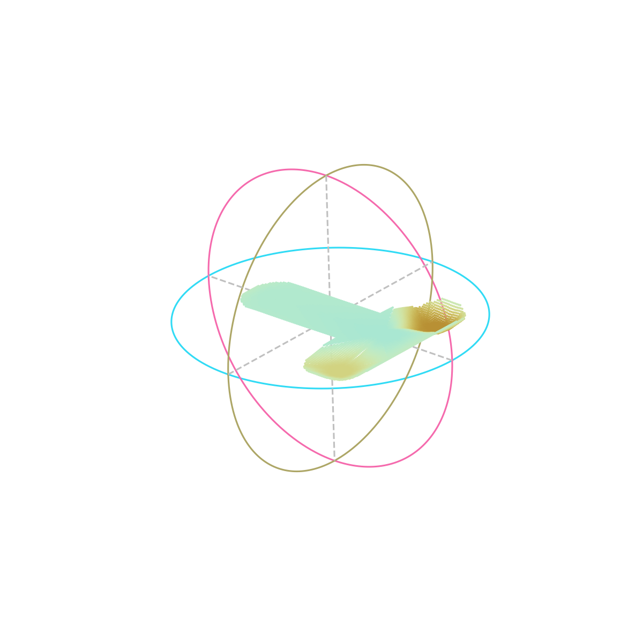
results/videos/multi-modal/Screenshot 2023-11-22 115138.png
